lhongyi-ai/AI_Goggles/v2_chipdown/reports/changed_files.md

# Phase 1 Changed Files

Audit-generated files only. No KiCad schematic/footprint/PCB edits were made in Phase 1.

- `v2_chipdown/config/hardware_mechanical_database.yaml`
- `v2_chipdown/config/hardware_mechanical_database.csv`
- `v2_chipdown/reports/design_review.md`
- `v2_chipdown/reports/mechanical_open_items.md`
- `v2_chipdown/reports/mechanical_freeze_matrix.csv`
- `v2_chipdown/reports/mechanical_freeze_matrix.xlsx`
- `v2_chipdown/reports/footprint_audit.csv`
- `v2_chipdown/reports/symbol_to_footprint_mapping.csv`
- `v2_chipdown/reports/interconnect_matrix.csv`
- `v2_chipdown/reports/interconnect_matrix.md`
- `v2_chipdown/reports/phase_reports/phase_1_audit.md`
- `v2_chipdown/reports/phase_reports/phase_2_supplier_data_freeze.md`
- `v2_chipdown/reports/phase_reports/phase_3_database_pdf_report.md`
- `v2_chipdown/reports/phase_reports/phase_4_kicad_update_decision.md`
- `v2_chipdown/reports/phase_reports/phase_5_release_gate.md`
- `v2_chipdown/reports/drc_report.txt`
- `v2_chipdown/reports/schematic_diff.md`
- `v2_chipdown/reports/engineering_reviews/*.md`
- `v2_chipdown/reports/output/mechanical_freeze/*`
- `v2_chipdown/reports/AI_Glasses_Hardware_Dimensions_and_Performance_V2.3.md`
- `v2_chipdown/reports/output/AI_Glasses_Hardware_Dimensions_and_Performance_V2.3.pdf`
