lhongyi-ai/AI_Goggles/v2_chipdown/reports/drc_report.txt

DRC report generated by Phase 1 audit on 2026-07-01

NOT RUN: V2 chipdown project currently has no .kicad_pcb file.
This is intentional: formal PCB placement/routing is blocked by Gate 0 / G00F.
A real DRC can only be run after the no-route floorplan or formal PCB file exists.

Current available electrical evidence:
- v2_chipdown/reports/erc.report.txt: 0 errors / 0 warnings on 2026-07-01T01:26:33.
- kicad-cli was not available in this shell session, so ERC was not rerun in this phase.
