lhongyi-ai/AI_Goggles/v2_chipdown/reports/mechanical_open_items.md

# V2.3 Mechanical Open Items

Generated: 2026-07-01

所有条目遵守同一规则：没有 exact MPN、package drawing、pinout、land pattern 和最大高度时，不允许进入 release-ready footprint 或正式 layout。

| Item | Current value | Why it is not frozen | Missing document | Responsible party | Supplier question | Blocking effect | Closure condition | Deadline priority |
|---|---|---|---|---|---|---|---|---|
| RK806S-5 package / height | TBD | exact package/height missing | Rockchip/Radxa PMIC drawing | EE | 请提供 RK806S-5 封装图、推荐 land pattern、最大高度、热焊盘和参考电源时序。 | Blocks PMIC placement/height/rail layout | Official package drawing + land pattern + rail sequence reviewed | P0 |
| LPDDR4X exact MPN / size / ball map | TBD | memory MPN not selected | LPDDR vendor datasheet + ball map | EE/Sourcing | 请给出 Radxa/Rockchip 已验证 4GB LPDDR4X AVL 料号、封装和 ball map。 | Blocks DDR escape and board layer proof | MPN + package + ball map + DDR topology + length report | P0 |
| eMMC exact MPN / package | TBD | eMMC MPN not selected | eMMC datasheet/package drawing | EE/Sourcing | 请给出 32GB eMMC 5.1 AVL 料号、封装、VCC/VCCQ 和 boot validation。 | Blocks boot/storage layout | MPN + package + BSP boot validation | P0 |
| IMX415 lens / PCB / FPC / total Z | Current schematic custom module; V2.3 PDF proposes Radxa AS001 32.5 x 32.5 x 18.0 | architecture mismatch | final module drawing and pinout | EE/CAD/Supplier | 当前是否接受 32mm Radxa AS001 作为 EVT 机械基线，还是坚持 custom small FPC module？ | Blocks front frame CAD and J3 pinout | Approved module drawing + lens/FPC/mounting + schematic/BOM update if changed | P0 |
| Wi-Fi antenna | TBD | antenna SKU/keep-out not frozen | antenna vendor drawing + tune report | RF/CAD | 请提供天线尺寸、塑胶窗口、no-copper keep-out、同轴/FPC 出线和佩戴状态调谐要求。 | Blocks G14 and rear temple layout | Worn-state antenna tune + keep-out in CAD/PCB | P0 |
| BLE antenna | TBD | antenna SKU/keep-out not frozen | antenna vendor drawing + tune report | RF/CAD | 请提供 BLE 天线尺寸、净空和 nRF 匹配网络要求。 | Blocks left rear layout | Antenna SKU + keep-out + matching + tune report | P0 |
| main speaker | TBD | MPN/cavity/magnet unknown | speaker datasheet + acoustic cavity drawing | Acoustic/CAD | 请提供 8ohm 0.5-1W speaker 的长宽高、磁体、出音孔、声腔和防水网要求。 | Blocks right rear speaker/RF/battery layout | Speaker MPN + cavity + antenna magnet clearance passed | P0 |
| optional second speaker | DNP | not needed in EVT-A but may consume volume | speaker decision | PM/Acoustic | EVT-A 是否删除左侧第二 speaker 机械预留？ | May block left battery/BLE antenna if kept | DNP exclusion confirmed or cavity allocated | P1 |
| vibration motor | DNP | DNP, no MPN | motor datasheet | PM/ME | EVT-A 是否完全删除马达预留？ | Can disturb IMU/mic and consume rear volume | DNP exclusion confirmed or MPN/keep-out supplied | P1 |
| USB-C connector | EVT debug tail candidate | exact connector missing | USB-C connector drawing | EE/ME | 请冻结 EVT debug tail Type-C mid-mount MPN 或确认量产只用 pogo。 | Blocks debug tail mechanical opening | MPN + height + shell opening | P1 |
| magnetic pogo connector | target about 10 x 3 mm | target only | pogo supplier drawing | EE/ME | 请提供 4-6pin pogo 的针距、高度、电流、接触电阻、磁极、防汗腐蚀和寿命。 | Blocks charge/service rear layout and safety | MPN + pinout + current/fault/ESD validation | P0 |
| hinge FPC | 6-10 mm wide, 0.10-0.18 mm thick target | custom stack-up/pinout unknown | FPC vendor stack-up and impedance report | EE/ME/FPC | 请提供 fixed-temple EVT cable/FPC 方案，或 folding hinge FPC 的 pin count、铜厚、弯折半径和寿命。 | Blocks J4 current/signal integrity and hinge CAD | Pinout + current rating + impedance + bend test | P0 |
| Boost inductor | <=5 x 5 x 2 mm target | MPN/Isat/DCR/thermal unknown | inductor datasheet | EE | 请按 TPS61088、RK3576 boot/AI 峰值电流选择 L1，提供 Isat/DCR/温升。 | Blocks SOC_5V boost layout and thermal | Selected MPN passes peak/droop/thermal | P0 |
| FH26W exact pin count | 35 pin example only | final camera/audio/power split unknown | Hirose drawing + interconnect matrix | EE | 请根据 MIPI lane、PDM、I2C、GPIO、电源/GND 确认 pin count 和 contact side。 | Blocks J3 footprint and front FPC | Pin count/contact orientation + impedance checked | P0 |
| RF connector exact MPN | U.FL/I-PEX class | exact MPN/height/mating unknown | Hirose/I-PEX drawing | RF/EE | EVT 是否保留 RF debug connector？若保留，请冻结 MPN 和高度。 | Can collide with shell/antenna window | MPN + height + mating-life approved | P1 |
| system button | low-profile button/test pad | exact mechanical actuator missing | button datasheet / ID decision | EE/ME | Power/Recovery/MaskROM 是否做真实侧按键，还是全部隐藏为 pogo test pads？ | Blocks side wall openings and sealing | MPN/opening/debounce/service plan | P1 |
| battery pack drawing | 70 x 12.8 x 5.6 mm envelope | supplier max/tolerance/swell not official | cell/pack drawing + certs | Battery supplier | 请提供最大尺寸、公差、极耳/线材/PCM/NTC位置、膨胀、IR、倍率和认证。 | Blocks battery bay and 1S2P safety | Supplier drawing + dummy/real-cell fit test | P0 |
| battery tab and cable exit | TBD | tab/cable direction unknown | battery pack drawing | Battery supplier/CAD | 请明确极耳/出线方向和最小弯折/应力释放。 | Can collide with speaker/FPC/pogo | Pack drawing + strain-relief CAD | P0 |
| battery NTC | 10k NTC TBD curve | B-value/package/placement unknown | NTC datasheet + charger config | EE/Battery | 请确认 10k NTC B 值、封装/探头形式、贴附位置和 nPM1300 JEITA 配置。 | Blocks charge safety | Curve + nPM1300 config + per-cell placement | P0 |
| battery protection | pack PCM baseline or BQ2970 DNP fallback | single protection scheme not frozen | pack PCM spec or BQ2970 suffix/MOSFET | EE/Battery | 请确认用供应商 PCM 还是板上 BQ2970+MOSFET，不允许两套冲突。 | Blocks pack fault behavior and BOM | One protection scheme selected and tested | P0 |
| all connector mating heights | mixed TBD | J1/J3/J4/J5/USB heights incomplete | connector drawings | EE/ME | 请提供所有连接器 mating height、stiffener/FPC厚度和装配方向。 | Blocks Z-height and shell closure | All connector 3D envelopes in CAD | P0 |
