lhongyi-ai/AI_Goggles/v2_chipdown/mechanical_3d/reports/z_stack_report.md

# Z-stack report

| Section | Stack / max height | Status |
|---|---:|---|
| RK806S-5 | 0.90 mm body + solder + clearance | package candidate, sequence HOLD |
| eMMC KLMAG1JENB-B041 | 0.80 mm body + solder + clearance | candidate, BSP validation HOLD |
| FCU760K | 2.00 mm module + clearance | HOLD pending Quectel design package |
| Boost inductor XGL4020 | 2.00 mm + keep-out below | HOLD pending thermal/droop |
| Speaker CMS-15113 | 3.00 mm + foam/cavity | acoustic EVT HOLD |
| Battery envelope | 5.60 mm max + supplier swell/foam | HOLD supplier pack drawing |
| IMX415 camera | target <=9.5 mm total Z | TBD, not released for tooling |
| Hard components | >=0.3 mm worst-case clearance | rule carried into CAD checks |
