lhongyi-ai/AI_Goggles/v2_chipdown/reports/engineering_reviews/mass_and_balance.md

# Mass And Balance Review

Verdict: **HOLD**.

- Left temple mass: BT2 about 6 g estimated plus AON PCB; exact mass TBD.
- Right temple mass: BT1 about 6 g estimated plus RK3576 compute, Wi-Fi and speaker, likely heavier than left.
- Front frame mass: camera/lens choice dominates. Radxa AS001-style 32 mm board is much larger than a custom small FPC module.
- Center of gravity: right front compute pod may pull glasses forward/right unless left mass or frame geometry balances it.
- Left-right imbalance: target should be measured with dummy cells/PCBs/speaker/camera before ID tooling.
- Action: create mass spreadsheet once MPNs, PCBs and shell CAD have weights.
