lhongyi-ai/AI_Goggles/v2_chipdown/reports/phase_reports/phase_1_audit.md

# Phase 1 Audit Report

Generated: 2026-07-01

Scope: audit only. No KiCad schematic, symbol, footprint, PCB or 3D model files were modified by this phase.

## Evidence Reviewed

- Current schematic/BOM source: `v2_chipdown/scripts/chipdown_bom.py`.
- Current KiCad schematic: `v2_chipdown/hardware/ai_glasses_v2_chipdown.kicad_sch`.
- Existing ERC report: `v2_chipdown/reports/erc.report.txt` shows 0 errors / 0 warnings on 2026-07-01T01:26:33.
- Existing Phase 1.5 floorplan render/report.
- Symbol/footprint audit: `v2_chipdown/reports/symbol_to_footprint_mapping.csv`.
- Interconnect audit: `v2_chipdown/reports/interconnect_matrix.csv` and `.md`.
- Attached dimensions PDFs: `/Users/stanley/Downloads/AI_Glasses_Hardware_Dimensions_V2.2 (3).pdf` and `/Users/stanley/Downloads/AI_Glasses_Hardware_Dimensions_V2.3.pdf`.
- Local HOLD closure pack under `AI_Glasses_HOLD_Closure_Pack/`.

## Database Status Counts

| Status | Count |
|---|---|
| DNP | 19 |
| Fit | 39 |
| HOLD | 15 |
| PROVISIONAL | 16 |
| TBD | 9 |

## Phase 1 Verdict

- Schematic is useful for review and procurement, but PCB layout is **HOLD**.
- Major blockers: left side/sections missing, compute routability unproven, 1S2P/J4 safety not proven, RF/speaker/battery/camera mechanical data incomplete.
- The external V2.3 dimensions PDF camera baseline is not fully aligned with the current schematic because U14 is still a custom IMX415 FPC module in HOLD.

## Next Phase Gate

Do not enter Phase 2 freeze or Phase 4 KiCad modification until supplier documents are gathered for the P0 open items, especially RK806S, LPDDR4X, eMMC, battery pack, J3/J4, antennas, speaker and camera module.
