lhongyi-ai/AI_Goggles/v2_chipdown/reports/phase_reports/phase_3_database_pdf_report.md

# Phase 3 Database And PDF Report

Generated: 2026-07-01

Verdict: **PASS WITH CONDITIONS** for documentation generation, **HOLD** for mechanical freeze.

The single source used by reports is `v2_chipdown/config/hardware_mechanical_database.yaml`, generated from the current schematic/BOM plus conservative source overlays.

## Generated Database / Report Artifacts

| Artifact | Purpose |
|---|---|
| hardware_mechanical_database.yaml/csv | source-bound dimensions, power notes, statuses and next actions |
| AI_Glasses_Hardware_Dimensions_and_Performance_V2.3.md/pdf | human-readable hardware dimension/performance report with component cards |
| AI_Glasses_V2_3_Mechanical_Views.svg/png/pdf | 16 required schematic-aligned mechanical views |
| mechanical_freeze_matrix.xlsx/csv | P0/P1 open items and closure conditions |

Current status counts:

| Status | Count |
|---|---|
| DNP | 19 |
| Fit | 39 |
| HOLD | 15 |
| PROVISIONAL | 16 |
| TBD | 9 |
