lhongyi-ai/AI_Goggles/v2_chipdown/reports/phase_reports/phase_4_kicad_update_decision.md

# Phase 4 KiCad Update Decision

Generated: 2026-07-01

Verdict: **HOLD / NO KiCad EDITS IN THIS RUN**.

Reason: the prompt explicitly forbids release-ready footprint or schematic changes when exact MPN, package drawing, pinout, land pattern and max height are missing. The current project still has P0 blockers for RK806S, LPDDR4X, eMMC, camera module, antennas, speaker, pogo, J3/J4, boost inductor and battery pack drawing.

## KiCad Audit Evidence Generated

| Artifact | Result |
|---|---|
| symbol_to_footprint_mapping.csv | 96 schematic components mapped to current footprint fields and release-readiness status |
| footprint_audit.csv | NOT_FOR_FAB requirements flagged for VERIFY/HOLD/TBD/DNP items |
| interconnect_matrix.csv/md | 127 schematic nets with endpoints, domains, crossing status and layout rules |
| schematic_diff.md | confirms no KiCad schematic edits were made |

Allowed future KiCad action: create HOLD placeholders or a no-route mechanical floorplan only after the team approves that output as non-fabrication evidence. Do not replace current functional symbols with vendor pin-level symbols until ball maps/pinouts are official.
