lhongyi-ai/AI_Goggles/v2_chipdown/reports/phase_reports/phase_5_release_gate.md

# Phase 5 ERC / DRC / 3D / Release Gate

Generated: 2026-07-01

Overall verdict: **NOT READY FOR PCB LAYOUT**.

## Electrical / Layout Checks

| Check | Status | Evidence / blocker |
|---|---|---|
| ERC | PASS on existing report | `v2_chipdown/reports/erc.report.txt` shows 0 errors / 0 warnings on 2026-07-01T01:26:33; `kicad-cli` unavailable here, so not rerun |
| DRC | NOT RUN | V2 has no `.kicad_pcb`; DRC requires at least a no-route or formal PCB file |
| 3D collision | NOT RUN | No verified STEP/3D model set aligned to V2 KiCad footprints |
| Thermal | HOLD | RK3576/RK806/TPS61088 heat path and battery isolation require CAD/thermal review |
| RF | HOLD | Wi-Fi/BLE antenna SKU, keep-out and worn-state tune missing |
| Battery/J4 safety | HOLD | 1S2P branch protection/current capacity/fault behavior not frozen |

PCB layout may start only as a controlled floorplan study. Formal routing/fab release remains blocked until all P0 closure conditions in `mechanical_open_items.md` are closed.
