lhongyi-ai/AI_Goggles/docs/csi3_imx415_audit_2026-06-28.md

# CSI3 / IMX415 Audit

Date: 2026-06-28

Native sources used:

- `data/radxa_cm4_pinout_v1.20.xlsx`
- `CM4_IMX415_design_files/Radxa_Camera_4K_31pin_pinout.csv`
- `scripts/cm4_pinmap.py`
- `scripts/carrier_bom.py`
- `hardware/ai_glasses_carrier.kicad_sch` generated from `scripts/carrier_bom.py`

## Schematic Gate Summary

| Gate | Status | Evidence |
| --- | --- | --- |
| J2 Pin 1-31 pinout | PASS | Checked against Radxa Camera 4K 31-pin CSV and `scripts/carrier_bom.py`. |
| MIPI lane order | PASS | `MDP/MDN1..4` map to CSI3 D0..D3; `MCP/MCN` map to CSI3 clock. |
| P/N polarity | PASS | Every FPC `P` signal lands on `_P`, every `N` signal lands on `_N`. |
| I2C/MCLK/RESET | PASS | SCL/SDA/MCLK/RESET_N map to verified CM4 pins and functions below. |
| Voltage domains | PASS | Control IO is 1.8V; J2 supplies are +CAM_3V3 and +5V_SYS. |
| Power and NC pins | PASS | GND, VCC3.3V, VCC5V and NC pins are explicitly checked below. |
| ERC warnings | PASS | 0 ERC violation(s). There are no active ERC warnings to explain. |

## J2 Pin 1-31 Electrical Check

| Pin | FPC signal | Schematic label | Board net | Role | Voltage / domain | Result |
| ---: | --- | --- | --- | --- | --- | --- |
| 1 | `GND` | `GND` | `GND` | ground | GND | PASS. |
| 2 | `MDN4` | `MDN4` | `MIPI_CSI3_D3_N` | mipi_lane | CSI3 D-PHY | PASS. Lane 3 negative. |
| 3 | `MDP4` | `MDP4` | `MIPI_CSI3_D3_P` | mipi_lane | CSI3 D-PHY | PASS. Lane 3 positive. |
| 4 | `GND` | `GND` | `GND` | ground | GND | PASS. |
| 5 | `MDN3` | `MDN3` | `MIPI_CSI3_D2_N` | mipi_lane | CSI3 D-PHY | PASS. Lane 2 negative. |
| 6 | `MDP3` | `MDP3` | `MIPI_CSI3_D2_P` | mipi_lane | CSI3 D-PHY | PASS. Lane 2 positive. |
| 7 | `GND` | `GND` | `GND` | ground | GND | PASS. |
| 8 | `NC` | `NC` | `NC` | no_connect | unconnected | PASS. |
| 9 | `NC` | `NC` | `NC` | no_connect | unconnected | PASS. |
| 10 | `GND` | `GND` | `GND` | ground | GND | PASS. |
| 11 | `MDN2` | `MDN2` | `MIPI_CSI3_D1_N` | mipi_lane | CSI3 D-PHY | PASS. Lane 1 negative. |
| 12 | `MDP2` | `MDP2` | `MIPI_CSI3_D1_P` | mipi_lane | CSI3 D-PHY | PASS. Lane 1 positive. |
| 13 | `GND` | `GND` | `GND` | ground | GND | PASS. |
| 14 | `MDN1` | `MDN1` | `MIPI_CSI3_D0_N` | mipi_lane | CSI3 D-PHY | PASS. Lane 0 negative. |
| 15 | `MDP1` | `MDP1` | `MIPI_CSI3_D0_P` | mipi_lane | CSI3 D-PHY | PASS. Lane 0 positive. |
| 16 | `GND` | `GND` | `GND` | ground | GND | PASS. |
| 17 | `MCN` | `MCN` | `MIPI_CSI3_CLK_N` | mipi_clock | CSI3 D-PHY | PASS. Clock negative. |
| 18 | `MCP` | `MCP` | `MIPI_CSI3_CLK_P` | mipi_clock | CSI3 D-PHY | PASS. Clock positive. |
| 19 | `GND` | `GND` | `GND` | ground | GND | PASS. |
| 20 | `MCLK` | `MCLK` | `CAM_MCLK` | clock | 1.8V | PASS. CM4 CAM_CLK2_OUT_M0. |
| 21 | `GND` | `GND` | `GND` | ground | GND | PASS. |
| 22 | `NC` | `NC` | `NC` | no_connect | unconnected | PASS. |
| 23 | `NC` | `NC` | `NC` | no_connect | unconnected | PASS. |
| 24 | `SCL` | `SCL` | `CAM_I2C_SCL` | i2c | 1.8V | PASS. Pulled up to +1V8 on carrier. |
| 25 | `SDA` | `SDA` | `CAM_I2C_SDA` | i2c | 1.8V | PASS. Pulled up to +1V8 on carrier. |
| 26 | `NC` | `NC` | `NC` | no_connect | unconnected | PASS. |
| 27 | `RESET` | `RESET_N` | `CAM_RST_n` | reset | 1.8V | PASS. Active-low reset. |
| 28 | `VCC3.3V` | `VCC3.3V` | `+CAM_3V3` | power | 3.3V | PASS. Generated by camera low-noise LDO. |
| 29 | `VCC3.3V` | `VCC3.3V` | `+CAM_3V3` | power | 3.3V | PASS. Generated by camera low-noise LDO. |
| 30 | `VCC5V` | `VCC5V` | `+5V_SYS` | power | 5V | PASS. System 5V rail with local decoupling. |
| 31 | `VCC5V` | `VCC5V` | `+5V_SYS` | power | 5V | PASS. System 5V rail with local decoupling. |

## Lane Mapping

| Camera FPC | Board net | CM4 pin | CM4 XLSX primary net | Required RK3576 function | Result |
| --- | --- | ---: | --- | --- | --- |
| pin 18 `MCP` | `MIPI_CSI3_CLK_P` | 129 | `MIPI_DPHY_CSI3_RX_CLKP` | `MIPI_DPHY_CSI3_RX_CLKP` | PASS. |
| pin 17 `MCN` | `MIPI_CSI3_CLK_N` | 127 | `MIPI_DPHY_CSI3_RX_CLKN` | `MIPI_DPHY_CSI3_RX_CLKN` | PASS. |
| pin 15 `MDP1` | `MIPI_CSI3_D0_P` | 117 | `MIPI_DPHY_CSI3_RX_D0P` | `MIPI_DPHY_CSI3_RX_D0P` | PASS. |
| pin 14 `MDN1` | `MIPI_CSI3_D0_N` | 115 | `MIPI_DPHY_CSI3_RX_D0N` | `MIPI_DPHY_CSI3_RX_D0N` | PASS. |
| pin 12 `MDP2` | `MIPI_CSI3_D1_P` | 123 | `MIPI_DPHY_CSI3_RX_D1P` | `MIPI_DPHY_CSI3_RX_D1P` | PASS. |
| pin 11 `MDN2` | `MIPI_CSI3_D1_N` | 121 | `MIPI_DPHY_CSI3_RX_D1N` | `MIPI_DPHY_CSI3_RX_D1N` | PASS. |
| pin 6 `MDP3` | `MIPI_CSI3_D2_P` | 135 | `MIPI_DPHY_CSI4_RX_D0P` | `MIPI_DPHY_CSI3_RX_D2P` | PASS. CM4 pinout primary net is CSI4_D0P; function list also exposes CSI3_D2P. |
| pin 5 `MDN3` | `MIPI_CSI3_D2_N` | 133 | `MIPI_DPHY_CSI4_RX_D0N` | `MIPI_DPHY_CSI3_RX_D2N` | PASS. CM4 pinout primary net is CSI4_D0N; function list also exposes CSI3_D2N. |
| pin 3 `MDP4` | `MIPI_CSI3_D3_P` | 141 | `MIPI_DPHY_CSI4_RX_D1P` | `MIPI_DPHY_CSI3_RX_D3P` | PASS. CM4 pinout primary net is CSI4_D1P; function list also exposes CSI3_D3P. |
| pin 2 `MDN4` | `MIPI_CSI3_D3_N` | 139 | `MIPI_DPHY_CSI4_RX_D1N` | `MIPI_DPHY_CSI3_RX_D3N` | PASS. CM4 pinout primary net is CSI4_D1N; function list also exposes CSI3_D3N. |

## Control Voltage Audit

| Signal | CM4 pin | CM4 net | Function | Voltage conclusion | Result |
| --- | ---: | --- | --- | --- | --- |
| `I2C_CAM_SCL` | 80 | `I2C0_SCL_M1_TP` | `I2C0_SCL_M1` | 1.8V; board pulls control I/O to +1V8 where applicable | PASS |
| `I2C_CAM_SDA` | 82 | `I2C0_SDA_M1_TP` | `I2C0_SDA_M1` | 1.8V; board pulls control I/O to +1V8 where applicable | PASS |
| `CAM_MCLK` | 59 | `MIPI_CSI3_CAM_CLKOUT_1V8` | `CAM_CLK2_OUT_M0` | 1.8V; board pulls control I/O to +1V8 where applicable | PASS |
| `CAM_RST_n` | 143 | `MIPI_CAM3_PDN_1V8` | `GPIO3_C5` | 1.8V; board pulls control I/O to +1V8 where applicable | PASS |

## Conclusions

- The 4-lane camera connection is a CSI3 endpoint, but CM4 pins 133/135/139/141 are named as CSI4 primary nets in the pinout while also listing CSI3 D2/D3 functions. Treat this as a documented CSI3/CSI4 mux alias, and mirror the same lane order in Device Tree.
- Camera I2C, MCLK and RESET control are all carried as 1.8 V signals in the current source plan.
- `CAM_RST_n` is the project net name and is active-low. The Radxa Camera 4K FPC pin 27 label is `RESET`; the schematic symbol marks it as `RESET_N`.
- Radxa Camera 4K exposes RESET but no PWDN pin in the local 31-pin pinout CSV.
- J2 pins 28/29 are tied to `+CAM_3V3`; J2 pins 30/31 are tied to `+5V_SYS`. Both rails are present because the Radxa Camera 4K 31-pin pinout exposes both supplies.
- J2 pins 8/9/22/23/26 are intentional `NC` pins and the generated KiCad schematic emits no-connect markers for them.

## DEFERRED_TO_PRE_LAYOUT

These items are explicitly not closed by the schematic electrical gate:

| ID | Item | Status |
| --- | --- | --- |
| `AC006_PHYSICAL_VALIDATION` | AC006实物验证 | `DEFERRED_TO_PRE_LAYOUT` |
| `FPC_CONTACT_SIDE` | FPC接触面 | `DEFERRED_TO_PRE_LAYOUT` |
| `FPC_INSERTION_DIRECTION` | 插入方向 | `DEFERRED_TO_PRE_LAYOUT` |
| `J2_PIN1_PHYSICAL_CHECK` | Pin 1实体核对 | `DEFERRED_TO_PRE_LAYOUT` |
| `J2_1TO1_PRINT_CHECK` | 1:1打印 | `DEFERRED_TO_PRE_LAYOUT` |
| `J2_COUPON_TEST` | Coupon测试 | `DEFERRED_TO_PRE_LAYOUT` |
| `FPC_BEND_AND_ENCLOSURE_PATH` | FPC弯折和外壳路径 | `DEFERRED_TO_PRE_LAYOUT` |
