lhongyi-ai/AI_Goggles/AI_Glasses_HOLD_Closure_Pack/00_Index_and_Action/公开来源与需登录资料.md

# 公开来源与需登录资料

## NDP120

- Public product page: https://www.syntiant.com/products/chips-and-hardware/ndp120/
- Product Brief: included in this package.
- Avnet RASynBoard product/development platform: https://www.avnet.com/apac/products/rasynboard/
- RASynBoard GitHub hub: https://github.com/Avnet/RASynBoard-HUB
- Full datasheet/SDK/model tools: contact Syntiant or authorized distributor; access may require account/NDA.

## FCU760K

- Official product page: https://www.quectel.com/product/wi-fi-bluetooth-fcu760k/
- Official download zone: https://www.quectel.com/download-zone/
- Official hardware-design landing page: https://www.quectel.com/download/quectel_fcu760k_hardware_design_v1-2/
- Public FCC copy of FCU760K hardware design: https://fccid.io/m/e89f187a4d2a5470e689b20ec0c0dcbc1a5c297cd725fd0425162547aa3b618d.pdf
- Driver/firmware package: request from Quectel FAE/download account.

## LP451165

- Public product page: https://www.lipolbattery.com/Lithium-ion-Polymer-Battery-300mAh-for-Wearable-Camera.html
- The public page is not a full engineering datasheet and does not publish exact rate curves. Request a signed/revision-controlled PDF from the supplier.

## nPM1300 / Pack profiling

- Product page: https://www.nordicsemi.com/Products/nPM1300
- Current fuel-gauge application note: https://www.nordicsemi.com/-/media/Images/Products/PMICs/nPM1300/nan_045.pdf
- Use nPM1300 EK + nPM Fuel Gauge Board to profile the final 1S2P pack.

## IMX415

- Sony product flyer: https://www.sony-semicon.com/files/62/pdf/p-12_IMX415-AAQR_AAMR_Flyer.pdf
- Full IMX415-AAQR-C datasheet is included in this package.
- FRAMOS FSM-IMX415 module reference: https://framos.com/wp-content/uploads/2022/06/FSM-IMX415-Datasheet.pdf
