lhongyi-ai/AI_Goggles/AI_Glasses_HOLD_Closure_Pack/04_IMX415/IMX415_相机电源预算与模组索资.md

# IMX415 相机电源预算与定制模组索资

## Sony Sensor 本体数据

Sony IMX415-AAQR-C Datasheet 的 Current Consumption 表给出：

| 电源 | 典型电流 | 最大电流 |
|---|---:|---:|
| AVDD 2.9 V | 128 mA | 156 mA |
| IOVDD 1.8 V | 3 mA | 3 mA |
| DVDD 1.1 V | 187 mA | 250 mA |

测试模式为 MIPI CSI-2 4-lane、2079 Mbps、12-bit、60 fps、all-pixel。

### 功率计算

典型条件：

`2.9*0.128 + 1.8*0.003 + 1.1*0.187 = 0.5823 W`

最大电流、最大供电角：

`3.0*0.156 + 1.9*0.003 + 1.2*0.250 = 0.7737 W`

Standby 最大电流为 0.2 mA / 0.2 mA / 15.1 mA；按最大电压角约 19.1 mW。该值仍明显高于真正断电，因此休眠时应通过 Load Switch 切断相机轨。

## 重要限制

上述仅是 Sensor 芯片，不包括：

- 外部时钟/晶振。
- 模组 LDO/Buck 损耗。
- EEPROM、AF/IR-cut（若有）。
- FPC 压降和 ESD。
- 镜头相关执行器。
- 前框状态灯或其他器件。

因此定制相机模块不能用“IMX415约0.6 W”直接冻结整岛预算。

## 向相机模组供应商索取

1. 完整模组原理图或至少 Power Tree。
2. FPC pinout、连接器料号、机械图和最大高度。
3. 2-lane/4-lane支持模式和目标1080p30/60配置。
4. AVDD/IOVDD/DVDD 每轨典型、峰值和上电浪涌。
5. 时钟源、电压和电流。
6. RST/PWDN/供电时序。
7. Standby、streaming、模式切换功耗。
8. Lens FOV、畸变、M12/定焦结构、IR filter。
9. BSP sensor driver、register table、ISP tuning文件。
10. ESD/EMI和温度范围。

## EVT 测量

在每个相机轨串 Kelvin Shunt：CAM_1V1、CAM_1V8、CAM_2V9。记录：

- Power-on rush。
- Reset release。
- Idle/standby。
- 1080p30、1080p60。
- 4K30/60（仅作为边界）。
- 低照度/高增益。
- Stream off后的漏电。

## HOLD 关闭门槛

- 定制模组 MPN、机械图和 FPC pinout 冻结。
- 1080p目标模式在RK3576 BSP稳定运行。
- 三轨峰值和平均功耗实测完成。
- 断电后不存在 I2C/MIPI/GPIO 反灌。
- 前框温升和FPC压降通过。
