lhongyi-ai/AI_Goggles/v2_chipdown/docs/08_signal_dictionary.md

# 08 — Signal dictionary (generated)

> Generated 2026-07-01 from `scripts/chipdown_bom.py`. Do not hand-edit. Every row is a net-level `NET_META` record normalized by `net_meta()`.

**133 nets**. Signal attributes cover name, source, destination, direction, voltage domain, default state, pulls, powered-off behavior, debug series parts, ESD, differential pairing, pinmux, device-tree/driver owner, and isolation notes.

## Rules

- `_L` means active low. `EN` and `PGOOD` are active high.
- Any row with `Cross-domain = yes` must pass reverse-feed/off-leakage review before layout.
- Defaults marked `low (OFF)` are backed by physical pull-downs where listed in `11/12`.
- `TBD` attributes are allowed only while the owning gate remains open.

## Power nets (35)

| Net | Full name | From | To | Direction | Domain | Default | Pull | Off-high allowed | Series / ESD / Diff | Pinmux / DT / Driver | Notes |
|---|---|---|---|---|---|---|---|---|---|---|---|
| `GND` | GND | source | loads | source->loads | 0V | 0V | none / TBD | N/A | none / no / TBD / no | none / TBD / none / TBD / none / TBD | derived from endpoints; verify at the owning gate |
| `VDD_CPU` | VDD CPU | RK806S rail | loads | source->loads | RK806 rail (TBD) | off until owning regulator is enabled | none / TBD | N/A | none / no / TBD / no | none / TBD / none / TBD / none / TBD | derived from endpoints; verify at the owning gate |
| `VDD_GPU` | VDD GPU | RK806S rail | loads | source->loads | RK806 rail (TBD) | off until owning regulator is enabled | none / TBD | N/A | none / no / TBD / no | none / TBD / none / TBD / none / TBD | derived from endpoints; verify at the owning gate |
| `VDD_NPU` | VDD NPU | RK806S rail | loads | source->loads | RK806 rail (TBD) | off until owning regulator is enabled | none / TBD | N/A | none / no / TBD / no | none / TBD / none / TBD / none / TBD | derived from endpoints; verify at the owning gate |
| `VDD_LOGIC` | VDD LOGIC | RK806S rail | loads | source->loads | RK806 rail (TBD) | off until owning regulator is enabled | none / TBD | N/A | none / no / TBD / no | none / TBD / none / TBD / none / TBD | derived from endpoints; verify at the owning gate |
| `VDD_DDR` | VDD DDR | RK806S rail | loads | source->loads | RK806 rail (TBD) | off until owning regulator is enabled | none / TBD | N/A | none / no / TBD / no | none / TBD / none / TBD / none / TBD | derived from endpoints; verify at the owning gate |
| `VCC_DDRIO` | VCC DDRIO | RK806S rail | loads | source->loads | 1.8V | off until owning regulator is enabled | none / TBD | N/A | none / no / TBD / no | none / TBD / none / TBD / none / TBD | derived from endpoints; verify at the owning gate |
| `VCCIO_1V8` | VCCIO 1V8 | RK806S rail | loads | source->loads | 1.8V | off until owning regulator is enabled | none / TBD | N/A | none / no / TBD / no | none / TBD / none / TBD / none / TBD | derived from endpoints; verify at the owning gate |
| `VCC_3V3` | VCC 3V3 | RK806S rail | loads | source->loads | 3.3V | off until owning regulator is enabled | none / TBD | N/A | none / no / TBD / no | none / TBD / none / TBD / none / TBD | derived from endpoints; verify at the owning gate |
| `SOC_5V` | SOC 5V | TPS61088 boost output | loads | source->loads | 5V | off | none / TBD | N/A | none / no / TBD / no | nRF GPIO/UART + RK3576 GPIO/UART DT / power-state handshake + uart node / nRF app + Linux GPIO/UART | TPS61088 boost, gated |
| `SOC_IN` | SOC IN | RS4 from VSYS | loads | source->loads | Vbat | off until owning regulator is enabled | none / TBD | N/A | none / no / TBD / no | nRF GPIO/UART + RK3576 GPIO/UART DT / power-state handshake + uart node / nRF app + Linux GPIO/UART | derived from endpoints; verify at the owning gate |
| `WIFI_VBAT_3V3` | WIFI VBAT 3V3 | TPS22917 Wi-Fi load-switch output | loads | source->loads | 3.3V | off | none / TBD | N/A | none / no / TBD / no | none / TBD / none / TBD / none / TBD | FCU760K VBAT, load-switched |
| `WIFI_IN` | WIFI IN | RS5 from VSYS | loads | source->loads | Vbat | off until owning regulator is enabled | none / TBD | N/A | none / no / TBD / no | none / TBD / none / TBD / none / TBD | derived from endpoints; verify at the owning gate |
| `WIFI_3V3` | WIFI 3V3 | TPS62825 output | loads | source->loads | 3.3V | off | none / TBD | N/A | none / no / TBD / no | none / TBD / none / TBD / none / TBD | TPS62825 buck, gated |
| `USB_5V` | USB 5V | USB-C or magnetic pogo VBUS | loads | source->loads | 5V | ext | none / TBD | N/A | none / VBUS ESD/OV strategy required / no | none / TBD / none / TBD / none / TBD | protected VBUS into BQ25895/nPM1300 sense |
| `VSYS` | VSYS | nPM1300 power-path output | loads | source->loads | Vbat | live | none / TBD | N/A | none / no / TBD / no | none / TBD / none / TBD / none / TBD | nPM1300 power-path system node |
| `NPM_VBAT` | NPM VBAT | RS1 pack-total shunt | loads | source->loads | Vbat | live | none / TBD | N/A | none / no / TBD / no | none / TBD / none / TBD / none / TBD | nPM1300 VBAT (after RS1 total shunt) |
| `VBUS_RAW` | VBUS RAW | USB-C or magnetic pogo before input protection | loads | source->loads | 5V | ext | none / TBD | N/A | none / no / TBD / no | none / TBD / none / TBD / none / TBD | raw pogo/USB-C VBUS before eFuse/OVP |
| `AON_1V8` | AON 1V8 | nPM1300 BUCK1 | loads | source->loads | 1.8V | on | none / TBD | N/A | none / no / TBD / no | none / TBD / none / TBD / none / TBD | always-on nPM1300 BUCK1 |
| `AON_3V3` | AON 3V3 | nPM1300 BUCK2 | loads | source->loads | 3.3V | on | none / TBD | N/A | none / no / TBD / no | none / TBD / none / TBD / none / TBD | always-on nPM1300 BUCK2 |
| `AON_LSW2` | AON LSW2 | nPM1300 load switch 2 | loads | source->loads | TBD | on/live in AON mode | none / TBD | N/A | none / no / TBD / no | none / TBD / none / TBD / none / TBD | derived from endpoints; verify at the owning gate |
| `CAM_1V1_S` | CAM 1V1 S | RS7 Kelvin sense output to camera DVDD | loads | source->loads | 1.1V | off until owning regulator is enabled | none / TBD | N/A | none / no / TBD / no | none / TBD / none / TBD / none / TBD | derived from endpoints; verify at the owning gate |
| `CAM_1V8_S` | CAM 1V8 S | RS8 Kelvin sense output to camera IOVDD | loads | source->loads | 1.8V | off until owning regulator is enabled | none / TBD | N/A | none / no / TBD / no | none / TBD / none / TBD / none / TBD | derived from endpoints; verify at the owning gate |
| `CAM_2V9_S` | CAM 2V9 S | RS9 Kelvin sense output to camera AVDD | loads | source->loads | 2.9V | off until owning regulator is enabled | none / TBD | N/A | none / no / TBD / no | none / TBD / none / TBD / none / TBD | derived from endpoints; verify at the owning gate |
| `CAM_1V1` | CAM 1V1 | TPS62840 output | loads | source->loads | 1.1V | off | none / TBD | N/A | none / no / TBD / no | none / TBD / none / TBD / none / TBD | IMX415 DVDD |
| `CAM_2V9` | CAM 2V9 | TLV75529 output | loads | source->loads | 2.9V | off | none / TBD | N/A | none / no / TBD / no | none / TBD / none / TBD / none / TBD | IMX415 AVDD |
| `CAM_1V8_SW` | CAM 1V8 SW | TPS22917 camera I/O load-switch output | loads | source->loads | 1.8V | off | none / TBD | N/A | none / no / TBD / no | none / TBD / none / TBD / none / TBD | IMX415 IOVDD |
| `AUDIO_PWR` | AUDIO PWR | TPS22917 audio load-switch output | loads | source->loads | Vbat | off | none / TBD | N/A | none / no / TBD / no | none / TBD / none / TBD / none / TBD | Class-D amp, gated |
| `AUDIO_IN` | AUDIO IN | RS6 from VSYS | loads | source->loads | Vbat | off until owning regulator is enabled | none / TBD | N/A | none / no / TBD / no | none / TBD / none / TBD / none / TBD | derived from endpoints; verify at the owning gate |
| `BATR_P` | BATR P | right LP451165 cell | loads | source->loads | Vbat | on/live in AON mode | none / TBD | N/A | none / no / TBD / no | none / TBD / none / TBD / none / TBD | derived from endpoints; verify at the owning gate |
| `CELL_NEG` | CELL NEG | source | loads | source->loads | Vbat | live | none / TBD | N/A | none / no / TBD / no | none / TBD / none / TBD / none / TBD | internal cell negative into supplier pack PCM; no board BQ2970 |
| `BATL_P` | BATL P | left LP451165 cell | loads | source->loads | Vbat | on/live in AON mode | none / TBD | N/A | none / no / TBD / no | none / TBD / none / TBD / none / TBD | derived from endpoints; verify at the owning gate |
| `BATR_F` | BATR F | F1 branch fuse | loads | source->loads | Vbat | on/live in AON mode | none / TBD | N/A | none / no / TBD / no | none / TBD / none / TBD / none / TBD | derived from endpoints; verify at the owning gate |
| `BATL_F` | BATL F | F2 branch fuse | loads | source->loads | Vbat | on/live in AON mode | none / TBD | N/A | none / no / TBD / no | none / TBD / none / TBD / none / TBD | derived from endpoints; verify at the owning gate |
| `BAT_P` | BAT P | RS2/RS3 branch shunts from LP451165 1S2P pack | loads | source->loads | Vbat | live | none / TBD | N/A | none / no / TBD / no | none / TBD / none / TBD / none / TBD | protected 1S2P pack + |

## Control nets (32)

| Net | Full name | From | To | Direction | Domain | Default | Pull | Off-high allowed | Series / ESD / Diff | Pinmux / DT / Driver | Notes |
|---|---|---|---|---|---|---|---|---|---|---|---|
| `PMIC_SLEEP` | PMIC SLEEP | U1.PMIC_SLEEP (R-Temple Compute Board) | U2.SLEEP (R-Temple Compute Board) | see endpoints | 1.8V unless final pinmux says otherwise | TBD at pinmux freeze | none / TBD | same-domain only | optional 0R debug / no / TBD / no | none / TBD / none / TBD / none / TBD | derived from endpoints; verify at the owning gate |
| `SOC_SHUTDOWN_REQ` | Linux shutdown request handshake | nRF | RK3576 | nRF->RK3576 | 1.8V | low | none / TBD | No; prove no reverse-feed or add isolation | optional 0R debug / no / TBD / no | nRF GPIO/UART + RK3576 GPIO/UART DT / power-state handshake + uart node / nRF app + Linux GPIO/UART | request Linux shutdown |
| `SOC_SAFE_TO_OFF` | Linux safe-to-remove-power handshake | RK3576 | nRF | RK3576->nRF | 1.8V | low | none / TBD | No; prove no reverse-feed or add isolation | optional 0R debug / no / TBD / no | nRF GPIO/UART + RK3576 GPIO/UART DT / power-state handshake + uart node / nRF app + Linux GPIO/UART | synced, safe to cut SOC_5V |
| `SOC_ALIVE` | RK3576 liveness heartbeat | RK3576 | nRF | RK3576->nRF | 1.8V | low | none / TBD | No; prove no reverse-feed or add isolation | optional 0R debug / no / TBD / no | nRF GPIO/UART + RK3576 GPIO/UART DT / power-state handshake + uart node / nRF app + Linux GPIO/UART | liveness |
| `SOC_FAULT` | RK3576 fault indication | RK3576 | nRF | RK3576->nRF | 1.8V | low | none / TBD | No; prove no reverse-feed or add isolation | optional 0R debug / no / TBD / no | nRF GPIO/UART + RK3576 GPIO/UART DT / power-state handshake + uart node / nRF app + Linux GPIO/UART | fault |
| `CAM_RST_L` | CAM RST L | RK3576 | cam | RK3576->cam | 1.8V | low (XCLR held) | none / TBD | No; prove no reverse-feed or add isolation | optional 0R debug / no / TBD / no | RK3576 camera pinmux; G10 module pinout / camera node + CSI/ISP graph / imx415 + rkisp | active low; hold low until rails+clock up (§24) |
| `CAM_PWDN_L` | CAM PWDN L | RK3576 | cam | RK3576->cam | 1.8V | low | none / TBD | No; prove no reverse-feed or add isolation | optional 0R debug / no / TBD / no | RK3576 camera pinmux; G10 module pinout / camera node + CSI/ISP graph / imx415 + rkisp | derived from endpoints; verify at the owning gate |
| `CAM_MCLK` | CAM MCLK | RK3576 | cam | RK3576->cam | 1.8V | off | none / TBD | No; prove no reverse-feed or add isolation | optional 0R debug / no / TBD / no | RK3576 camera pinmux; G10 module pinout / camera node + CSI/ISP graph / imx415 + rkisp | INCK; enable only after rails stable (§24) |
| `WIFI_WAKE_L` | WIFI WAKE L | U1.WIFI_WAKE_L (R-Temple Compute Board) | U11.WAKE (R-Temple Compute Board) | see endpoints | 1.8V unless final pinmux says otherwise | TBD at pinmux freeze | none / TBD | same-domain only | optional 0R debug / no / TBD / no | RK3576 USB2/PCM + nRF GPIO for CHIP_EN / usb host + optional bt-audio PCM / usbcore + Quectel firmware | derived from endpoints; verify at the owning gate |
| `SOC_MASKROM_L` | SOC MASKROM L | U1.MASKROM_n (R-Temple Compute Board) | SW3.A (EVT Debug Tail) | see endpoints | 1.8V unless final pinmux says otherwise | low or pulled to safe state until firmware owns it | none / TBD | No; prove no reverse-feed or add isolation | optional 0R debug / no / TBD / no | nRF GPIO/UART + RK3576 GPIO/UART DT / power-state handshake + uart node / nRF app + Linux GPIO/UART | derived from endpoints; verify at the owning gate |
| `SOC_RESET_L` | RK3576 reset, active low | nRF/btn | RK3576 | nRF/btn->RK3576 | 1.8V | low (reset) | none / TBD | No; prove no reverse-feed or add isolation | optional 0R debug / no / TBD / no | nRF GPIO/UART + RK3576 GPIO/UART DT / power-state handshake + uart node / nRF app + Linux GPIO/UART | active low |
| `SOC_PWRKEY` | SOC PWRKEY | U1.PWRKEY (R-Temple Compute Board) | SW1.A (EVT Debug Tail) | see endpoints | 1.8V unless final pinmux says otherwise | TBD at pinmux freeze | none / TBD | No; prove no reverse-feed or add isolation | optional 0R debug / no / TBD / no | nRF GPIO/UART + RK3576 GPIO/UART DT / power-state handshake + uart node / nRF app + Linux GPIO/UART | derived from endpoints; verify at the owning gate |
| `PMIC_PWRON` | RK806 PMIC power-on request | nRF | RK806 | nRF->RK806 | 1.8V | low (OFF) | 100k pulldown (R11-R20) | No; prove no reverse-feed or add isolation | optional 0R debug / no / TBD / no | nRF GPIO/UART + RK3576 GPIO/UART DT / power-state handshake + uart node / nRF app + Linux GPIO/UART | 100k pulldown; into SoC domain |
| `SOC_PWR_EN` | SoC 5V boost enable, active high | nRF | boost | nRF->boost | 1.8V | low (OFF) | 100k pulldown (R11-R20) | No; prove no reverse-feed or add isolation | optional 0R debug / no / TBD / no | nRF GPIO/UART + RK3576 GPIO/UART DT / power-state handshake + uart node / nRF app + Linux GPIO/UART | 100k pulldown |
| `SOC_5V_PGOOD` | SoC 5V boost power-good, active high | boost | nRF | boost->nRF | 1.8V | low | none / TBD | No; prove no reverse-feed or add isolation | optional 0R debug / no / TBD / no | nRF GPIO/UART + RK3576 GPIO/UART DT / power-state handshake + uart node / nRF app + Linux GPIO/UART | power-good in |
| `WIFI_CHIP_EN` | FCU760K chip enable, active high | nRF | FCU760K | nRF->FCU760K | 3.3V | low (OFF) | 100k pulldown (R11-R20) | No; prove no reverse-feed or add isolation | optional 0R debug / no / TBD / no | RK3576 USB2/PCM + nRF GPIO for CHIP_EN / usb host + optional bt-audio PCM / usbcore + Quectel firmware | 100k pulldown; module off default (pack §9) |
| `WIFI_BUCK_EN` | WIFI BUCK EN | nRF | buck | nRF->buck | 1.8V | low (OFF) | 100k pulldown (R11-R20) | No; prove no reverse-feed or add isolation | optional 0R debug / no / TBD / no | none / TBD / none / TBD / none / TBD | 100k pulldown |
| `WIFI_LS_EN` | WIFI LS EN | nRF | LSW | nRF->LSW | 1.8V | low (OFF) | 100k pulldown (R11-R20) | No; prove no reverse-feed or add isolation | optional 0R debug / no / TBD / no | none / TBD / none / TBD / none / TBD | 100k pulldown |
| `CHG_INT_L` | CHG INT L | U35.INT_L (R-Temple Compute Board) | U7.CHG_INT_L (L-Temple AON/Power Board) | see endpoints | 1.8V unless final pinmux says otherwise | TBD at pinmux freeze | none / TBD | No; prove no reverse-feed or add isolation | optional 0R debug / no / TBD / no | none / TBD / none / TBD / none / TBD | derived from endpoints; verify at the owning gate |
| `VBUS_FAULT_L` | VBUS FAULT L | U36.FLT_L (R-Temple Compute Board) | U7.VBUS_FAULT_L (L-Temple AON/Power Board) | see endpoints | 1.8V unless final pinmux says otherwise | TBD at pinmux freeze | none / TBD | No; prove no reverse-feed or add isolation | optional 0R debug / no / TBD / no | none / TBD / none / TBD / none / TBD | derived from endpoints; verify at the owning gate |
| `CAM_1V1_EN` | CAM 1V1 EN | nRF | buck | nRF->buck | 1.8V | low (OFF) | 100k pulldown (R11-R20) | No; prove no reverse-feed or add isolation | optional 0R debug / no / TBD / no | none / TBD / none / TBD / none / TBD | 100k pulldown |
| `CAM_1V8_EN` | CAM 1V8 EN | nRF | LSW | nRF->LSW | 1.8V | low (OFF) | 100k pulldown (R11-R20) | No; prove no reverse-feed or add isolation | optional 0R debug / no / TBD / no | none / TBD / none / TBD / none / TBD | 100k pulldown |
| `CAM_2V9_EN` | CAM 2V9 EN | nRF | LDO | nRF->LDO | 1.8V | low (OFF) | 100k pulldown (R11-R20) | No; prove no reverse-feed or add isolation | optional 0R debug / no / TBD / no | none / TBD / none / TBD / none / TBD | 100k pulldown |
| `AUDIO_LS_EN` | AUDIO LS EN | nRF | LSW | nRF->LSW | 1.8V | low (OFF) | 100k pulldown (R11-R20) | No; prove no reverse-feed or add isolation | optional 0R debug / no / TBD / no | none / TBD / none / TBD / none / TBD | 100k pulldown |
| `AUDIO_AMP_SD` | AUDIO AMP SD | nRF | amp | nRF->amp | Vbat | low (muted) | 100k pulldown (R11-R20) | No; prove no reverse-feed or add isolation | optional 0R debug / no / TBD / no | none / TBD / none / TBD / none / TBD | 100k pulldown |
| `PMIC_INT_L` | PMIC INT L | U7.PMIC_INT_L (L-Temple AON/Power Board) | U8.INT (L-Temple AON/Power Board) | see endpoints | 1.8V unless final pinmux says otherwise | TBD at pinmux freeze | none / TBD | same-domain only | optional 0R debug / no / TBD / no | nRF AON I2C/GPIO / nRF firmware config / nPM1300/BMI270/INA238/DRV2605L app drivers | derived from endpoints; verify at the owning gate |
| `PMIC_SHPHLD` | PMIC SHPHLD | U7.PMIC_SHPHLD (L-Temple AON/Power Board) | U8.SHPHLD (L-Temple AON/Power Board) | see endpoints | 1.8V unless final pinmux says otherwise | TBD at pinmux freeze | none / TBD | same-domain only | optional 0R debug / no / TBD / no | nRF AON I2C/GPIO / nRF firmware config / nPM1300/BMI270/INA238/DRV2605L app drivers | derived from endpoints; verify at the owning gate |
| `DSP_WAKE` | NDP120 wake interrupt to nRF | NDP120 | nRF | NDP120->nRF | 1.8V | low | none / TBD | same-domain only | optional 0R debug / no / TBD / no | nRF SPI/GPIO + NDP120 host interface / nRF firmware config / Syntiant SDK / nRF app | wake IRQ |
| `DSP_READY` | NDP120 ready indication | NDP120 | nRF | NDP120->nRF | 1.8V | low | none / TBD | same-domain only | optional 0R debug / no / TBD / no | nRF SPI/GPIO + NDP120 host interface / nRF firmware config / Syntiant SDK / nRF app | derived from endpoints; verify at the owning gate |
| `DSP_FAULT` | NDP120 fault indication | NDP120 | nRF | NDP120->nRF | 1.8V | low | none / TBD | same-domain only | optional 0R debug / no / TBD / no | nRF SPI/GPIO + NDP120 host interface / nRF firmware config / Syntiant SDK / nRF app | derived from endpoints; verify at the owning gate |
| `DSP_RESET_L` | NDP120 reset, active low | nRF | NDP120 | nRF->NDP120 | 1.8V | low (reset) | none / TBD | same-domain only | optional 0R debug / no / TBD / no | nRF SPI/GPIO + NDP120 host interface / nRF firmware config / Syntiant SDK / nRF app | active low |
| `HAPTIC_EN` | HAPTIC EN | U7.HAPTIC_EN (L-Temple AON/Power Board) | U22.EN (L-Temple AON/Power Board) | see endpoints | 1.8V unless final pinmux says otherwise | low (OFF) | none / TBD | same-domain only | optional 0R debug / no / TBD / no | nRF AON I2C/GPIO / nRF firmware config / nPM1300/BMI270/INA238/DRV2605L app drivers | derived from endpoints; verify at the owning gate |

## Bus nets (29)

| Net | Full name | From | To | Direction | Domain | Default | Pull | Off-high allowed | Series / ESD / Diff | Pinmux / DT / Driver | Notes |
|---|---|---|---|---|---|---|---|---|---|---|---|
| `AON_UART_TX` | AON UART TX | nRF | RK3576 | nRF->RK3576 | 1.8V | idle high | none / TBD | No; prove no reverse-feed or add isolation | 0R/22-33R recommended / no / TBD / no | nRF GPIO/UART + RK3576 GPIO/UART DT / power-state handshake + uart node / nRF app + Linux GPIO/UART | series 0R/33R + reverse-feed check when SoC off |
| `AON_UART_RX` | AON UART RX | RK3576 | nRF | RK3576->nRF | 1.8V | idle high | none / TBD | No; prove no reverse-feed or add isolation | 0R/22-33R recommended / no / TBD / no | nRF GPIO/UART + RK3576 GPIO/UART DT / power-state handshake + uart node / nRF app + Linux GPIO/UART | derived from endpoints; verify at the owning gate |
| `DDR_BUS` | DDR BUS | U1.DDR_BUS (R-Temple Compute Board) | U3.DDR_BUS (R-Temple Compute Board) | see endpoints | 1.8V unless final pinmux says otherwise | TBD at pinmux freeze | none / TBD | same-domain only | optional 0R debug / no / TBD / no | RK3576 fixed-function bus / bootloader + storage nodes / Rockchip BSP | derived from endpoints; verify at the owning gate |
| `EMMC_BUS` | EMMC BUS | U1.EMMC_BUS (R-Temple Compute Board) | U4.EMMC_BUS (R-Temple Compute Board) | see endpoints | 1.8V unless final pinmux says otherwise | TBD at pinmux freeze | none / TBD | same-domain only | optional 0R debug / no / TBD / no | RK3576 fixed-function bus / bootloader + storage nodes / Rockchip BSP | derived from endpoints; verify at the owning gate |
| `FSPI_BUS` | FSPI BUS | U1.FSPI_BUS (R-Temple Compute Board) | U5.FSPI_BUS (R-Temple Compute Board) | see endpoints | 1.8V unless final pinmux says otherwise | TBD at pinmux freeze | none / TBD | same-domain only | optional 0R debug / no / TBD / no | RK3576 fixed-function bus / bootloader + storage nodes / Rockchip BSP | derived from endpoints; verify at the owning gate |
| `CAM_I2C_SCL` | CAM I2C SCL | controller | targets | controller->targets | 1.8V unless final pinmux says otherwise | pulled high | 2.2k to CAM_1V8_SW (R5/R6) | No; prove no reverse-feed or add isolation | optional 0R debug / no / TBD / no | RK3576 camera pinmux; G10 module pinout / camera node + CSI/ISP graph / imx415 + rkisp | derived from endpoints; verify at the owning gate |
| `CAM_I2C_SDA` | CAM I2C SDA | U1.CAM_I2C_SDA (R-Temple Compute Board) | U14.SDA (Front Sensor Board); J3.11_I2C_SDA (Front Sensor Board); R6.B (Front Sensor Board) | bidirectional open-drain | 1.8V unless final pinmux says otherwise | pulled high | 2.2k to CAM_1V8_SW (R5/R6) | No; prove no reverse-feed or add isolation | optional 0R debug / no / TBD / no | RK3576 camera pinmux; G10 module pinout / camera node + CSI/ISP graph / imx415 + rkisp | derived from endpoints; verify at the owning gate |
| `PDM_ARRAY_CLK` | Array-mic PDM clock | RK3576 | mic | RK3576->mic | AON | off | none / TBD | No; prove no reverse-feed or add isolation | 0R/22-33R recommended / no / TBD / no | RK3576 audio pinmux / sound card / PDM / I2S nodes / ALSA SoC audio | array PDM; 0R to select NDP120/RK3576 path |
| `PDM_ARRAY_D0` | Array-mic PDM data 0 | array mics | RK3576 | array mics->RK3576 | 1.8V unless final pinmux says otherwise | TBD at pinmux freeze | none / TBD | No; prove no reverse-feed or add isolation | 0R/22-33R recommended / no / TBD / no | RK3576 audio pinmux / sound card / PDM / I2S nodes / ALSA SoC audio | derived from endpoints; verify at the owning gate |
| `PDM_ARRAY_D1` | Array-mic PDM data 1 | array mics | RK3576 | array mics->RK3576 | 1.8V unless final pinmux says otherwise | TBD at pinmux freeze | none / TBD | No; prove no reverse-feed or add isolation | 0R/22-33R recommended / no / TBD / no | RK3576 audio pinmux / sound card / PDM / I2S nodes / ALSA SoC audio | derived from endpoints; verify at the owning gate |
| `I2S_BCLK` | I2S BCLK | RK3576 | amp | RK3576->amp | 1.8V unless final pinmux says otherwise | TBD at pinmux freeze | none / TBD | same-domain only | optional 0R debug / no / TBD / no | RK3576 audio pinmux / sound card / PDM / I2S nodes / ALSA SoC audio | derived from endpoints; verify at the owning gate |
| `I2S_LRCLK` | I2S LRCLK | RK3576 | amp | RK3576->amp | 1.8V unless final pinmux says otherwise | TBD at pinmux freeze | none / TBD | same-domain only | optional 0R debug / no / TBD / no | RK3576 audio pinmux / sound card / PDM / I2S nodes / ALSA SoC audio | derived from endpoints; verify at the owning gate |
| `I2S_DIN` | I2S DIN | RK3576 | amp | RK3576->amp | 1.8V unless final pinmux says otherwise | TBD at pinmux freeze | none / TBD | same-domain only | optional 0R debug / no / TBD / no | RK3576 audio pinmux / sound card / PDM / I2S nodes / ALSA SoC audio | derived from endpoints; verify at the owning gate |
| `WIFI_PCM_CLK` | WIFI PCM CLK | U1.PCM_CLK (R-Temple Compute Board) | U11.PCM_CLK (R-Temple Compute Board) | see endpoints | 1.8V unless final pinmux says otherwise | TBD at pinmux freeze | none / TBD | same-domain only | optional 0R debug / no / TBD / no | RK3576 USB2/PCM + nRF GPIO for CHIP_EN / usb host + optional bt-audio PCM / usbcore + Quectel firmware | derived from endpoints; verify at the owning gate |
| `WIFI_PCM_SYNC` | WIFI PCM SYNC | U1.PCM_SYNC (R-Temple Compute Board) | U11.PCM_SYNC (R-Temple Compute Board) | see endpoints | 1.8V unless final pinmux says otherwise | TBD at pinmux freeze | none / TBD | same-domain only | optional 0R debug / no / TBD / no | RK3576 USB2/PCM + nRF GPIO for CHIP_EN / usb host + optional bt-audio PCM / usbcore + Quectel firmware | derived from endpoints; verify at the owning gate |
| `WIFI_PCM_DIN` | WIFI PCM DIN | U1.PCM_DIN (R-Temple Compute Board) | U11.PCM_OUT (R-Temple Compute Board) | see endpoints | 1.8V unless final pinmux says otherwise | TBD at pinmux freeze | none / TBD | same-domain only | optional 0R debug / no / TBD / no | RK3576 USB2/PCM + nRF GPIO for CHIP_EN / usb host + optional bt-audio PCM / usbcore + Quectel firmware | derived from endpoints; verify at the owning gate |
| `WIFI_PCM_DOUT` | WIFI PCM DOUT | U1.PCM_DOUT (R-Temple Compute Board) | U11.PCM_IN (R-Temple Compute Board) | see endpoints | 1.8V unless final pinmux says otherwise | TBD at pinmux freeze | none / TBD | same-domain only | optional 0R debug / no / TBD / no | RK3576 USB2/PCM + nRF GPIO for CHIP_EN / usb host + optional bt-audio PCM / usbcore + Quectel firmware | derived from endpoints; verify at the owning gate |
| `I2C_AON_SCL` | I2C AON SCL | controller | targets | controller->targets | 1.8V | pull-up 2.2k | 2.2k to AON_1V8 (R3/R4) | No; prove no reverse-feed or add isolation | optional 0R debug / no / TBD / no | nRF AON I2C/GPIO / nRF firmware config / nPM1300/BMI270/INA238/DRV2605L app drivers | nPM1300/BMI270/INA238 |
| `I2C_AON_SDA` | I2C AON SDA | U35.SDA (R-Temple Compute Board) | U7.I2C_SDA (L-Temple AON/Power Board); U8.I2C_SDA (L-Temple AON/Power Board); U10.SDA (L-Temple AON/Power Board); U22.SDA (L-Temple AON/Power Board); U25.SDA (L-Temple AON/Power Board); U26.SDA (Temple Rears (batt/spkr/ant)); U27.SDA (Temple Rears (batt/spkr/ant)); U28.SDA (R-Temple Compute Board); U29.SDA (R-Temple Compute Board); U30.SDA (R-Temple Compute Board); U31.SDA (Front Sensor Board); U32.SDA (Front Sensor Board); U33.SDA (Front Sensor Board); R4.B (L-Temple AON/Power Board) | bidirectional open-drain | 1.8V | pull-up 2.2k | 2.2k to AON_1V8 (R3/R4) | No; prove no reverse-feed or add isolation | optional 0R debug / no / TBD / no | nRF AON I2C/GPIO / nRF firmware config / nPM1300/BMI270/INA238/DRV2605L app drivers | derived from endpoints; verify at the owning gate |
| `DSP_SPI_SCK` | DSP SPI SCK | owner | peer | owner->peer | 1.8V unless final pinmux says otherwise | TBD at pinmux freeze | none / TBD | same-domain only | optional 0R debug / no / TBD / no | nRF SPI/GPIO + NDP120 host interface / nRF firmware config / Syntiant SDK / nRF app | derived from endpoints; verify at the owning gate |
| `DSP_SPI_MOSI` | DSP SPI MOSI | owner | peer | owner->peer | 1.8V unless final pinmux says otherwise | TBD at pinmux freeze | none / TBD | same-domain only | optional 0R debug / no / TBD / no | nRF SPI/GPIO + NDP120 host interface / nRF firmware config / Syntiant SDK / nRF app | derived from endpoints; verify at the owning gate |
| `DSP_SPI_MISO` | DSP SPI MISO | peer | owner | peer->owner | 1.8V unless final pinmux says otherwise | TBD at pinmux freeze | none / TBD | same-domain only | optional 0R debug / no / TBD / no | nRF SPI/GPIO + NDP120 host interface / nRF firmware config / Syntiant SDK / nRF app | derived from endpoints; verify at the owning gate |
| `DSP_SPI_CS_n` | DSP SPI CS n | owner | peer | owner->peer | 1.8V unless final pinmux says otherwise | TBD at pinmux freeze | none / TBD | same-domain only | optional 0R debug / no / TBD / no | nRF SPI/GPIO + NDP120 host interface / nRF firmware config / Syntiant SDK / nRF app | derived from endpoints; verify at the owning gate |
| `NRF_SWDIO` | NRF SWDIO | U7.SWDIO (L-Temple AON/Power Board) | TP1.SWDIO (EVT Debug Tail) | see endpoints | 1.8V unless final pinmux says otherwise | TBD at pinmux freeze | none / TBD | No; prove no reverse-feed or add isolation | optional 0R debug / no / TBD / no | debug only / none / SWD probe | derived from endpoints; verify at the owning gate |
| `NRF_SWDCLK` | NRF SWDCLK | U7.SWDCLK (L-Temple AON/Power Board) | TP1.SWDCLK (EVT Debug Tail) | see endpoints | 1.8V unless final pinmux says otherwise | TBD at pinmux freeze | none / TBD | No; prove no reverse-feed or add isolation | optional 0R debug / no / TBD / no | debug only / none / SWD probe | derived from endpoints; verify at the owning gate |
| `PDM_WAKE_CLK` | Dedicated wake-mic PDM clock | NDP120 | mic | NDP120->mic | AON | off | none / TBD | No; prove no reverse-feed or add isolation | 0R/22-33R recommended / no / TBD / no | nRF SPI/GPIO + NDP120 host interface / nRF firmware config / Syntiant SDK / nRF app | wake mic PDM; 0R/22R debug pos; single master |
| `PDM_WAKE_DATA` | Dedicated wake-mic PDM data | wake mic | NDP120 | wake mic->NDP120 | 1.8V unless final pinmux says otherwise | TBD at pinmux freeze | none / TBD | No; prove no reverse-feed or add isolation | 0R/22-33R recommended / no / TBD / no | nRF SPI/GPIO + NDP120 host interface / nRF firmware config / Syntiant SDK / nRF app | derived from endpoints; verify at the owning gate |
| `USB_CC1` | USB CC1 | J2.CC1 (EVT Debug Tail) | R1.A (EVT Debug Tail) | bidirectional | 1.8V unless final pinmux says otherwise | TBD at pinmux freeze | 5.1k Rd to GND | same-domain only | optional 0R debug / no / TBD / no | RK3576 USB2 OTG/host / usb2 port / connector / dwc2/xhci + Type-C sink policy | derived from endpoints; verify at the owning gate |
| `USB_CC2` | USB CC2 | J2.CC2 (EVT Debug Tail) | R2.A (EVT Debug Tail) | bidirectional | 1.8V unless final pinmux says otherwise | TBD at pinmux freeze | 5.1k Rd to GND | same-domain only | optional 0R debug / no / TBD / no | RK3576 USB2 OTG/host / usb2 port / connector / dwc2/xhci + Type-C sink policy | derived from endpoints; verify at the owning gate |

## Diff nets (18)

| Net | Full name | From | To | Direction | Domain | Default | Pull | Off-high allowed | Series / ESD / Diff | Pinmux / DT / Driver | Notes |
|---|---|---|---|---|---|---|---|---|---|---|---|
| `CSI_CLK_P` | CSI CLK P | camera | RK3576 | camera->RK3576 | 1.2V | hi-Z | none / TBD | No; prove no reverse-feed or add isolation | none / yes, low-cap at FPC entry (U18/U19) / CSI_CLK_N | RK3576 camera pinmux; G10 module pinout / camera node + CSI/ISP graph / imx415 + rkisp | MIPI 100R diff, ultra-low-cap ESD, no stub |
| `CSI_CLK_N` | CSI CLK N | camera | RK3576 | camera->RK3576 | 1.2V | hi-Z | none / TBD | No; prove no reverse-feed or add isolation | none / yes, low-cap at FPC entry (U18/U19) / CSI_CLK_P | RK3576 camera pinmux; G10 module pinout / camera node + CSI/ISP graph / imx415 + rkisp | MIPI 100R diff |
| `CSI_D0_P` | CSI D0 P | camera | RK3576 | camera->RK3576 | 1.2V | hi-Z | none / TBD | No; prove no reverse-feed or add isolation | none / yes, low-cap at FPC entry (U18/U19) / CSI_D0_N | RK3576 camera pinmux; G10 module pinout / camera node + CSI/ISP graph / imx415 + rkisp | MIPI 100R diff |
| `CSI_D0_N` | CSI D0 N | camera | RK3576 | camera->RK3576 | MIPI D-PHY | hi-Z when source domain is off | none / TBD | No; prove no reverse-feed or add isolation | none / yes, low-cap at FPC entry (U18/U19) / CSI_D0_P | RK3576 camera pinmux; G10 module pinout / camera node + CSI/ISP graph / imx415 + rkisp | derived from endpoints; verify at the owning gate |
| `CSI_D1_P` | CSI D1 P | camera | RK3576 | camera->RK3576 | 1.2V | hi-Z | none / TBD | No; prove no reverse-feed or add isolation | none / yes, low-cap at FPC entry (U18/U19) / CSI_D1_N | RK3576 camera pinmux; G10 module pinout / camera node + CSI/ISP graph / imx415 + rkisp | MIPI 100R diff |
| `CSI_D1_N` | CSI D1 N | camera | RK3576 | camera->RK3576 | MIPI D-PHY | hi-Z when source domain is off | none / TBD | No; prove no reverse-feed or add isolation | none / yes, low-cap at FPC entry (U18/U19) / CSI_D1_P | RK3576 camera pinmux; G10 module pinout / camera node + CSI/ISP graph / imx415 + rkisp | derived from endpoints; verify at the owning gate |
| `CSI_D2_P` | CSI D2 P | camera | RK3576 | camera->RK3576 | MIPI D-PHY | hi-Z when source domain is off | none / TBD | No; prove no reverse-feed or add isolation | none / yes, low-cap at FPC entry (U18/U19) / CSI_D2_N | RK3576 camera pinmux; G10 module pinout / camera node + CSI/ISP graph / imx415 + rkisp | derived from endpoints; verify at the owning gate |
| `CSI_D2_N` | CSI D2 N | camera | RK3576 | camera->RK3576 | MIPI D-PHY | hi-Z when source domain is off | none / TBD | No; prove no reverse-feed or add isolation | none / yes, low-cap at FPC entry (U18/U19) / CSI_D2_P | RK3576 camera pinmux; G10 module pinout / camera node + CSI/ISP graph / imx415 + rkisp | derived from endpoints; verify at the owning gate |
| `CSI_D3_P` | CSI D3 P | camera | RK3576 | camera->RK3576 | MIPI D-PHY | hi-Z when source domain is off | none / TBD | No; prove no reverse-feed or add isolation | none / yes, low-cap at FPC entry (U18/U19) / CSI_D3_N | RK3576 camera pinmux; G10 module pinout / camera node + CSI/ISP graph / imx415 + rkisp | derived from endpoints; verify at the owning gate |
| `CSI_D3_N` | CSI D3 N | camera | RK3576 | camera->RK3576 | MIPI D-PHY | hi-Z when source domain is off | none / TBD | No; prove no reverse-feed or add isolation | none / yes, low-cap at FPC entry (U18/U19) / CSI_D3_P | RK3576 camera pinmux; G10 module pinout / camera node + CSI/ISP graph / imx415 + rkisp | derived from endpoints; verify at the owning gate |
| `WIFI_USB_DP` | WIFI USB DP | U1.USB2_WIFI_DP (R-Temple Compute Board) | U11.USB_DP (R-Temple Compute Board) | bidirectional | 3.3V | hi-Z | none / TBD | same-domain only | none / module-internal side; add only if HW Design requires / WIFI_USB_DM | RK3576 USB2/PCM + nRF GPIO for CHIP_EN / usb host + optional bt-audio PCM / usbcore + Quectel firmware | FCU760K USB2 90R diff (internal) |
| `WIFI_USB_DM` | WIFI USB DM | U1.USB2_WIFI_DM (R-Temple Compute Board) | U11.USB_DM (R-Temple Compute Board) | bidirectional | 3.3V | hi-Z | none / TBD | same-domain only | none / module-internal side; add only if HW Design requires / WIFI_USB_DP | RK3576 USB2/PCM + nRF GPIO for CHIP_EN / usb host + optional bt-audio PCM / usbcore + Quectel firmware | FCU760K USB2 90R diff (internal) |
| `USB2_DP` | USB2 DP | U1.USB2_DP (R-Temple Compute Board) | J1.USB_DP (Temple Rears (batt/spkr/ant)); J2.DP (EVT Debug Tail); U24.DP (EVT Debug Tail) | bidirectional | 3.3V | hi-Z | none / TBD | No; prove no reverse-feed or add isolation | none / yes, low-cap at connector (U24) / USB2_DM | RK3576 USB2 OTG/host / usb2 port / connector / dwc2/xhci + Type-C sink policy | USB2 90R diff, ESD at connector |
| `USB2_DM` | USB2 DM | U1.USB2_DM (R-Temple Compute Board) | J1.USB_DN (Temple Rears (batt/spkr/ant)); J2.DM (EVT Debug Tail); U24.DM (EVT Debug Tail) | bidirectional | 3.3V | hi-Z | none / TBD | No; prove no reverse-feed or add isolation | none / yes, low-cap at connector (U24) / USB2_DP | RK3576 USB2 OTG/host / usb2 port / connector / dwc2/xhci + Type-C sink policy | USB2 90R diff |
| `SPK_P` | SPK P | U20.OUT_P (R-Temple Compute Board) | LS1.P (Temple Rears (batt/spkr/ant)) | see endpoints | TBD | hi-Z when source domain is off | none / TBD | No; prove no reverse-feed or add isolation | none / no / TBD / SPK_N | none / TBD / none / TBD / none / TBD | derived from endpoints; verify at the owning gate |
| `SPK_N` | SPK N | U20.OUT_N (R-Temple Compute Board) | LS1.N (Temple Rears (batt/spkr/ant)) | see endpoints | TBD | hi-Z when source domain is off | none / TBD | No; prove no reverse-feed or add isolation | none / no / TBD / SPK_P | none / TBD / none / TBD / none / TBD | derived from endpoints; verify at the owning gate |
| `HAPTIC_P` | HAPTIC P | U22.OUT_P (L-Temple AON/Power Board) | M1.P (Temple Rears (batt/spkr/ant)) | see endpoints | TBD | hi-Z when source domain is off | none / TBD | No; prove no reverse-feed or add isolation | none / no / TBD / HAPTIC_N | nRF AON I2C/GPIO / nRF firmware config / nPM1300/BMI270/INA238/DRV2605L app drivers | derived from endpoints; verify at the owning gate |
| `HAPTIC_N` | HAPTIC N | U22.OUT_N (L-Temple AON/Power Board) | M1.N (Temple Rears (batt/spkr/ant)) | see endpoints | TBD | hi-Z when source domain is off | none / TBD | No; prove no reverse-feed or add isolation | none / no / TBD / HAPTIC_P | nRF AON I2C/GPIO / nRF firmware config / nPM1300/BMI270/INA238/DRV2605L app drivers | derived from endpoints; verify at the owning gate |

## Analog nets (5)

| Net | Full name | From | To | Direction | Domain | Default | Pull | Off-high allowed | Series / ESD / Diff | Pinmux / DT / Driver | Notes |
|---|---|---|---|---|---|---|---|---|---|---|---|
| `SOC_NTC` | SOC NTC | U1.SARADC_NTC (R-Temple Compute Board) | RT3.A (R-Temple Compute Board) | see endpoints | TBD | passive / sensed | none / TBD | same-domain only | none / no / TBD / no | nRF GPIO/UART + RK3576 GPIO/UART DT / power-state handshake + uart node / nRF app + Linux GPIO/UART | derived from endpoints; verify at the owning gate |
| `WIFI_ANT` | Wi-Fi/BT shared RF antenna feed | U11.ANT_WIFI_BT (R-Temple Compute Board) | J7.ANT (Temple Rears (batt/spkr/ant)); J5.SIG (Temple Rears (batt/spkr/ant)) | see endpoints | RF | - | none / TBD | No; prove no reverse-feed or add isolation | none / RF-approved only if required / no | none / TBD / none / TBD / none / TBD | 50R; pi-match; shared Wi-Fi/BLE FPC antenna; keep out from battery/magnet/shield/copper |
| `BLE_ANT` | Optional FCU760K ANT_BT DNP RF test feed | U11.ANT_BT_DNP (R-Temple Compute Board) | J6.ANT (Temple Rears (batt/spkr/ant)) | see endpoints | RF | - | none / TBD | No; prove no reverse-feed or add isolation | none / RF-approved only if required / no | none / TBD / none / TBD / none / TBD | DNP optional FCU760K ANT_BT test/matching node; no separate BLE antenna fitted in EVT V2.0 |
| `NTC_R` | NTC R | U35.TS (R-Temple Compute Board) | U8.NTC_R (L-Temple AON/Power Board); PCM1.NTC1 (Temple Rears (batt/spkr/ant)); RT1.A (Temple Rears (batt/spkr/ant)); TP2.NTC_R (Temple Rears (batt/spkr/ant)) | see endpoints | analog | - | none / TBD | No; prove no reverse-feed or add isolation | none / no / TBD / no | none / TBD / none / TBD / none / TBD | per-cell NTC (§15) |
| `NTC_L` | NTC L | U8.NTC_L (L-Temple AON/Power Board) | PCM1.NTC2_OR_ID (Temple Rears (batt/spkr/ant)); RT2.A (Temple Rears (batt/spkr/ant)); TP2.NTC_L (Temple Rears (batt/spkr/ant)) | see endpoints | analog | - | none / TBD | No; prove no reverse-feed or add isolation | none / no / TBD / no | none / TBD / none / TBD / none / TBD | per-cell NTC (§15) |

## Signal nets (14)

| Net | Full name | From | To | Direction | Domain | Default | Pull | Off-high allowed | Series / ESD / Diff | Pinmux / DT / Driver | Notes |
|---|---|---|---|---|---|---|---|---|---|---|---|
| `SOC_XIN` | SOC XIN | U1.XIN (R-Temple Compute Board) | Y1.XIN (R-Temple Compute Board) | see endpoints | TBD | TBD at pinmux freeze | none / TBD | same-domain only | none / no / TBD / no | nRF GPIO/UART + RK3576 GPIO/UART DT / power-state handshake + uart node / nRF app + Linux GPIO/UART | derived from endpoints; verify at the owning gate |
| `SOC_XOUT` | SOC XOUT | U1.XOUT (R-Temple Compute Board) | Y1.XOUT (R-Temple Compute Board) | see endpoints | TBD | TBD at pinmux freeze | none / TBD | same-domain only | none / no / TBD / no | nRF GPIO/UART + RK3576 GPIO/UART DT / power-state handshake + uart node / nRF app + Linux GPIO/UART | derived from endpoints; verify at the owning gate |
| `SOC_DBG_TX` | SOC DBG TX | U1.DBG_UART_TX (R-Temple Compute Board) | TP1.SOC_TX (EVT Debug Tail) | see endpoints | TBD | TBD at pinmux freeze | none / TBD | same-domain only | none / no / TBD / no | nRF GPIO/UART + RK3576 GPIO/UART DT / power-state handshake + uart node / nRF app + Linux GPIO/UART | derived from endpoints; verify at the owning gate |
| `SOC_DBG_RX` | SOC DBG RX | U1.DBG_UART_RX (R-Temple Compute Board) | TP1.SOC_RX (EVT Debug Tail) | see endpoints | TBD | TBD at pinmux freeze | none / TBD | same-domain only | none / no / TBD / no | nRF GPIO/UART + RK3576 GPIO/UART DT / power-state handshake + uart node / nRF app + Linux GPIO/UART | derived from endpoints; verify at the owning gate |
| `SOC_PMIC_SCL` | SOC PMIC SCL | controller | targets | controller->targets | TBD | TBD at pinmux freeze | 2.2k to VCCIO_1V8 (R9/R10) | same-domain only | none / no / TBD / no | nRF GPIO/UART + RK3576 GPIO/UART DT / power-state handshake + uart node / nRF app + Linux GPIO/UART | derived from endpoints; verify at the owning gate |
| `SOC_PMIC_SDA` | SOC PMIC SDA | U2.I2C_SDA (R-Temple Compute Board) | R10.B (R-Temple Compute Board) | bidirectional open-drain | TBD | TBD at pinmux freeze | 2.2k to VCCIO_1V8 (R9/R10) | same-domain only | none / no / TBD / no | nRF GPIO/UART + RK3576 GPIO/UART DT / power-state handshake + uart node / nRF app + Linux GPIO/UART | derived from endpoints; verify at the owning gate |
| `SOC_BOOST_SW` | SOC BOOST SW | U6.SW (R-Temple Compute Board) | L1.B (R-Temple Compute Board) | see endpoints | TBD | TBD at pinmux freeze | none / TBD | same-domain only | none / no / TBD / no | nRF GPIO/UART + RK3576 GPIO/UART DT / power-state handshake + uart node / nRF app + Linux GPIO/UART | derived from endpoints; verify at the owning gate |
| `WIFI_BUCK_SW` | WIFI BUCK SW | U12.SW (R-Temple Compute Board) | L2.A (R-Temple Compute Board) | see endpoints | TBD | TBD at pinmux freeze | none / TBD | same-domain only | none / no / TBD / no | none / TBD / none / TBD / none / TBD | derived from endpoints; verify at the owning gate |
| `CHG_CE_L` | CHG CE L | U35.CE_L (R-Temple Compute Board) | U7.CHG_CE_L (L-Temple AON/Power Board) | see endpoints | TBD | TBD at pinmux freeze | none / TBD | same-domain only | none / no / TBD / no | none / TBD / none / TBD / none / TBD | derived from endpoints; verify at the owning gate |
| `CHG_PG_L` | CHG PG L | U35.PG_L (R-Temple Compute Board) | U7.CHG_PG_L (L-Temple AON/Power Board) | see endpoints | TBD | TBD at pinmux freeze | none / TBD | same-domain only | none / no / TBD / no | none / TBD / none / TBD / none / TBD | derived from endpoints; verify at the owning gate |
| `IMU_INT1` | IMU INT1 | U7.IMU_INT1 (L-Temple AON/Power Board) | U10.INT1 (L-Temple AON/Power Board) | see endpoints | TBD | TBD at pinmux freeze | none / TBD | same-domain only | none / no / TBD / no | nRF AON I2C/GPIO / nRF firmware config / nPM1300/BMI270/INA238/DRV2605L app drivers | derived from endpoints; verify at the owning gate |
| `IMU_INT2` | IMU INT2 | U7.IMU_INT2 (L-Temple AON/Power Board) | U10.INT2 (L-Temple AON/Power Board) | see endpoints | TBD | TBD at pinmux freeze | none / TBD | same-domain only | none / no / TBD / no | nRF AON I2C/GPIO / nRF firmware config / nPM1300/BMI270/INA238/DRV2605L app drivers | derived from endpoints; verify at the owning gate |
| `CAM_MODULE_ID` | CAM MODULE ID | U14.MODULE_ID (Front Sensor Board) | J3.31_MODULE_ID (Front Sensor Board) | see endpoints | TBD | TBD at pinmux freeze | none / TBD | same-domain only | none / no / TBD / no | none / TBD / none / TBD / none / TBD | derived from endpoints; verify at the owning gate |
| `CAM_1V1_SW` | CAM 1V1 SW | U15.SW (Front Sensor Board) | L3.A (Front Sensor Board) | see endpoints | 1.1V | TBD at pinmux freeze | none / TBD | same-domain only | none / no / TBD / no | none / TBD / none / TBD / none / TBD | derived from endpoints; verify at the owning gate |
