lhongyi-ai/AI_Goggles/reports/output/Design Review.pdf

AI Glasses Carrier V1 - PCB Design Review

2026-06-30

# AI Glasses Carrier V1 - PCB Design Review

# AI Glasses Carrier V1 - PCB Design Review

Date | 2026-06-30

2026-06-30

# Table of Contents

### 1. Project status 2. Schematic status (ERC) 3. PCB status (DRC) 4. Footprint status

4.1 The 1 remaining placeholders - proposed real footprints

### 5. Component list (by function)

CM4 Module / B2B Connectors (3)
Camera (P0) (11)
Audio (P0) (9)
USB-C (P0) (8)
Power (P0) (10)
Battery (P1) (14)
IMU / Haptic (P1) (7)
GNSS / Positioning (P0) (11) Indicators / Debug (5)
Test Points (16)
Buttons (8)

### 6. CM4 pin assignment (verified vs official pinout) 7. Passive component spec audit

7.1 Resistors - value, tolerance, package, tempco, power 7.2 Capacitors - value, voltage, dielectric, package, temp 7.3 Magnetics, protection, indicators

### 8. What's missing - open TBDs (freeze gate, §8.3) 9. Key recommendations Appendix A - full pin -> net connections

2026-06-30 | Page 3
- Board: ai_glasses_carrier_v1 | CM4 SKU: RM126-D4E32J0R35W28 (RK3576, 4GB LPDDR4X, 32GB
eMMC, Wi-Fi6+BT5.x)
- Pin-assignment status: REVIEW (verified vs official pinout; not yet FROZEN)
- Generated: 2026-06-30 (from working sources; see footer)
- Components: 102 (81 P0) | Passive families: 22 (LOCKED 11 / VERIFY 6 / TUNE 5)
- ERC: 0 | DRC: 0 violations | Footprints: 101/102 real (1 VERIFY), 0 placed | MPN set: 27/102

[!] Stage: schematic / pin-freeze. The PCB is intentionally an empty skeleton (outline + 6-layer stack + mounting holes + nets, no footprints placed). Per repo rule 7 this report makes no claim about layout/copper/clearance correctness - that is confirmed only in KiCad/3D after placement. Part values & specs are EVT candidates pending human review.

# 1. Project status

Item | State
Pin assignment | [OK] 56 rows, all verified vs `radxa_cm4_pinout_v1.20.xlsx`
Freeze gate | [BLOCKED] `REVIEW` - blocked by 3 procurement/mechanical TBDs (not pins)
Schematic | [OK] element-level draft, net-connectivity verified
PCB layout | [ ] not started (skeleton only)
ERC / DRC | 0 / 0 violations (see §2/§3)

# 2. Schematic status (ERC)

Schematic is generated from the BOM master (scripts/carrier_bom.py) as box symbols with global net labels; every net was checked with kicad-cli sch export netlist. The CM4 module is drawn as its three B2B connectors (J31=J3A, J32=J3B, J1) carrying the real CM4 pins.

ERC: 0 errors, 0 warnings - clean (ai_context/erc.report.txt: "ERC messages: 0 Errors 0 Warnings 0"). Confirms 102 symbols + 321 net labels with no unconnected-critical-pin, duplicate-net, or power-driver violations.

# 3. PCB status (DRC)

PCB = pre-layout skeleton: 70×55 mm outline (placeholder - carrier outline still a TBD), 6-layer stack (F.Cu / In1.GND / In2.PWR / In3.sig / In4.GND / B.Cu), 4× M2 mounting holes, declared nets, no component footprints. Update PCB from Schematic will populate it once footprints are assigned and the gate is FROZEN.

DRC: 0 errors, 0 warnings on the skeleton (ai_context/drc.report.txt). Meaningful DRC (clearances, diff-pair, copper) only applies after footprints are placed.

# 4. Footprint status

"Footprint" means three different things at three stages - they are NOT the same, and conflating them is what makes the status look contradictory:

Layer | Meaning | Status
(1) Footprint field (pointer) | Each symbol names *which* footprint to
use

**102/102** assigned

(2) Real footprint exists/usable | That name maps to a real KiCad library
footprint

**101/102** real, **1** still `VERIFY` placeholder

(3) Placed on the PCB | Physical footprint dropped into
`.kicad_pcb`

**0** (pre-layout skeleton)

So: every symbol has a footprint pointer (needed for Update PCB from Schematic), 101 of those now point at real, datasheet-checked footprints from the installed KiCad 10 libraries (all passives + most connectors/ICs/test points), 1 are still placeholders, and nothing is placed on the board yet.

## 4.1 The 1 remaining placeholders - proposed real footprints

Each was researched against the installed KiCad libraries / the part datasheet. custom = must be drawn in AI_Glasses.pretty (no stock footprint); confirm = std-lib family identified, verify exact pads/EP vs the ordered part.

Ref | Part / package | Proposed footprint | Action
L1 | Boost inductor 4.7uH, >=10A sat | `Inductor_SMD: 4x4mm class per chosen part` | confirm

All parts now use authoritative KiCad-library footprints, including the TI-official land patterns for the
small packages: B2B = Connector_Hirose_DF40:Hirose_DF40C-100DS-0.4V_2x50_P0.4mm, GNSS = RF_GPS:ublox_MAX, IMU = Package_LGA:LGA-14_3x2.5mm, TPD4E05U06 = Package_SON:USON-10_2.5x1.0mm_P0.5mm, TPS61022 = Package_DFN_QFN:Texas_RWU0007A_VQFN-7_2x2mm. A 1:1
print-and-verify fixture for the two small packages is in hardware/confirm_fp_1to1_check.kicad_pcb (PDF: reports/output/Confirm_FP_1to1_Check.pdf). The only remaining placeholder is L1 (boost inductor) - its footprint is selected once the boost peak current sets the inductor part. The B2B footprint geometry is authoritative, but the locked 3-connector PLACEMENT still needs the mechanical fit-check (official CM4 STEP + 2-layer coupon, see §8).

# 5. Component list (by function)

## CM4 Module / B2B Connectors (3)

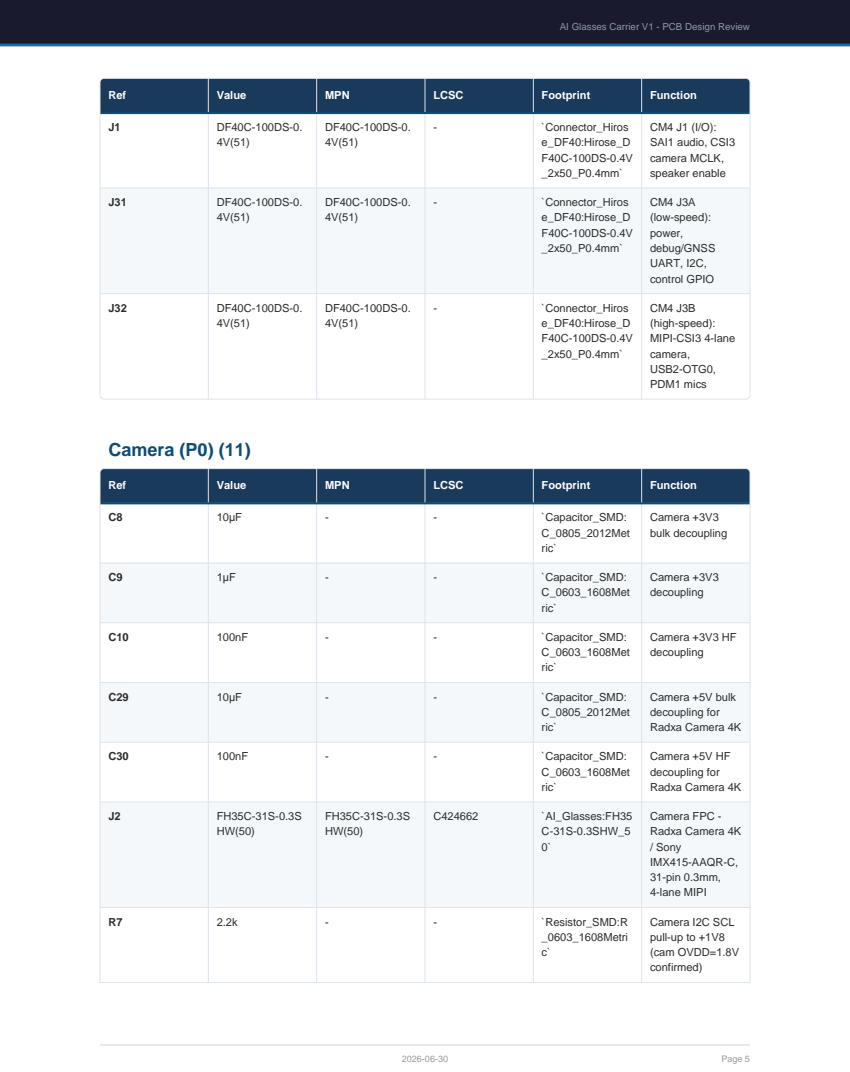
[picture p14: page 5]

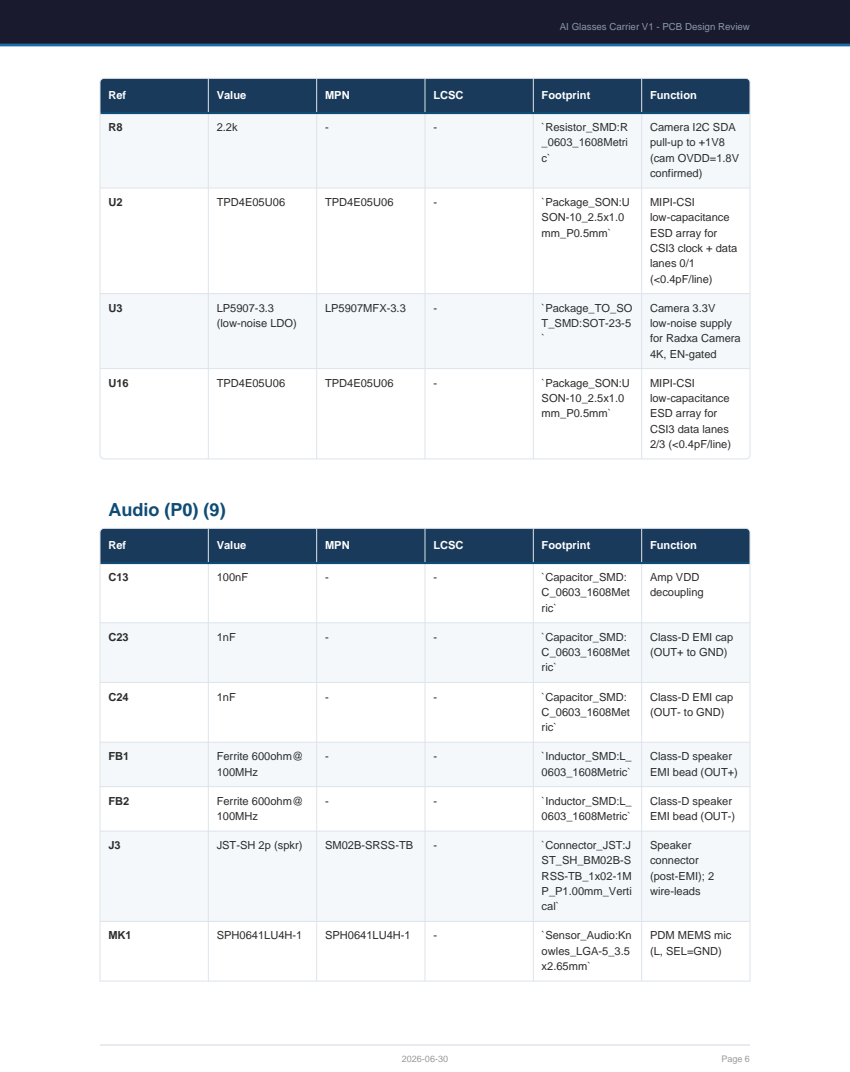
[picture p15: page 6]

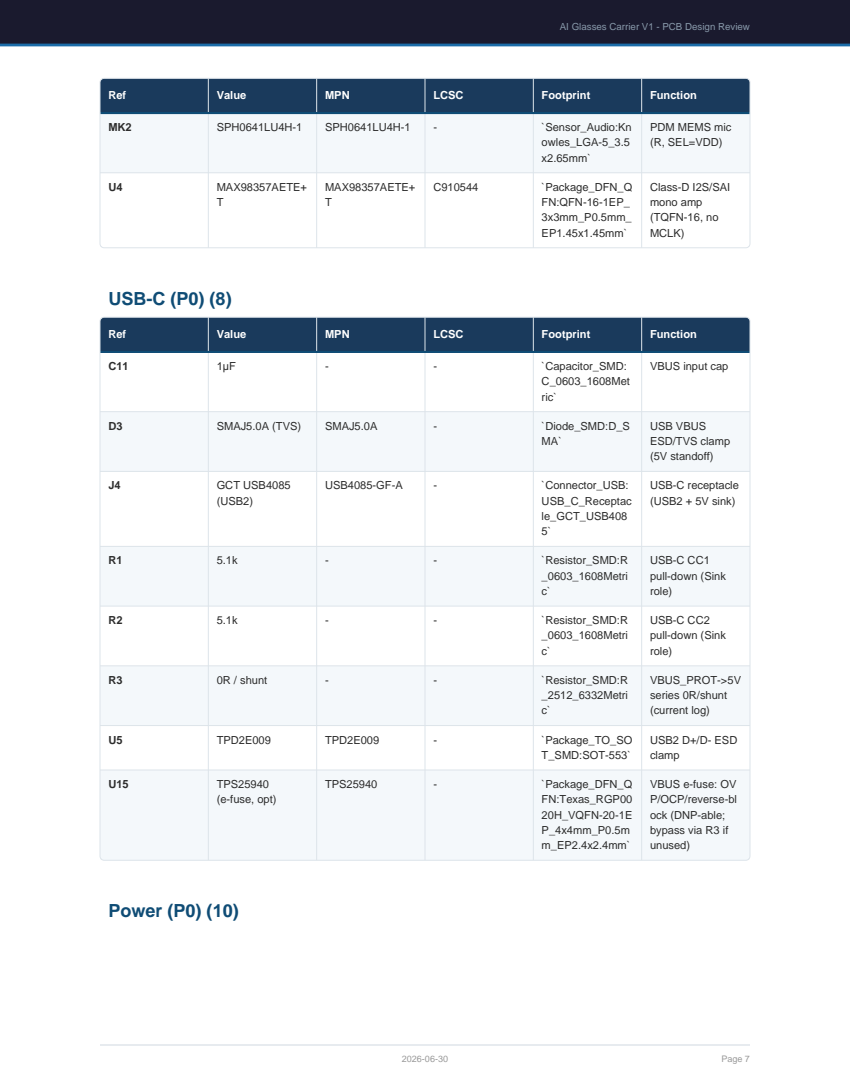
[picture p16: page 7]

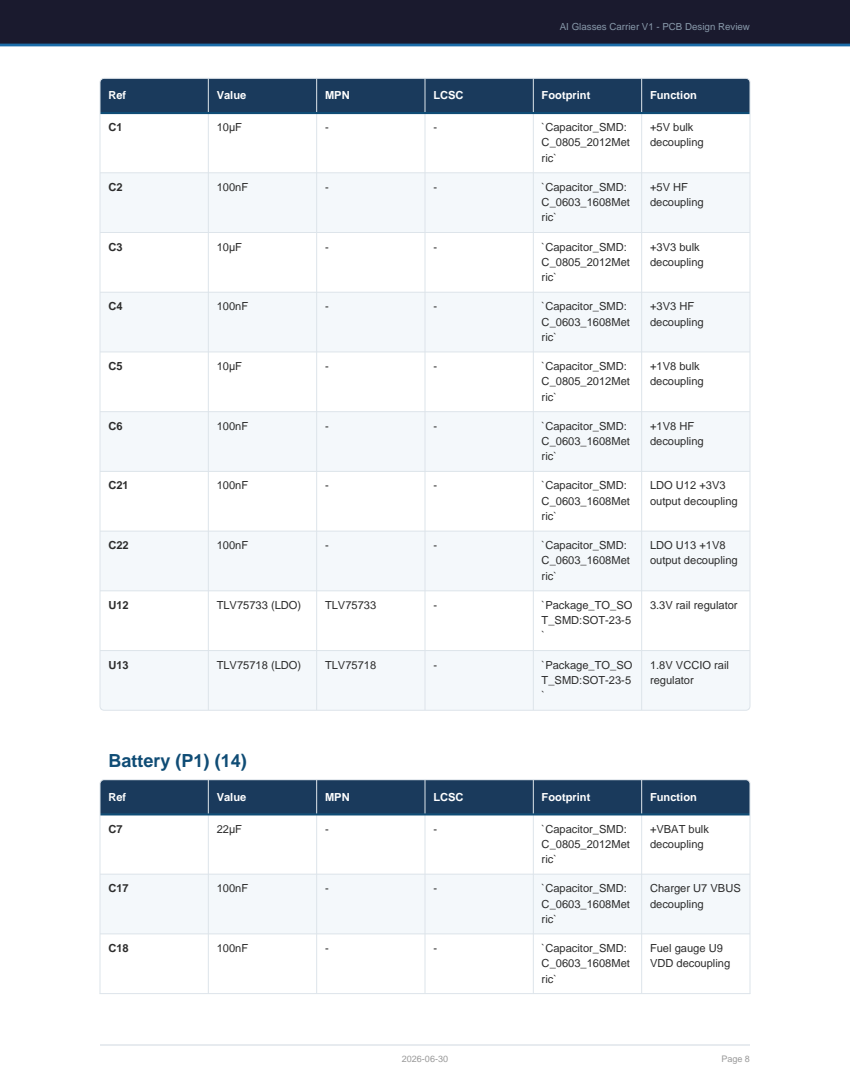
[picture p17: page 8]

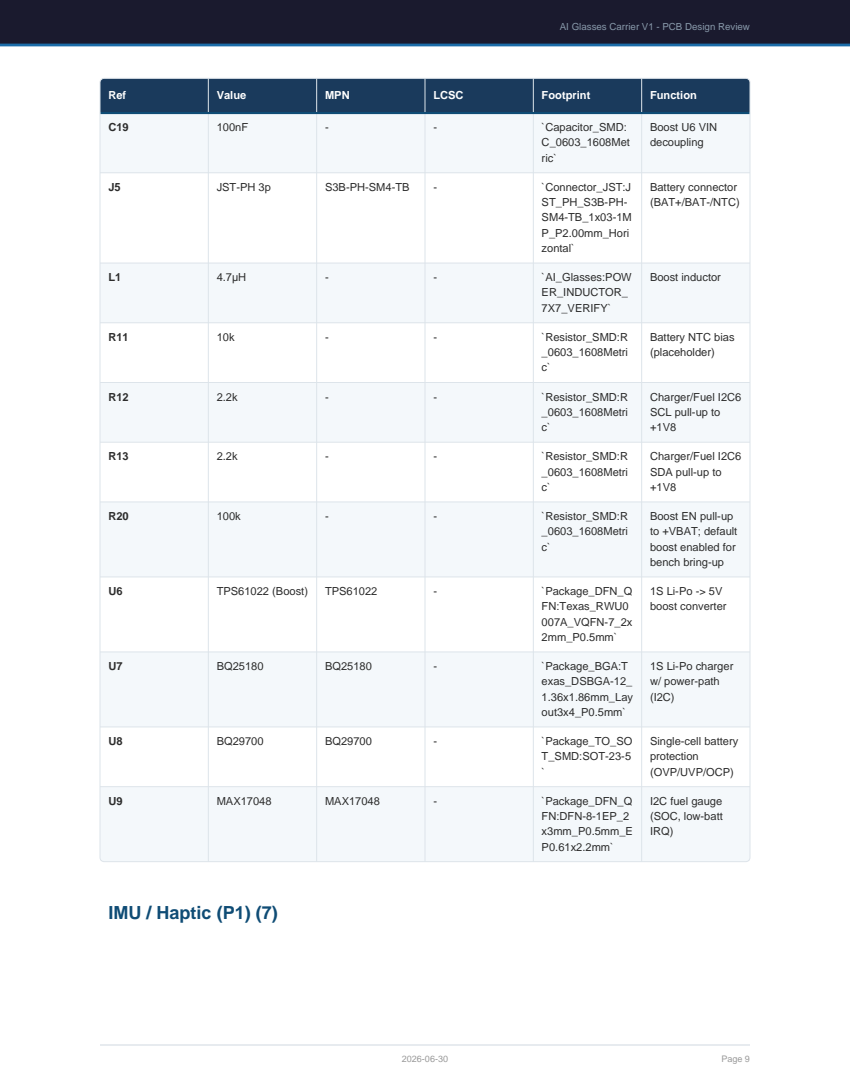
[picture p18: page 9]

Charger/Fuel I2C6
SCL pull-up to

SDA pull-up to

Boost EN pull-up
to +VBAT; default
boost enabled for
bench bring-up

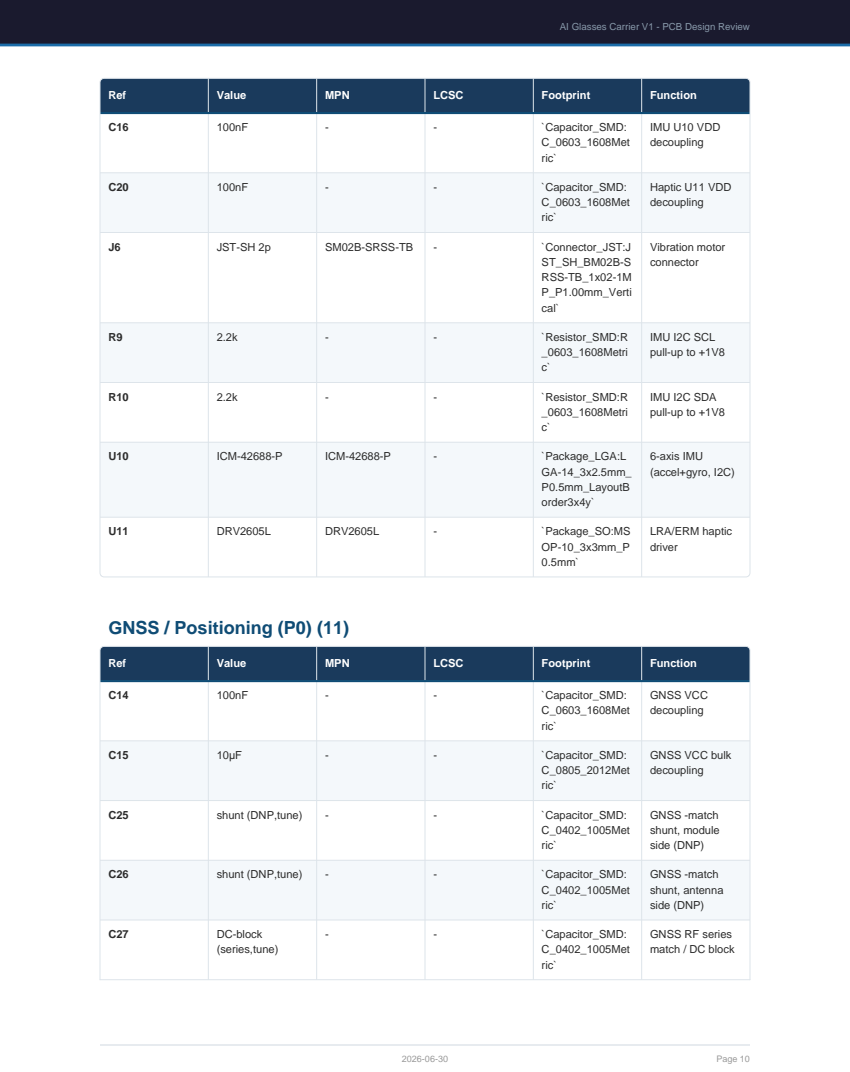
[picture p19: page 10]

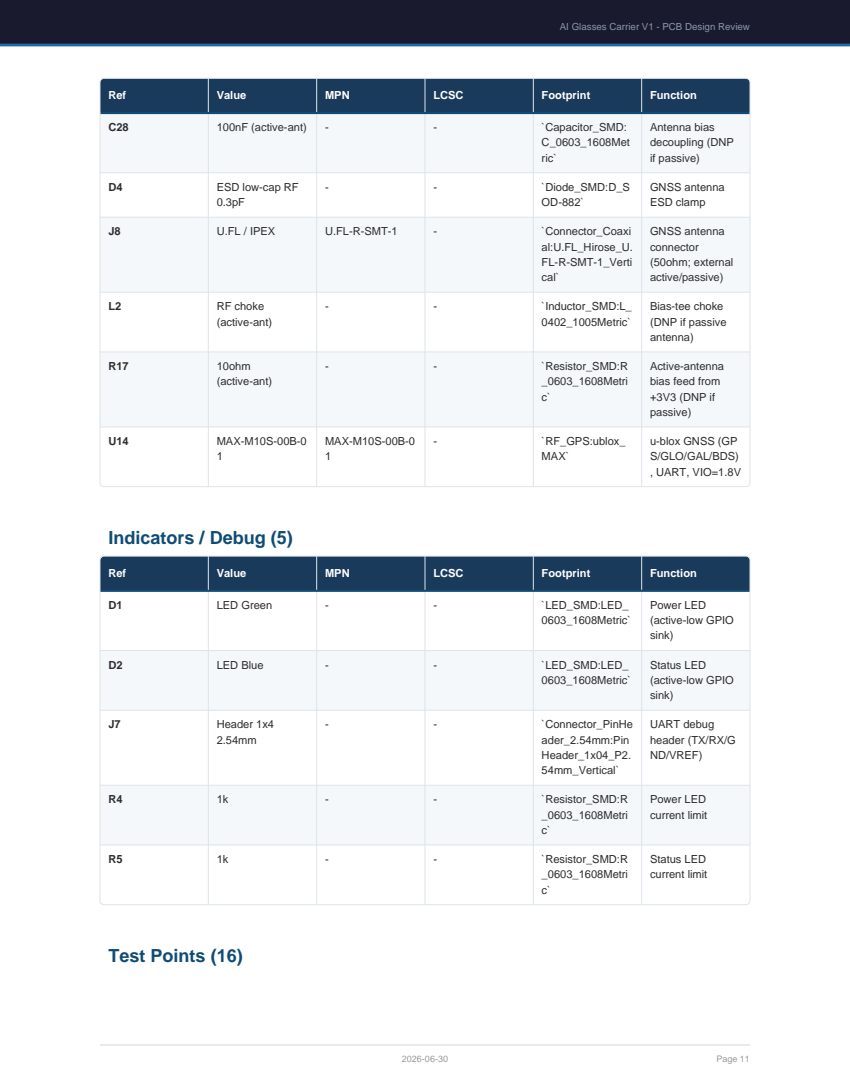
[picture p20: page 11]

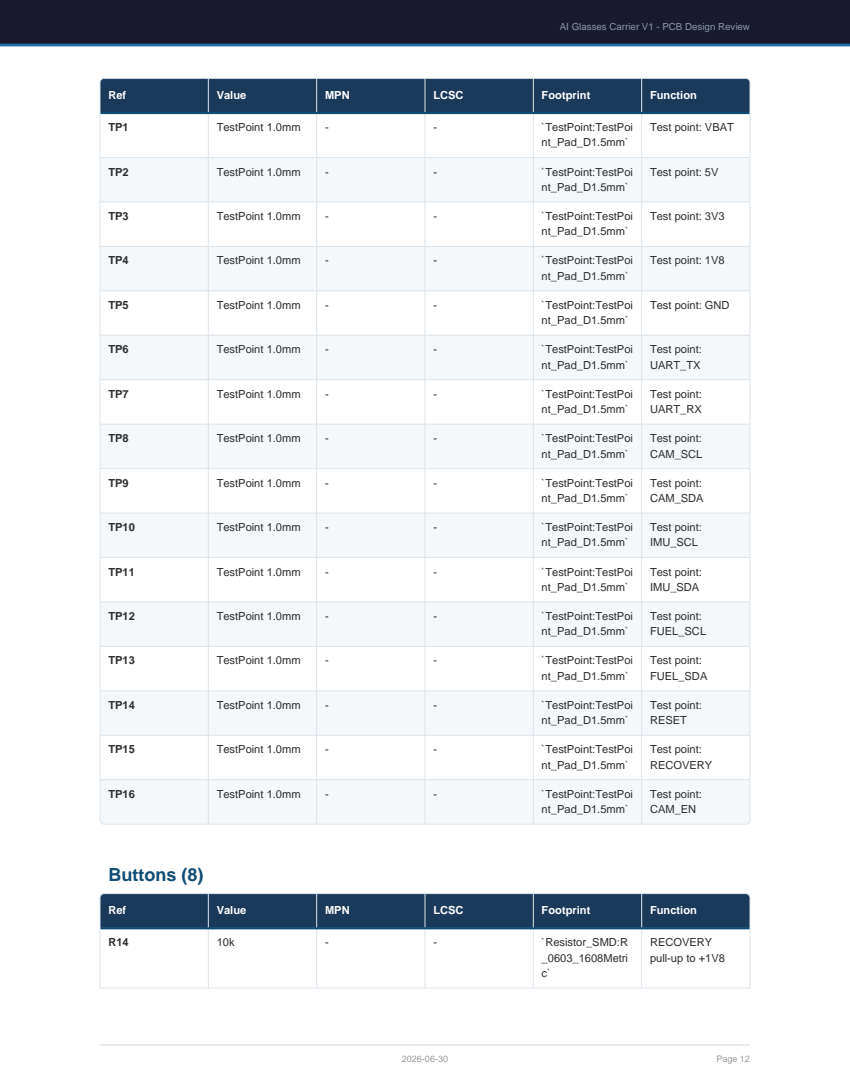
[picture p21: page 12]

Ref | Value | MPN | LCSC | Footprint | Function
R15 | 10k | - | - | `Resistor_SMD:R _0603_1608Metri c` | RESET pull-up to +1V8
R16 | 10k | - | - | `Resistor_SMD:R _0603_1608Metri c` | POWER_KEY pull-up to +1V8
R18 | 100k | - | - | `Resistor_SMD:R _0603_1608Metri c` | WL_nDIS pull-up to +1V8; default Wi-Fi enabled
R19 | 100k | - | - | `Resistor_SMD:R _0603_1608Metri c` | BT_nDIS pull-up to +1V8; default Bluetooth enabled
SW1 | Tact SW SMD | - | - | `Button_Switch_S MD:SW_Push_1P 1T_NO_CK_KMR 2` | RECOVERY / maskrom button (to GND)
SW2 | Tact SW SMD | - | - | `Button_Switch_S MD:SW_Push_1P 1T_NO_CK_KMR 2` | RESET button (to GND)
SW3 | Tact SW SMD | - | - | `Button_Switch_S MD:SW_Push_1P 1T_NO_CK_KMR 2`
POWER button
(to GND)

# 6. CM4 pin assignment (verified vs official pinout)

Function | Signal | Conn | Pin | CM4 net | Voltage
Power | +5V_IN | J3A | 77 | 5V_DCIN | 5V
Power | +5V_IN | J3A | 79 | 5V_DCIN | 5V
Power | +5V_IN | J3A | 81 | 5V_DCIN | 5V
Power | +5V_IN | J3A | 83 | 5V_DCIN | 5V
Power | +5V_IN | J3A | 85 | 5V_DCIN | 5V
Power | +5V_IN | J3A | 87 | 5V_DCIN | 5V
Power | GND | J3A/J3B/J1 | ALL_GND | GND | GND
Power | +3V3_OUT(CM4) | J3A | 84,86 | VCCIO6 | 3.3V
Power | +1V8_OUT(CM4) | J3A | 88,90 | VCC_1V8_S0 | 1.8V
Power | GPIO_VREF | J3A | 78 | GPIO_VREF | set=1.8V

Function | Signal | Conn | Pin | CM4 net | Voltage
Camera | MIPI_DPHY_CSI3 _RX_CLKP | J3B | 129 | MIPI_DPHY_CSI3 _RX_CLKP | diff_1V8 (100ohm)
Camera | MIPI_DPHY_CSI3 _RX_CLKN | J3B | 127 | MIPI_DPHY_CSI3 _RX_CLKN | diff_1V8 (100ohm)
Camera | MIPI_DPHY_CSI3 _RX_D0P | J3B | 117 | MIPI_DPHY_CSI3 _RX_D0P | diff_1V8 (100ohm)
Camera | MIPI_DPHY_CSI3 _RX_D0N | J3B | 115 | MIPI_DPHY_CSI3 _RX_D0N | diff_1V8 (100ohm)
Camera | MIPI_DPHY_CSI3 _RX_D1P | J3B | 123 | MIPI_DPHY_CSI3 _RX_D1P | diff_1V8 (100ohm)
Camera | MIPI_DPHY_CSI3 _RX_D1N | J3B | 121 | MIPI_DPHY_CSI3 _RX_D1N | diff_1V8 (100ohm)
Camera | MIPI_DPHY_CSI3 _RX_D2P | J3B | 135 | MIPI_DPHY_CSI3 _RX_D2P | diff_1V8 (100ohm)
Camera | MIPI_DPHY_CSI3 _RX_D2N | J3B | 133 | MIPI_DPHY_CSI3 _RX_D2N | diff_1V8 (100ohm)
Camera | MIPI_DPHY_CSI3 _RX_D3P | J3B | 141 | MIPI_DPHY_CSI3 _RX_D3P | diff_1V8 (100ohm)
Camera | MIPI_DPHY_CSI3 _RX_D3N | J3B | 139 | MIPI_DPHY_CSI3 _RX_D3N | diff_1V8 (100ohm)
Camera | I2C_CAM_SCL | J3A | 80 | I2C0_SCL_M1_T P | 1.8V (PMUIO1)
Camera | I2C_CAM_SDA | J3A | 82 | I2C0_SDA_M1_T P | 1.8V (PMUIO1)
Camera | CAM_RST_n | J3B | 143 | MIPI_CAM3_PDN _1V8 | 1.8V
Camera | CAM_MCLK | J1 | 59 | MIPI_CSI3_CAM_ CLKOUT_1V8 | 1.8V
PDM | PDM1_CLK1_M1 | J3B | 96 | PDM1_CLK1_M1 | 1.8V (VCCIO_AUDIO)
PDM | PDM1_SDI1_M1 | J3B | 94 | PDM1_SDI1_M1 | 1.8V (VCCIO_AUDIO)
PDM | PDM1_SDI2_M1 | J3B | 111 | PDM1_SDI2_M1 | 1.8V (VCCIO_AUDIO)
SAI | SAI1_SCLK | J1 | 25 | SAI1_SCLK_M0 | 1.8V (VCCIO_AUDIO)
SAI | SAI1_LRCK | J1 | 19 | SAI1_LRCK_M0 | 1.8V (VCCIO_AUDIO)
SAI | SAI1_SDO0 | J1 | 29 | SAI1_SDO0_M0 | 1.8V (VCCIO_AUDIO)

Function | Signal | Conn | Pin | CM4 net | Voltage
SAI | SAI1_MCLK | J1 | 23 | SAI1_MCLK_M0 | 1.8V (VCCIO_AUDIO)
Control | GPIO_SPKR_EN | J1 | 96 | SPK_CTL_H | 1.8V (VCCIO6)
USB | USB2_OTG0_DP | J3B | 105 | USB2_OTG0_DP | USB 3.3V analog (90ohm)
USB | USB2_OTG0_DM | J3B | 103 | USB2_OTG0_DM | USB 3.3V analog (90ohm)
UART | UART0_TX_M0_ DEBUG | J3A | 55 | UART0_TX_M0_ DEBUG | 1.8V (VCCIO6)
UART | UART0_RX_M0_ DEBUG | J3A | 51 | UART0_RX_M0_ DEBUG | 1.8V (VCCIO6)
GNSS | GNSS_UART_TX | J3A | 47 | UART7_TX_M0 | 1.8V (VCCIO6)
GNSS | GNSS_UART_RX | J3A | 45 | UART7_RX_M0 | 1.8V (VCCIO6)
GNSS | GNSS_PPS | J3A | 40 | SPI1_MISO_M0 | 1.8V (VCCIO6)
GNSS | GNSS_RST_n | J3A | 44 | SPI1_MOSI_M0 | 1.8V (VCCIO6)
Control | RECOVERY_n | J3A | 93 | MASKROM | 1.8V
Control | RESET_n | J3A | 92 | RESET_L | 1.8V
Control | POWER_KEY | J3A | 99 | PWRON_L | 1.8V
Control | WL_nDIS | J3A | 89 | WL_NDIS | 1.8V
Control | BT_nDIS | J3A | 91 | BT_NDIS | 1.8V
Control | LED_PWR_n | J3A | 95 | NPWR_LED | 1.8V (VCCIO6)
Control | LED_STATUS_n | J3A | 21 | PI_NLED_ACTIVI TY | 1.8V (VCCIO6)
I2C | I2C_IMU_SCL | J3A | 56 | I2C8_SCL_M1 | 1.8V (VCCIO6)
I2C | I2C_IMU_SDA | J3A | 58 | I2C8_SDA_M1 | 1.8V (VCCIO6)
Control | IMU_INT1 | J3A | 30 | GPIO1_C1 | 1.8V (VCCIO6)
Control | VIB_PWM | J3A | 48 | PWM1_CH0_M2 | 1.8V (VCCIO6)
Control | VIB_EN | J3A | 34 | CAN1_TX_M3 | 1.8V (VCCIO6)
I2C | FUEL_I2C_SCL | J3A | 35 | I2C6_SCL_M3 | 1.8V (VCCIO6)
I2C | FUEL_I2C_SDA | J3A | 36 | I2C6_SDA_M3 | 1.8V (VCCIO6)
Control | CHG_INT_n | J3A | 37 | SPI1_CSN1_M0 | 1.8V (VCCIO6)
Control | LOW_BAT_INT_n | J3A | 39 | SPI1_CSN0_M0 | 1.8V (VCCIO6)

# 7. Passive component spec audit

## 7.1 Resistors - value, tolerance, package, tempco, power

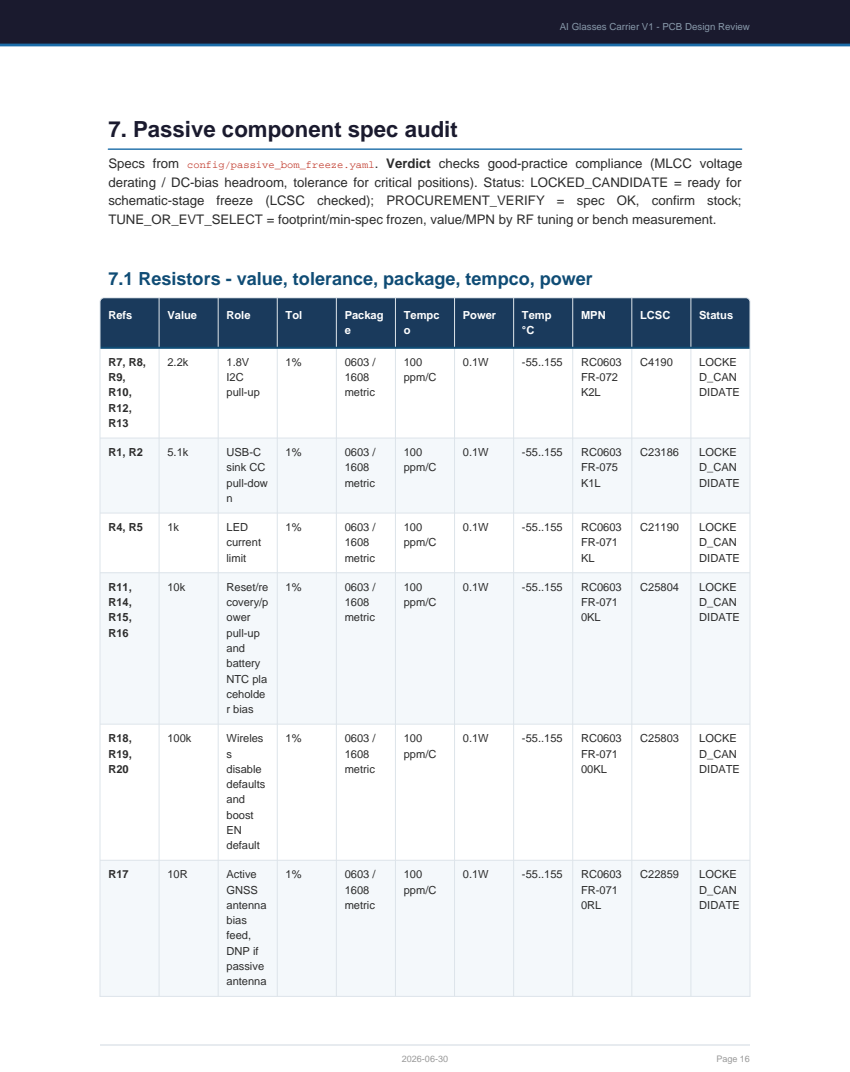
[picture p22: page 16]
Refs; Value; Role; Tol; Packag; Tempc o; Power; Temp; MPN; LCSC; Status; I2C pull-up; 1608 metric; 100 ppm/C; LOCKE; D_CAN DIDATE; USB-C; sink CC pull-dow n; LED; current limit; Reset/re; covery/p ower pull-up and battery NTC pla ceholde r bias; Wireles; s disable defaults and boost EN default; Active; GNSS antenna bias feed, DNP if passive antenna

Specs from config/passive_bom_freeze.yaml. Verdict checks good-practice compliance (MLCC voltage
derating / DC-bias headroom, tolerance for critical positions). Status: LOCKED_CANDIDATE = ready for
schematic-stage freeze (LCSC checked); PROCUREMENT_VERIFY = spec OK, confirm stock;
TUNE_OR_EVT_SELECT = footprint/min-spec frozen, value/MPN by RF tuning or bench measurement.

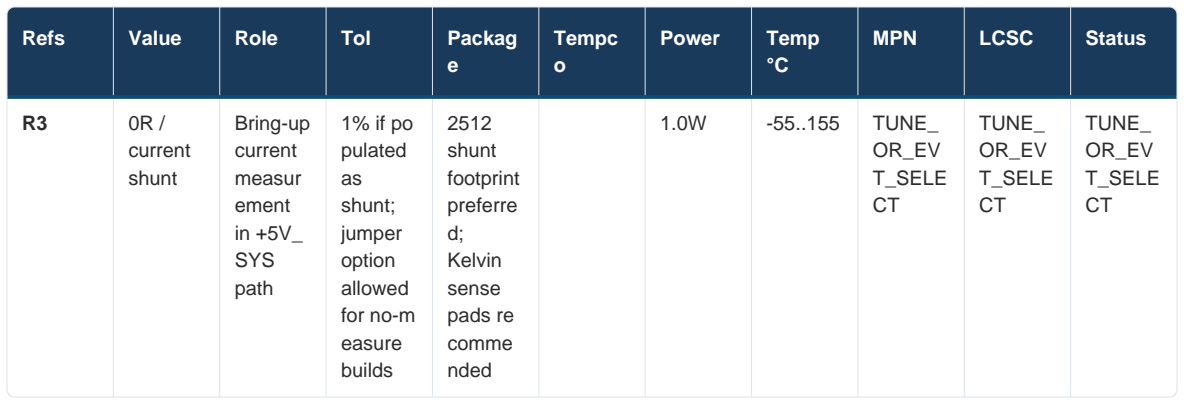
[picture p23: figure]
Refs; Value; Role; Tol; Packag; Tempc o; Power; Temp; MPN; LCSC; Status; current shunt; Bring-up current measur ement in +5V_ SYS path; 1% if po pulated as shunt; jumper option allowed for no-m easure builds; 2512 shunt footprint preferre d; Kelvin sense pads re comme nded; TUNE_; OR_EV T_SELE CT; TUNE_ OR_EV T_SELE CT

### Resistor verdicts:

- [OK] R7, R8, R9, R10, R12, R13 (2.2k): I2C pull-up; 2.2k valid for ~100-400 pF bus at <=400 kHz -confirm vs actual bus capacitance after layout.
- [OK] R1, R2 (5.1k): USB-C CC sink pull-down - 1% locked (correct per spec).
- [OK] R4, R5 (1k): LED current-limit - 1% fine (5% also OK).
- [OK] R11, R14, R15, R16 (10k): Reset/recovery/power pull-up and battery NTC placeholder bias -tolerance 1%.
- [OK] R18, R19, R20 (100k): Wireless disable defaults and boost EN default - tolerance 1%.
- [OK] R17 (10R): Active GNSS antenna bias feed, DNP if passive antenna - tolerance 1%.
- [!] R3 (0R / current shunt): 0ohm/shunt in the 5V high-current path - do NOT use a tiny 0603; select a real mohm shunt (0.005-0.02ohm, 2512, Kelvin) or a 1% jumper.

## 7.2 Capacitors - value, voltage, dielectric, package, temp

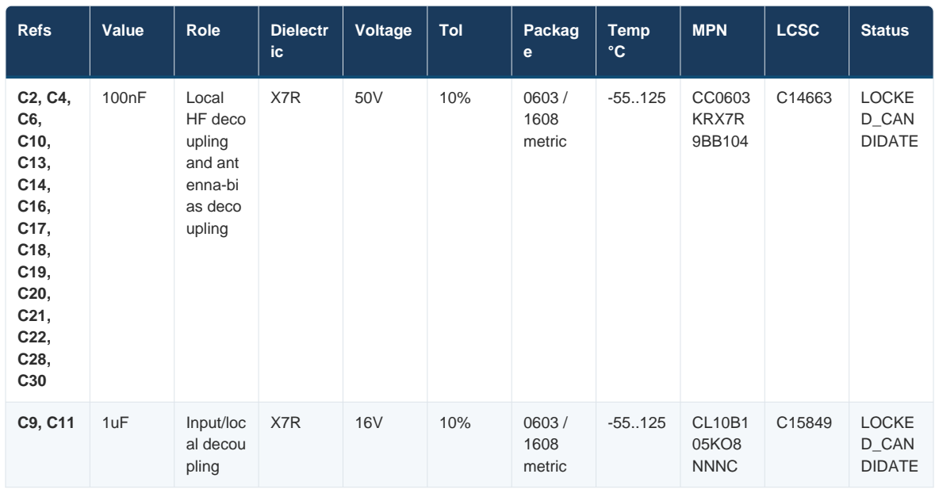
[picture p24: figure]
Refs; Value; Role; Dielectr; Voltage; Tol; Packag; Temp °C; MPN; LCSC; Status; Local; HF deco upling and ant enna-bi as deco upling; 1608 metric; KRX7R 9BB104; LOCKE; D_CAN DIDATE; Input/loc; al decou pling; 05KO8 NNNC
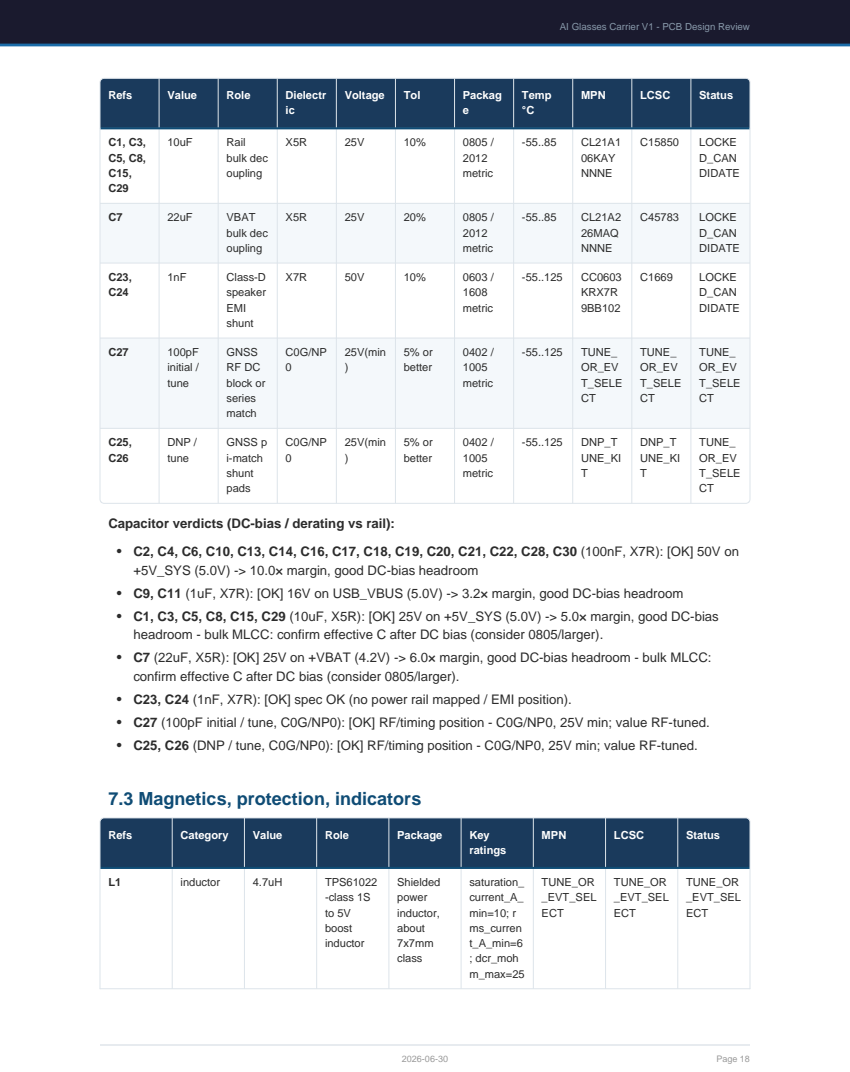
[picture p25: page 18]

Capacitor verdicts (DC-bias / derating vs rail):
+5V_SYS (5.0V) -> 10.0× margin, good DC-bias headroom
• C9, C11 (1uF, X7R): [OK] 16V on USB_VBUS (5.0V) -> 3.2× margin, good DC-bias headroom
• C1, C3, C5, C8, C15, C29 (10uF, X5R): [OK] 25V on +5V_SYS (5.0V) -> 5.0× margin, good DC-bias
headroom - bulk MLCC: confirm effective C after DC bias (consider 0805/larger).
• C7 (22uF, X5R): [OK] 25V on +VBAT (4.2V) -> 6.0× margin, good DC-bias headroom - bulk MLCC:
confirm effective C after DC bias (consider 0805/larger).
• C23, C24 (1nF, X7R): [OK] spec OK (no power rail mapped / EMI position).
• C27 (100pF initial / tune, C0G/NP0): [OK] RF/timing position - C0G/NP0, 25V min; value RF-tuned.
• C25, C26 (DNP / tune, C0G/NP0): [OK] RF/timing position - C0G/NP0, 25V min; value RF-tuned.

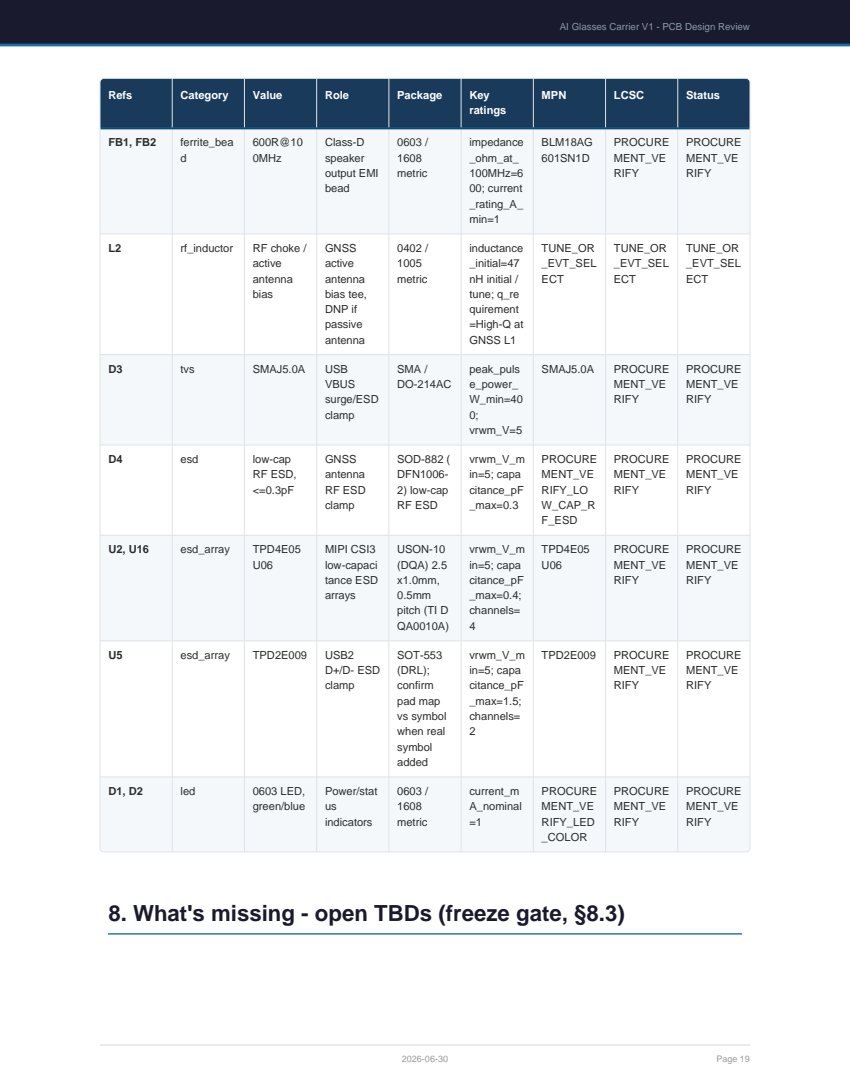
[picture p26: page 19]

8. What's missing - open TBDs (freeze gate, §8.3)

ID | Resolved | Must confirm
`CM4_SKU` | [OK] | CONFIRMED RM126-D4E32J0R35W28: RK3576 / 4GB LPDDR4X / 32GB eMMC / Wi-Fi6+BT5.x. Antenna form tracked under ANTENNA.
`CAMERA_ELECTRICAL_PINOUT` | [OK] | RESOLVED: camera module is Radxa Camera 4K / Sony IMX415-AAQR-C; 31-pin FPC pinout captured in CM4_IM X415_design_files/Radxa_Camera_4K_ 31pin_pinout.csv and cross-referenced in docs/p0_p1_decisions_2026-06-28.md.
`CAMERA_CONNECTOR_MPN` | [OK] | RESOLVED: carrier J2 connector is Hirose FH35C-31S-0.3SHW(50), LCSC C424662. Footprint has been generated from the Hirose 2D drawing.
`CAMERA_CABLE` | [OK] | RESOLVED: use Radxa AC006, 31P 0.3mm to 31P 0.3mm, opposite-side FPC. Do not use AC008; AC008 is 31P to 15P.
`CAMERA_SCHEMATIC_GATE` | [OK] | RESOLVED for schematic stage: J2 pins 1-31, CSI3 4-lane mapping, P/N polarity, I2C/MCLK/RESET, voltage domains, power pins and NC pins are checked by scripts/audit_csi3_camera.py. RESET is active-low on project net CAM_RST_n; no PWDN pin is present in the Radxa Camera 4K 31-pin pinout.
`CAMERA_KICAD_IMPLEMENTATION ` | [X] | PARTIAL: schematic source now uses 31-pin FH35C/Radxa Cam4K pinout on CM4 CSI3 4-lane, and the FH35C footprint has been regenerated from the Hirose 2D drawing. DEFERRED_TO_PRE_LAYOUT: AC006 physical validation, FPC contact side, FPC insertion direction, J2 Pin 1 physical check, 1:1 print, coupon test, and FPC bend/enclosure path. Official CM4 IO overlay radxa-cm4-io-radxa-camera-4k.dtbo is confirmed. Bring-up logs (dmesg/media/v4l2) remain open for EVT.
`AUDIO_PARTS` | [OK] | CONFIRMED: 2×SPH0641LU4H-1 mic, MAX98357AETE+T (C910544) amp, Ole Wolff OWS-091630W50A-8 8ohm/1W (C5840086) speaker

ID | Resolved | Must confirm
`GNSS_MODULE` | [OK] | CONFIRMED u-blox MAX-M10S-00B-01: UART, VCC=3.3V/VIO=1.8V, 50ohm U.FL, external active antenna (-match + bias-tee, DNP for passive)
`BATTERY` | [OK] | Reverse-calc: 1S 2-3×(35×18×4mm ~250mAh)=500-750mAh/1.85-2.8Wh. V1 bench use ~1.5-2Ah. >3-4h target needs AI duty-cycling (system-power issue, see report)
`POWER_5V` | [OK] | CONSERVATIVE FREEZE: keep TPS61022-class 1S->5V boost and design +5V_SYS for >=4A bench/boost margin. R3 remains the bring-up shunt/0R measurement point; final peak/thermal validation is deferred to bench testing.
`ANTENNA` | [OK] | CONSERVATIVE FREEZE: Wi-Fi/BT stays on the CM4 module/U.FL path; carrier does not add 2.4/5GHz RF routing. Layout must reserve the CM4 antenna keep-out and keep battery, metal hinge/screws, speaker magnet, and copper away from the antenna zone.
`BOARD_OUTLINE` | [X] | SOURCE GEOMETRY RESOLVED: CM4 module outline = 40.02x54.98mm from official DXF; CM4/IO Board DXF, STEP, placement map and dimensions drawing are the mechanical inputs. OPEN: project must freeze board length/width/radius, USB-C/camera/battery/debug exit direction, mounting holes, and battery-vs-CM4 position.
`B2B_CONNECTOR` | [X] | SOURCE FILES RESOLVED: carrier receptacle DF40C-100DS-0.4V(51), module plug DF40C-100DP-0.4V(51), 1.5mm mated height. OPEN: build 2-layer connector-only fit-check board and verify all three connectors press in together with no module lift/skew.
`PINMUX` | [OK] | PDM/SAI/I2C/UART/GPIO conflict map + Device Tree

Plus schematic-stage structural gaps: no footprints placed on PCB (skeleton), VERIFY placeholder footprints (§4), and the carrier board outline + B2B connector XY (needs official CM4 DXF/STEP aligned in KiCad).

# 9. Key recommendations

1. USB-C CC (R1/R2, 5.1k): locked at 1% [OK] - keep. Sink-role pull-downs to GND.
2. I2C pull-ups (2.2k, R7-R13): validate against measured bus capacitance after layout; 2.2k suits <=400 kHz / <=~400 pF. Camera I2C0, IMU I2C8, charger/fuel I2C6 are separate buses.
3. 5V-rail MLCC: 10µF is 25V X5R / 1µF is 16V / 100nF is 50V -> all >=2× the 5V rail, good DC-bias margin. Still confirm effective capacitance of 10µF/0805 after DC bias on +5V_SYS.
4. VBAT bulk (C7, 22µF/25V): fine for 4.2V; high glasses-cell C-rate means keep/expand bulk near the boost input.
5. R3 current shunt: replace the 0ohm placeholder with a defined mohm shunt (2512, Kelvin) before measuring 5V power, or populate a 1% jumper for no-measure builds.
6. GNSS RF (C25/C26/C27, L2): C0G/NP0, values RF-tuned with the chosen antenna; C25/C26 stay DNP unless tuning needs shunt C; bias-tee (L2/R17/C28) DNP for a passive antenna.
7. Boost inductor (L1): select a >=10A-saturation shielded part sized to the measured 5V peak; footprint is a VERIFY placeholder.
8. Replace all `VERIFY` footprints (B2B, ESD arrays, RF ESD, inductor) with purchasable, library-verified footprints before layout.

# Appendix A - full pin -> net connections

Ref | Pin | Net
J31 | P77-87 +5V | +5V_SYS
J31 | P78 VREF->1V8 | +1V8
J31 | GND | GND
J31 | P55 DBG_TX | UART_DBG_TX
J31 | P51 DBG_RX | UART_DBG_RX
J31 | P47 GNSS_TX | GNSS_UART_TX
J31 | P45 GNSS_RX | GNSS_UART_RX
J31 | P40 GNSS_PPS | GNSS_PPS
J31 | P44 GNSS_RST | GNSS_RST_n
J31 | P80 CAM_SCL | CAM_I2C_SCL
J31 | P82 CAM_SDA | CAM_I2C_SDA
J31 | P56 IMU_SCL | IMU_I2C_SCL
J31 | P58 IMU_SDA | IMU_I2C_SDA
J31 | P35 FUEL_SCL | FUEL_I2C_SCL

Ref | Pin | Net
J31 | P36 FUEL_SDA | FUEL_I2C_SDA
J31 | P30 IMU_INT | IMU_INT1
J31 | P48 VIB_PWM | VIB_PWM
J31 | P34 VIB_EN | VIB_EN
J31 | P37 CHG_INT | CHG_INT_n
J31 | P39 LBAT_INT | LOW_BAT_INT_n
J31 | P95 LED_PWR | LED_PWR_n
J31 | P21 LED_STAT | LED_STATUS_n
J31 | P93 RECOVERY | RECOVERY_n
J31 | P92 RESET | RESET_n
J31 | P99 PWR_KEY | POWER_KEY
J31 | P89 WL_DIS | WL_nDIS
J31 | P91 BT_DIS | BT_nDIS
J32 | P129 CSI3_CLKP | MIPI_CSI3_CLK_P
J32 | P127 CSI3_CLKN | MIPI_CSI3_CLK_N
J32 | P117 CSI3_D0P | MIPI_CSI3_D0_P
J32 | P115 CSI3_D0N | MIPI_CSI3_D0_N
J32 | P123 CSI3_D1P | MIPI_CSI3_D1_P
J32 | P121 CSI3_D1N | MIPI_CSI3_D1_N
J32 | P135 CSI3_D2P | MIPI_CSI3_D2_P
J32 | P133 CSI3_D2N | MIPI_CSI3_D2_N
J32 | P141 CSI3_D3P | MIPI_CSI3_D3_P
J32 | P139 CSI3_D3N | MIPI_CSI3_D3_N
J32 | P143 CAM3_GPIO | CAM_RST_n
J32 | P105 USB_DP | USB_DP
J32 | P103 USB_DM | USB_DM
J32 | P96 PDM_CLK | PDM1_CLK
J32 | P94 PDM_D0 | PDM1_DATA0
J32 | P111 PDM_D1 | PDM1_DATA1
J32 | GND | GND
J1 | P25 SAI_BCLK | SAI1_BCLK

Ref | Pin | Net
J1 | P19 SAI_LRCK | SAI1_LRCK
J1 | P29 SAI_SDO | SAI1_SDO
J1 | P23 SAI_MCLK_UNUSED | NC
J1 | P59 CAM3_MCLK | CAM_MCLK
J1 | P96 SPK_EN | SPKR_EN_n
J1 | +1V8 (P88/90) | +1V8
J1 | GND | GND
J2 | 1 GND | GND
J2 | 2 MDN4 | MIPI_CSI3_D3_N
J2 | 3 MDP4 | MIPI_CSI3_D3_P
J2 | 4 GND | GND
J2 | 5 MDN3 | MIPI_CSI3_D2_N
J2 | 6 MDP3 | MIPI_CSI3_D2_P
J2 | 7 GND | GND
J2 | 8 NC | NC
J2 | 9 NC | NC
J2 | 10 GND | GND
J2 | 11 MDN2 | MIPI_CSI3_D1_N
J2 | 12 MDP2 | MIPI_CSI3_D1_P
J2 | 13 GND | GND
J2 | 14 MDN1 | MIPI_CSI3_D0_N
J2 | 15 MDP1 | MIPI_CSI3_D0_P
J2 | 16 GND | GND
J2 | 17 MCN | MIPI_CSI3_CLK_N
J2 | 18 MCP | MIPI_CSI3_CLK_P
J2 | 19 GND | GND
J2 | 20 MCLK | CAM_MCLK
J2 | 21 GND | GND
J2 | 22 NC | NC
J2 | 23 NC | NC
J2 | 24 SCL | CAM_I2C_SCL

Ref | Pin | Net
J2 | 25 SDA | CAM_I2C_SDA
J2 | 26 NC | NC
J2 | 27 RESET_N | CAM_RST_n
J2 | 28 VCC3.3V | +CAM_3V3
J2 | 29 VCC3.3V | +CAM_3V3
J2 | 30 VCC5V | +5V_SYS
J2 | 31 VCC5V | +5V_SYS
U2 | CLK_P | MIPI_CSI3_CLK_P
U2 | CLK_N | MIPI_CSI3_CLK_N
U2 | D0_P | MIPI_CSI3_D0_P
U2 | D0_N | MIPI_CSI3_D0_N
U2 | D1_P | MIPI_CSI3_D1_P
U2 | D1_N | MIPI_CSI3_D1_N
U2 | GND | GND
U16 | D2_P | MIPI_CSI3_D2_P
U16 | D2_N | MIPI_CSI3_D2_N
U16 | D3_P | MIPI_CSI3_D3_P
U16 | D3_N | MIPI_CSI3_D3_N
U16 | GND | GND
U3 | VIN | +5V_SYS
U3 | EN | CAM_PWR_EN
U3 | GND | GND
U3 | VOUT | +CAM_3V3
R7 | 1 | +1V8
R7 | 2 | CAM_I2C_SCL
R8 | 1 | +1V8
R8 | 2 | CAM_I2C_SDA
C8 | 1 | +CAM_3V3
C8 | 2 | GND
C9 | 1 | +CAM_3V3
C9 | 2 | GND

Ref | Pin | Net
C10 | 1 | +CAM_3V3
C10 | 2 | GND
C29 | 1 | +5V_SYS
C29 | 2 | GND
C30 | 1 | +5V_SYS
C30 | 2 | GND
MK1 | VDD | +1V8
MK1 | CLK | PDM1_CLK
MK1 | DATA | PDM1_DATA0
MK1 | SEL | GND
MK1 | GND | GND
MK2 | VDD | +1V8
MK2 | CLK | PDM1_CLK
MK2 | DATA | PDM1_DATA1
MK2 | SEL | +1V8
MK2 | GND | GND
U4 | VDD | +5V_SYS
U4 | GND | GND
U4 | BCLK | SAI1_BCLK
U4 | LRC | SAI1_LRCK
U4 | DIN | SAI1_SDO
U4 | SD | SPKR_EN_n
U4 | GAIN | GND
U4 | OUT+ | SPK_OUT_P
U4 | OUT- | SPK_OUT_N
FB1 | 1 | SPK_OUT_P
FB1 | 2 | SPK_P_F
FB2 | 1 | SPK_OUT_N
FB2 | 2 | SPK_N_F
C23 | 1 | SPK_P_F
C23 | 2 | GND

Ref | Pin | Net
C24 | 1 | SPK_N_F
C24 | 2 | GND
J3 | SPK+ | SPK_P_F
J3 | SPK- | SPK_N_F
C13 | 1 | +5V_SYS
C13 | 2 | GND
J4 | VBUS | USB_VBUS
J4 | GND | GND
J4 | DP | USB_DP
J4 | DM | USB_DM
J4 | CC1 | USB_CC1
J4 | CC2 | USB_CC2
J4 | SHLD | GND
U5 | DP | USB_DP
U5 | DM | USB_DM
U5 | GND | GND
R1 | 1 | USB_CC1
R1 | 2 | GND
R2 | 1 | USB_CC2
R2 | 2 | GND
D3 | 1 | USB_VBUS
D3 | 2 | GND
U15 | IN | USB_VBUS
U15 | EN | USB_VBUS
U15 | GND | GND
U15 | OUT | VBUS_PROT
R3 | 1 | VBUS_PROT
R3 | 2 | +5V_SYS
C11 | 1 | USB_VBUS
C11 | 2 | GND
U12 | VIN | +5V_SYS

Ref | Pin | Net
U12 | GND | GND
U12 | VOUT | +3V3
U13 | VIN | +3V3
U13 | GND | GND
U13 | VOUT | +1V8
C1 | 1 | +5V_SYS
C1 | 2 | GND
C2 | 1 | +5V_SYS
C2 | 2 | GND
C3 | 1 | +3V3
C3 | 2 | GND
C4 | 1 | +3V3
C4 | 2 | GND
C5 | 1 | +1V8
C5 | 2 | GND
C6 | 1 | +1V8
C6 | 2 | GND
U6 | VIN | +VBAT
U6 | SW | BOOST_SW
U6 | EN | BOOST_EN
U6 | FB | +5V_SYS
U6 | GND | GND
R20 | 1 | +VBAT
R20 | 2 | BOOST_EN
L1 | 1 | +VBAT
L1 | 2 | BOOST_SW
U7 | IN | USB_VBUS
U7 | SYS | +VBAT
U7 | BAT | VBAT_P
U7 | TS | BAT_NTC
U7 | SCL | FUEL_I2C_SCL

Ref | Pin | Net
U7 | SDA | FUEL_I2C_SDA
U7 | INT | CHG_INT_n
U7 | GND | GND
U8 | VDD | VBAT_P
U8 | VM | VBAT_N
U8 | OUT | +VBAT
U9 | VDD | +VBAT
U9 | CELL | +VBAT
U9 | SCL | FUEL_I2C_SCL
U9 | SDA | FUEL_I2C_SDA
U9 | ALRT | LOW_BAT_INT_n
U9 | GND | GND
J5 | BAT+ | VBAT_P
J5 | BAT- | VBAT_N
J5 | NTC | BAT_NTC
C7 | 1 | +VBAT
C7 | 2 | GND
R11 | 1 | BAT_NTC
R11 | 2 | GND
U10 | VDD | +1V8
U10 | GND | GND
U10 | SCL | IMU_I2C_SCL
U10 | SDA | IMU_I2C_SDA
U10 | INT1 | IMU_INT1
R9 | 1 | +1V8
R9 | 2 | IMU_I2C_SCL
R10 | 1 | +1V8
R10 | 2 | IMU_I2C_SDA
U11 | VDD | +5V_SYS
U11 | GND | GND
U11 | IN | VIB_PWM

Ref | Pin | Net
U11 | EN | VIB_EN
U11 | OUT+ | VIB_OUT_P
U11 | OUT- | VIB_OUT_N
J6 | M+ | VIB_OUT_P
J6 | M- | VIB_OUT_N
U14 | VCC | +3V3
U14 | V_IO | +1V8
U14 | V_BCKP | +3V3
U14 | GND | GND
U14 | TXD | GNSS_UART_RX
U14 | RXD | GNSS_UART_TX
U14 | TIMEPULSE | GNSS_PPS
U14 | RESET_N | GNSS_RST_n
U14 | RF_IN | GNSS_RFIN
C27 | 1 | GNSS_RFIN
C27 | 2 | GNSS_ANT
C25 | 1 | GNSS_RFIN
C25 | 2 | GND
C26 | 1 | GNSS_ANT
C26 | 2 | GND
L2 | 1 | GNSS_ANT
L2 | 2 | V_ANT_BIAS
R17 | 1 | +3V3
R17 | 2 | V_ANT_BIAS
C28 | 1 | V_ANT_BIAS
C28 | 2 | GND
J8 | ANT | GNSS_ANT
J8 | GND | GND
C14 | 1 | +3V3
C14 | 2 | GND
C15 | 1 | +3V3

Ref | Pin | Net
C15 | 2 | GND
D1 | A | LED_PWR_A
D1 | K | LED_PWR_n
R4 | 1 | +3V3
R4 | 2 | LED_PWR_A
D2 | A | LED_STAT_A
D2 | K | LED_STATUS_n
R5 | 1 | +3V3
R5 | 2 | LED_STAT_A
J7 | TX | UART_DBG_TX
J7 | RX | UART_DBG_RX
J7 | GND | GND
J7 | VREF | +3V3
TP1 | 1 | +VBAT
TP2 | 1 | +5V_SYS
TP3 | 1 | +3V3
TP4 | 1 | +1V8
TP5 | 1 | GND
TP6 | 1 | UART_DBG_TX
TP7 | 1 | UART_DBG_RX
TP8 | 1 | CAM_I2C_SCL
TP9 | 1 | CAM_I2C_SDA
TP10 | 1 | IMU_I2C_SCL
TP11 | 1 | IMU_I2C_SDA
TP12 | 1 | FUEL_I2C_SCL
TP13 | 1 | FUEL_I2C_SDA
TP14 | 1 | RESET_n
TP15 | 1 | RECOVERY_n
TP16 | 1 | CAM_PWR_EN
SW1 | 1 | RECOVERY_n
SW1 | 2 | GND

Ref | Pin | Net
SW2 | 1 | RESET_n
SW2 | 2 | GND
SW3 | 1 | POWER_KEY
SW3 | 2 | GND
R14 | 1 | +1V8
R14 | 2 | RECOVERY_n
R15 | 1 | +1V8
R15 | 2 | RESET_n
R16 | 1 | +1V8
R16 | 2 | POWER_KEY
R18 | 1 | +1V8
R18 | 2 | WL_nDIS
R19 | 1 | +1V8
R19 | 2 | BT_nDIS
R12 | 1 | +1V8
R12 | 2 | FUEL_I2C_SCL
R13 | 1 | +1V8
R13 | 2 | FUEL_I2C_SDA
C16 | 1 | +1V8
C16 | 2 | GND
C17 | 1 | USB_VBUS
C17 | 2 | GND
C18 | 1 | +VBAT
C18 | 2 | GND
C19 | 1 | +VBAT
C19 | 2 | GND
C20 | 1 | +5V_SYS
C20 | 2 | GND
C21 | 1 | +3V3
C21 | 2 | GND
C22 | 1 | +1V8

Ref | Pin | Net
C22 | 2 | GND
D4 | 1 | GNSS_ANT
D4 | 2 | GND

_Generated by scripts/generate_design_review.py from working sources (carrier_bom.py, cm4_pinmap.py, config/passive_bom_freeze.yaml, ai_context/*.json). Native KiCad/XLSX remain the source of truth (repo
CLAUDE.md)._
