lhongyi-ai/AI_Goggles/v2_chipdown/reports/output/AI_Glasses_V2_Phase1_5_Floorplan.pdf

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

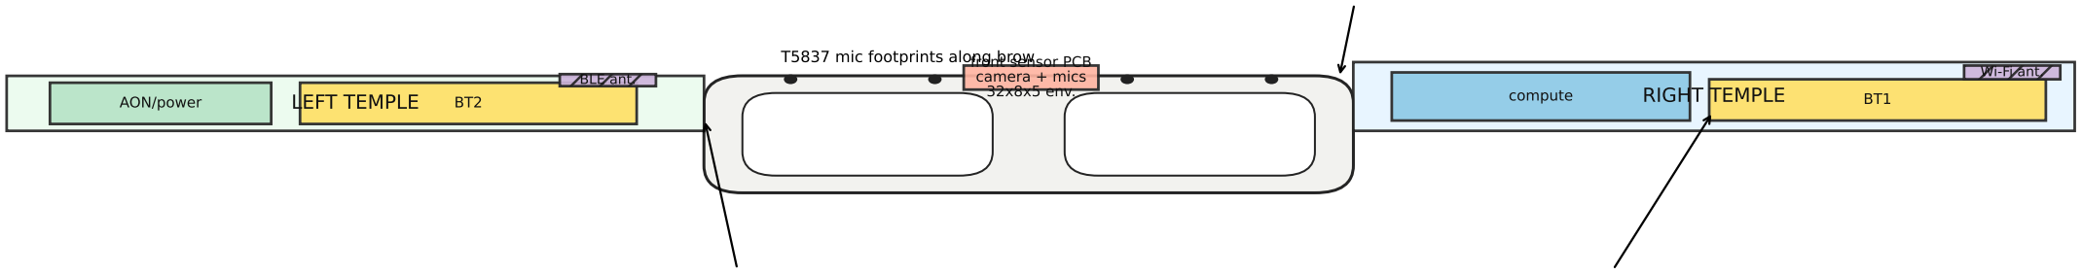
[picture p27: figure]
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
