lhongyi-ai/AI_Goggles/v2_chipdown/reports/output/mechanical_options/AI_Glasses_V2_Narrow_Temple_Option1.pdf

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

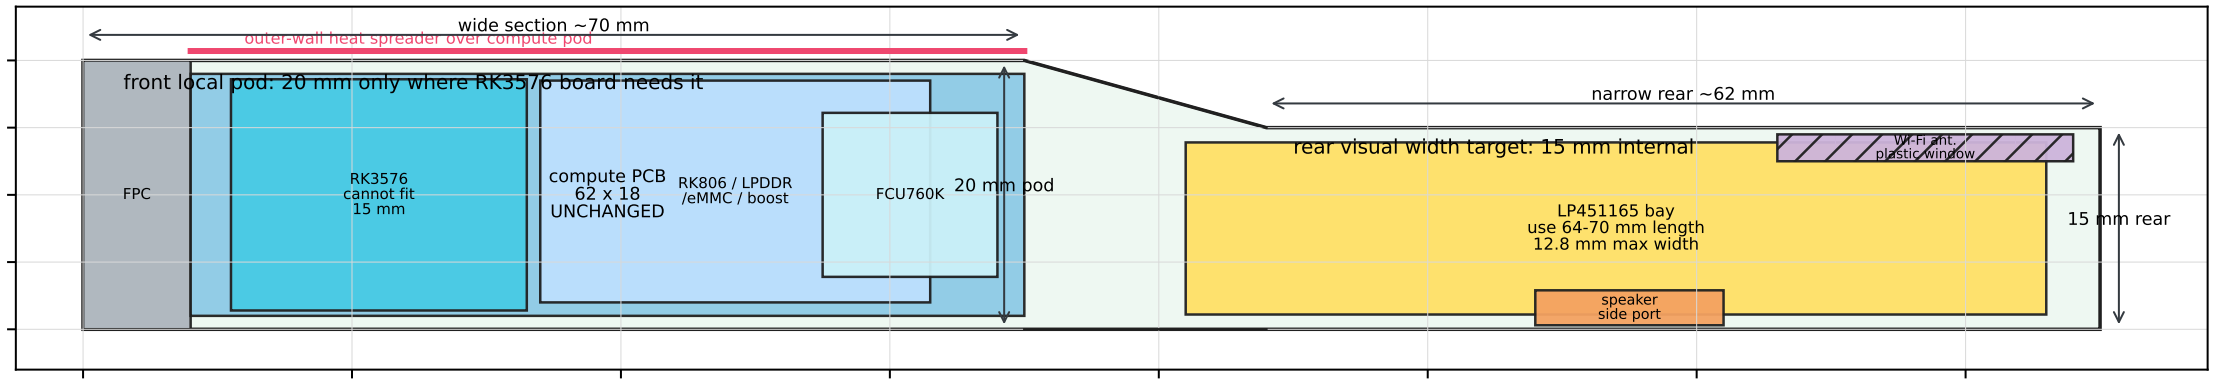
[picture p28: figure]
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
