lhongyi-ai/AI_Goggles/v2_chipdown/mechanical_3d/renders/01_transparent_overview.png

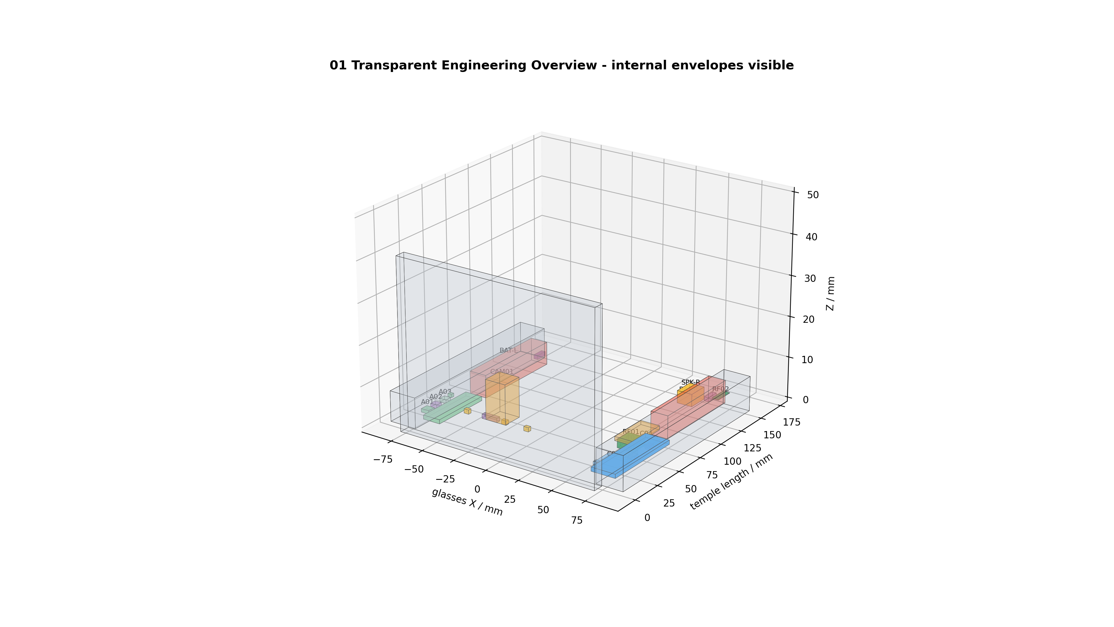
v2_chipdown/mechanical_3d/renders/01_transparent_overview.png
