lhongyi-ai/AI_Goggles/v2_chipdown/mechanical_3d/renders/02_external_view.png

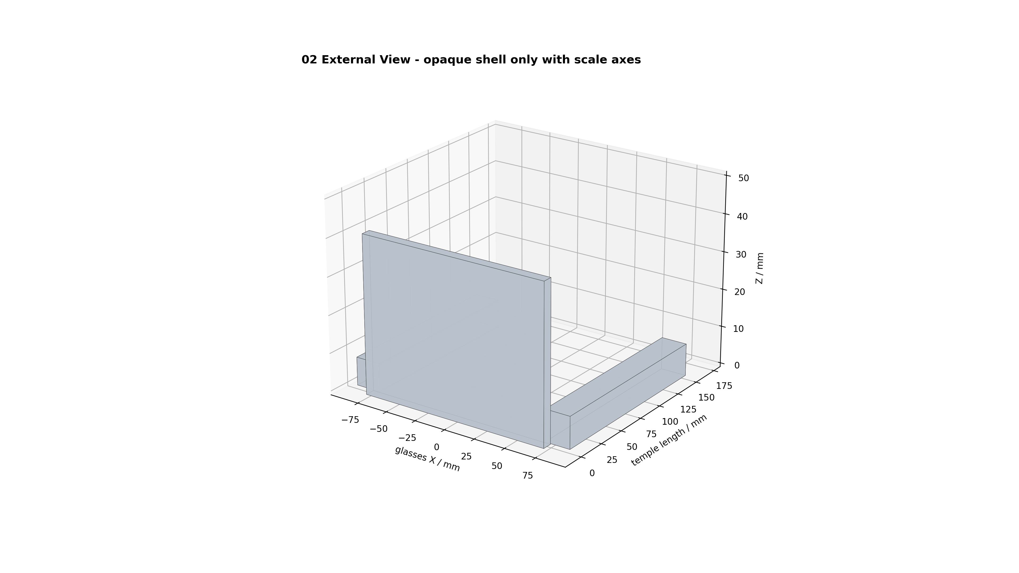
v2_chipdown/mechanical_3d/renders/02_external_view.png
