lhongyi-ai/AI_Goggles/v2_chipdown/mechanical_3d/renders/04_right_side.png

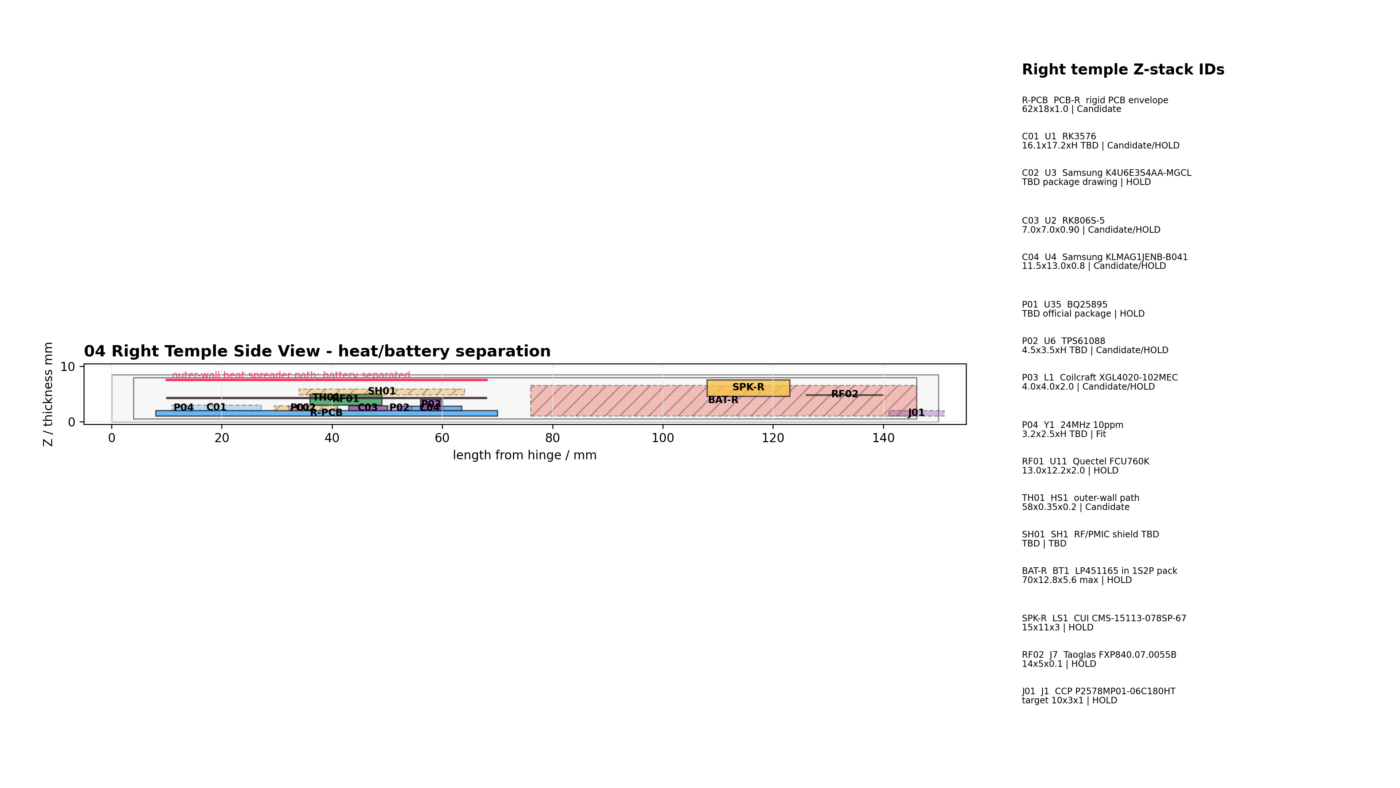
v2_chipdown/mechanical_3d/renders/04_right_side.png
