lhongyi-ai/AI_Goggles/v2_chipdown/mechanical_3d/renders/05_left_top.png

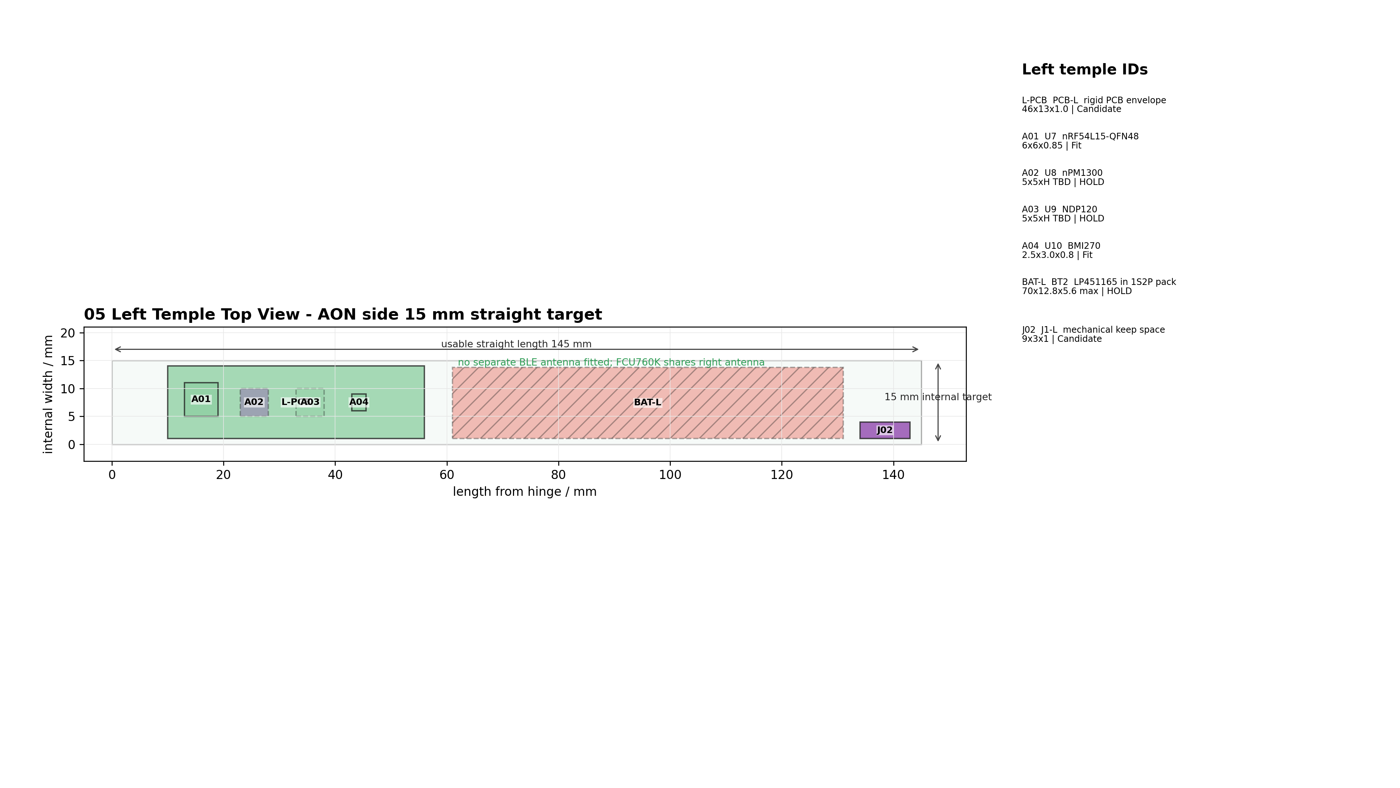
v2_chipdown/mechanical_3d/renders/05_left_top.png
