lhongyi-ai/AI_Goggles/v2_chipdown/mechanical_3d/renders/08_soc_thermal_section.png

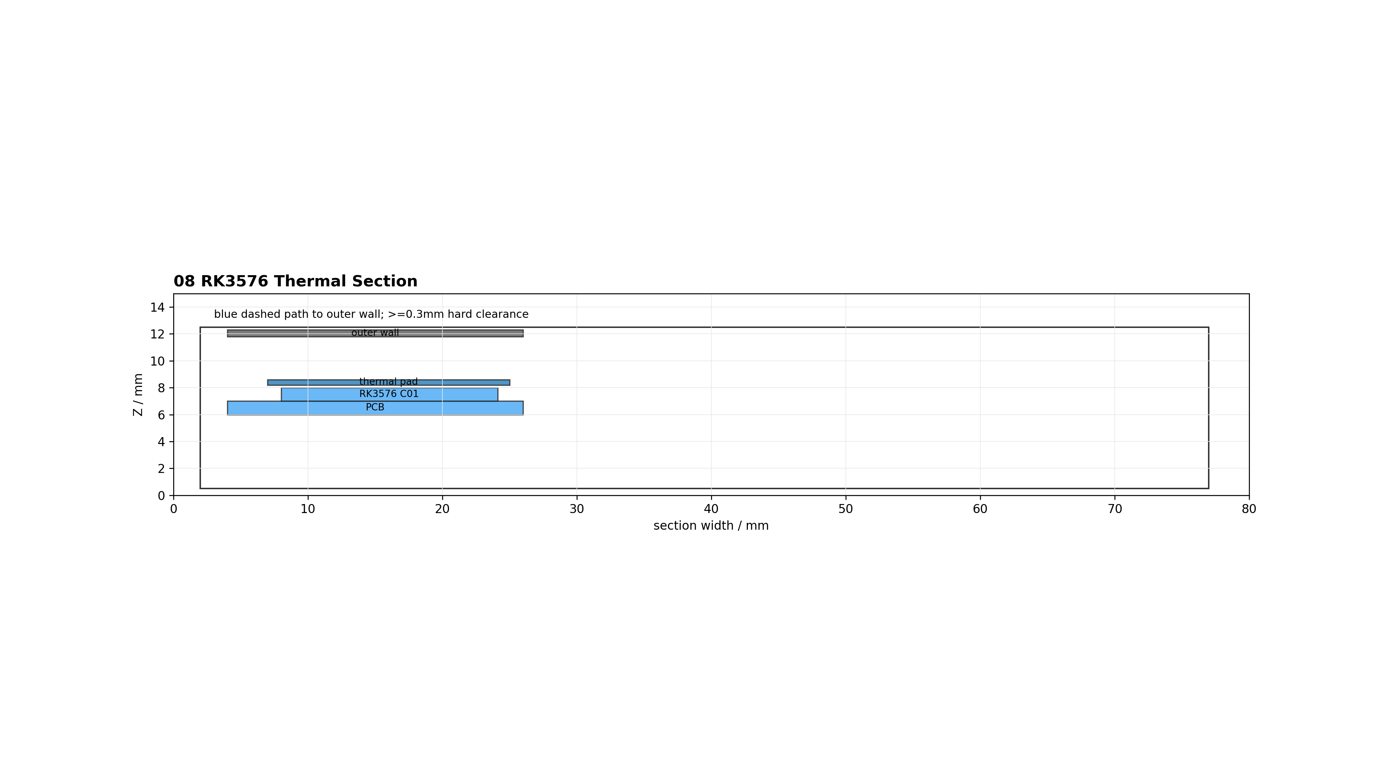
v2_chipdown/mechanical_3d/renders/08_soc_thermal_section.png
