lhongyi-ai/AI_Goggles/v2_chipdown/reports/output/AI_Glasses_V2_Phase1_5_Floorplan.png

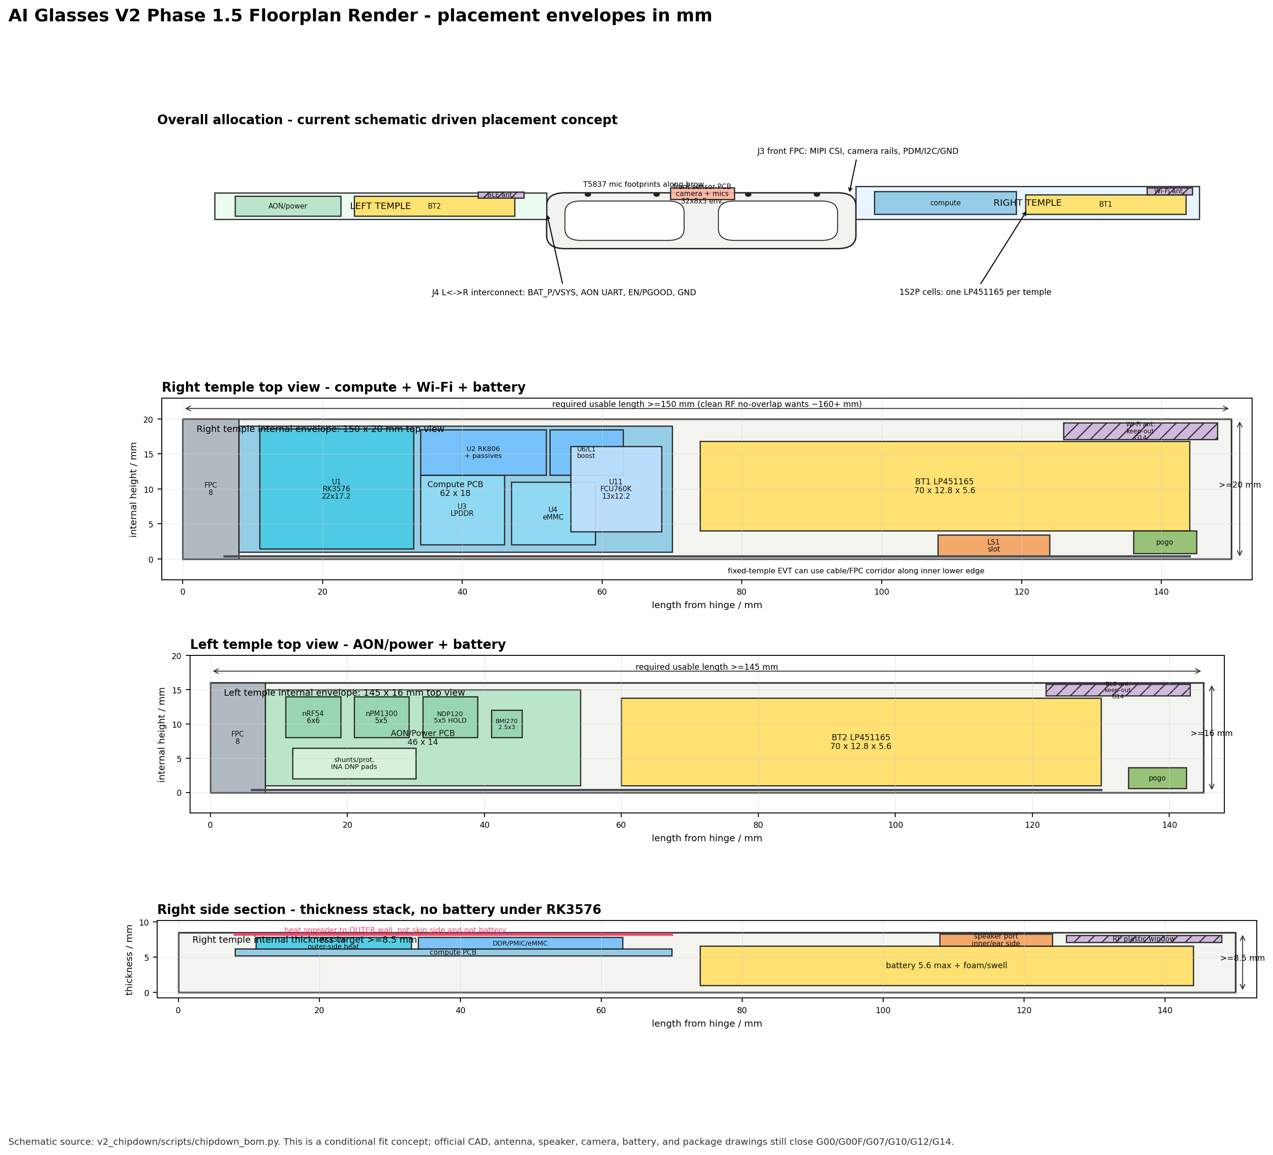
v2_chipdown/reports/output/AI_Glasses_V2_Phase1_5_Floorplan.png
