lhongyi-ai/AI_Goggles/v2_chipdown/reports/output/mechanical_freeze/AI_Glasses_V2_3_Mechanical_Views.png

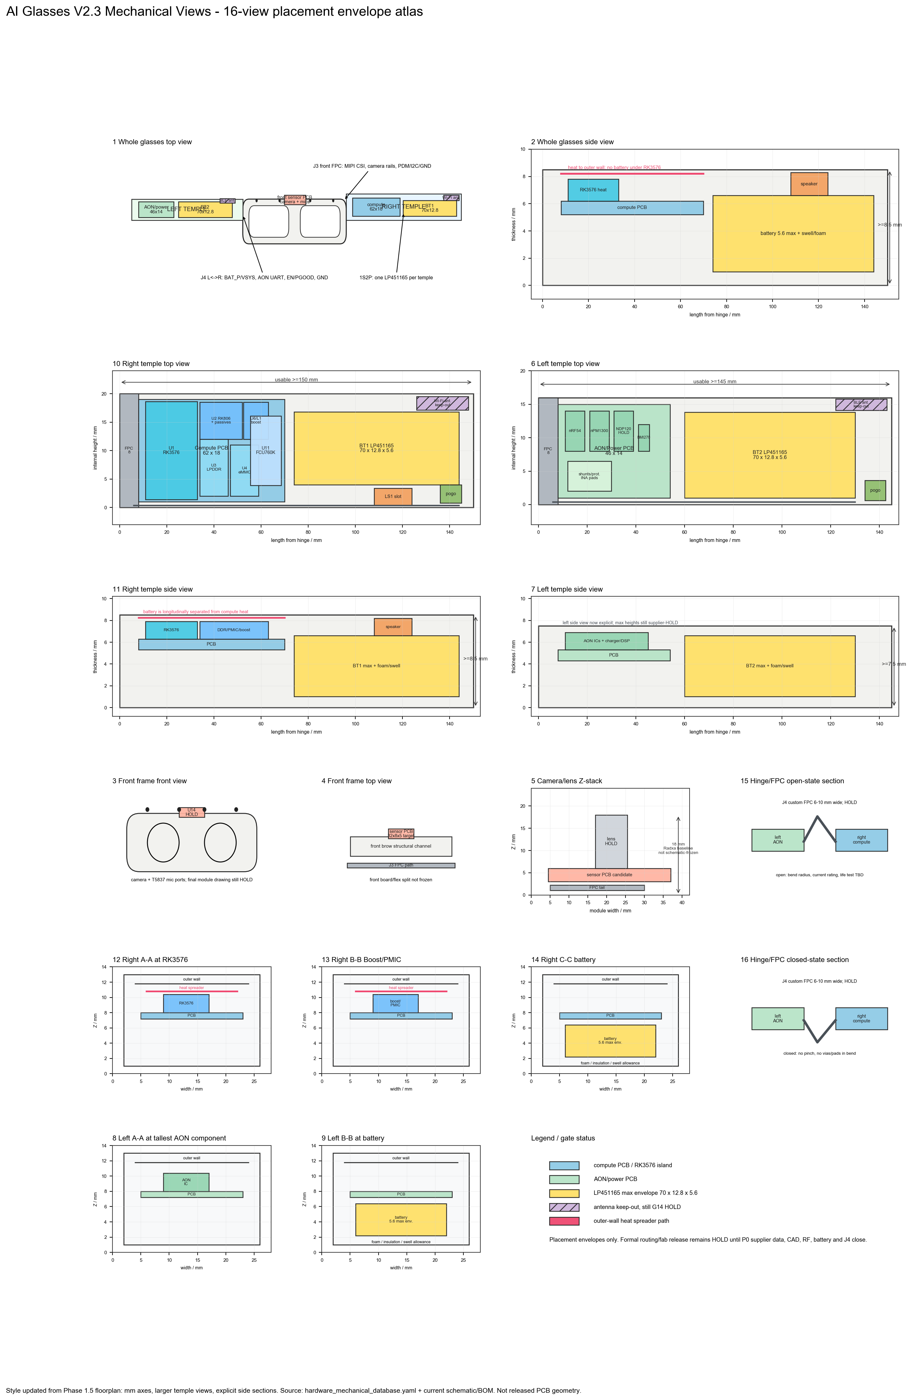
v2_chipdown/reports/output/mechanical_freeze/AI_Glasses_V2_3_Mechanical_Views.png
