lhongyi-ai/AI_Goggles/v2_chipdown/reports/output/mechanical_options/AI_Glasses_V2_Narrow_Temple_Option1_Complete.png

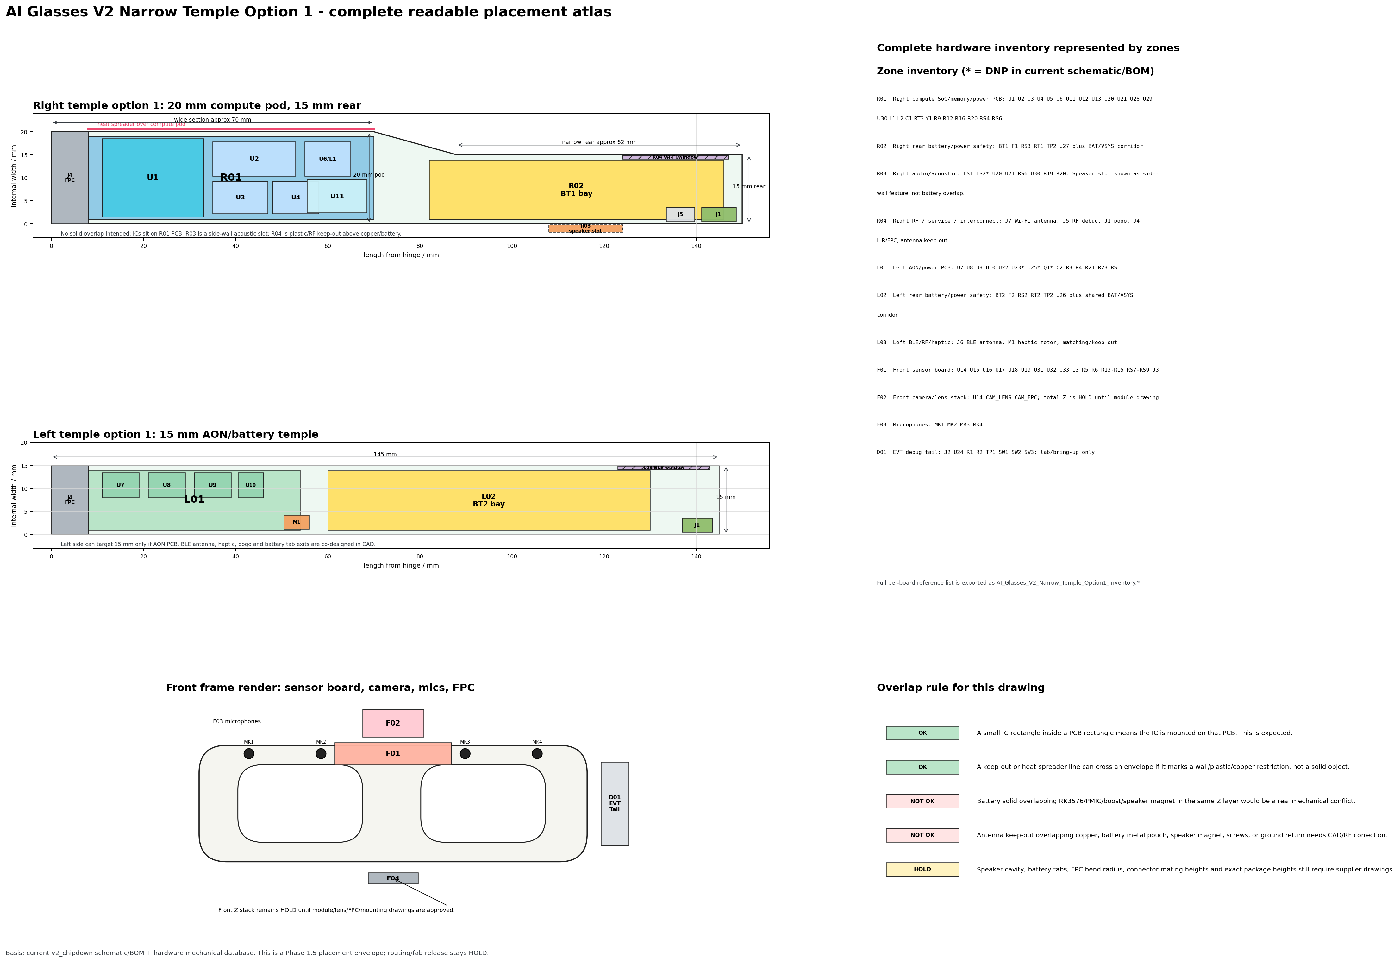
v2_chipdown/reports/output/mechanical_options/AI_Glasses_V2_Narrow_Temple_Option1_Complete.png
