lhongyi-ai/AI_Goggles/docs/passive_bom_freeze_2026-06-28.md

# Passive BOM Freeze

Date: 2026-06-28

Status: `PRE_LAYOUT_PASSIVE_BOM_REVIEW`

Scope: all schematic R/C/L/FB/D passives plus MIPI/USB protection arrays `U2`, `U16`, `U5`.

## Summary

- Covered refs: 59
- LOCKED_CANDIDATE: 44
- PROCUREMENT_VERIFY: 9
- TUNE_OR_EVT_SELECT: 6

## Records

| Ref | Family | Value | Package | MPN | LCSC | Status |
| --- | --- | --- | --- | --- | --- | --- |
| `C1` | `C_10UF_BULK` | 10uF | 0805 / 2012 metric | `CL21A106KAYNNNE` | `C15850` | `LOCKED_CANDIDATE` |
| `C10` | `C_100NF_DECOUPLING` | 100nF | 0603 / 1608 metric | `CC0603KRX7R9BB104` | `C14663` | `LOCKED_CANDIDATE` |
| `C11` | `C_1UF_DECOUPLING` | 1uF | 0603 / 1608 metric | `CL10B105KO8NNNC` | `C15849` | `LOCKED_CANDIDATE` |
| `C13` | `C_100NF_DECOUPLING` | 100nF | 0603 / 1608 metric | `CC0603KRX7R9BB104` | `C14663` | `LOCKED_CANDIDATE` |
| `C14` | `C_100NF_DECOUPLING` | 100nF | 0603 / 1608 metric | `CC0603KRX7R9BB104` | `C14663` | `LOCKED_CANDIDATE` |
| `C15` | `C_10UF_BULK` | 10uF | 0805 / 2012 metric | `CL21A106KAYNNNE` | `C15850` | `LOCKED_CANDIDATE` |
| `C16` | `C_100NF_DECOUPLING` | 100nF | 0603 / 1608 metric | `CC0603KRX7R9BB104` | `C14663` | `LOCKED_CANDIDATE` |
| `C17` | `C_100NF_DECOUPLING` | 100nF | 0603 / 1608 metric | `CC0603KRX7R9BB104` | `C14663` | `LOCKED_CANDIDATE` |
| `C18` | `C_100NF_DECOUPLING` | 100nF | 0603 / 1608 metric | `CC0603KRX7R9BB104` | `C14663` | `LOCKED_CANDIDATE` |
| `C19` | `C_100NF_DECOUPLING` | 100nF | 0603 / 1608 metric | `CC0603KRX7R9BB104` | `C14663` | `LOCKED_CANDIDATE` |
| `C2` | `C_100NF_DECOUPLING` | 100nF | 0603 / 1608 metric | `CC0603KRX7R9BB104` | `C14663` | `LOCKED_CANDIDATE` |
| `C20` | `C_100NF_DECOUPLING` | 100nF | 0603 / 1608 metric | `CC0603KRX7R9BB104` | `C14663` | `LOCKED_CANDIDATE` |
| `C21` | `C_100NF_DECOUPLING` | 100nF | 0603 / 1608 metric | `CC0603KRX7R9BB104` | `C14663` | `LOCKED_CANDIDATE` |
| `C22` | `C_100NF_DECOUPLING` | 100nF | 0603 / 1608 metric | `CC0603KRX7R9BB104` | `C14663` | `LOCKED_CANDIDATE` |
| `C23` | `C_1NF_SPEAKER_EMI` | 1nF | 0603 / 1608 metric | `CC0603KRX7R9BB102` | `C1669` | `LOCKED_CANDIDATE` |
| `C24` | `C_1NF_SPEAKER_EMI` | 1nF | 0603 / 1608 metric | `CC0603KRX7R9BB102` | `C1669` | `LOCKED_CANDIDATE` |
| `C25` | `C25_C26_GNSS_PI_SHUNT_DNP` | DNP / tune | 0402 / 1005 metric | `DNP_TUNE_KIT` | `DNP_TUNE_KIT` | `TUNE_OR_EVT_SELECT` |
| `C26` | `C25_C26_GNSS_PI_SHUNT_DNP` | DNP / tune | 0402 / 1005 metric | `DNP_TUNE_KIT` | `DNP_TUNE_KIT` | `TUNE_OR_EVT_SELECT` |
| `C27` | `C27_GNSS_RF_DC_BLOCK` | 100pF initial / tune | 0402 / 1005 metric | `TUNE_OR_EVT_SELECT` | `TUNE_OR_EVT_SELECT` | `TUNE_OR_EVT_SELECT` |
| `C28` | `C_100NF_DECOUPLING` | 100nF | 0603 / 1608 metric | `CC0603KRX7R9BB104` | `C14663` | `LOCKED_CANDIDATE` |
| `C29` | `C_10UF_BULK` | 10uF | 0805 / 2012 metric | `CL21A106KAYNNNE` | `C15850` | `LOCKED_CANDIDATE` |
| `C3` | `C_10UF_BULK` | 10uF | 0805 / 2012 metric | `CL21A106KAYNNNE` | `C15850` | `LOCKED_CANDIDATE` |
| `C30` | `C_100NF_DECOUPLING` | 100nF | 0603 / 1608 metric | `CC0603KRX7R9BB104` | `C14663` | `LOCKED_CANDIDATE` |
| `C4` | `C_100NF_DECOUPLING` | 100nF | 0603 / 1608 metric | `CC0603KRX7R9BB104` | `C14663` | `LOCKED_CANDIDATE` |
| `C5` | `C_10UF_BULK` | 10uF | 0805 / 2012 metric | `CL21A106KAYNNNE` | `C15850` | `LOCKED_CANDIDATE` |
| `C6` | `C_100NF_DECOUPLING` | 100nF | 0603 / 1608 metric | `CC0603KRX7R9BB104` | `C14663` | `LOCKED_CANDIDATE` |
| `C7` | `C_22UF_VBAT_BULK` | 22uF | 0805 / 2012 metric | `CL21A226MAQNNNE` | `C45783` | `LOCKED_CANDIDATE` |
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
