lhongyi-ai/AI_Goggles/v2_chipdown/reports/engineering_reviews/assembly_tolerance_stack.md

# Assembly Tolerance Stack Review

Verdict: **HOLD**.

- Shell: wall thickness, draft, bosses, snap features and screw locations are not frozen.
- PCB: board thickness, copper stack, component-side allocation and solder height need CAD import.
- Battery: use 70 x 12.8 x 5.6 mm clearance envelope until supplier max/swell data arrives.
- Adhesive/foam: reserve compression range and avoid point loads on pouch cells.
- FPC: bend radius, stiffener, soldered areas and no-via dynamic zone must be defined.
- Connector: mating heights and contact side for J3/J4/J1/J5 must be included.
- Component height: no official package drawing means no Z-height freeze.
- Manufacturing tolerance: final fit must include worst-case shell + PCB + component + battery + adhesive stack.
