lhongyi-ai/AI_Goggles/v2_chipdown/reports/output/ai_glasses_v2_chipdown_schematic.pdf

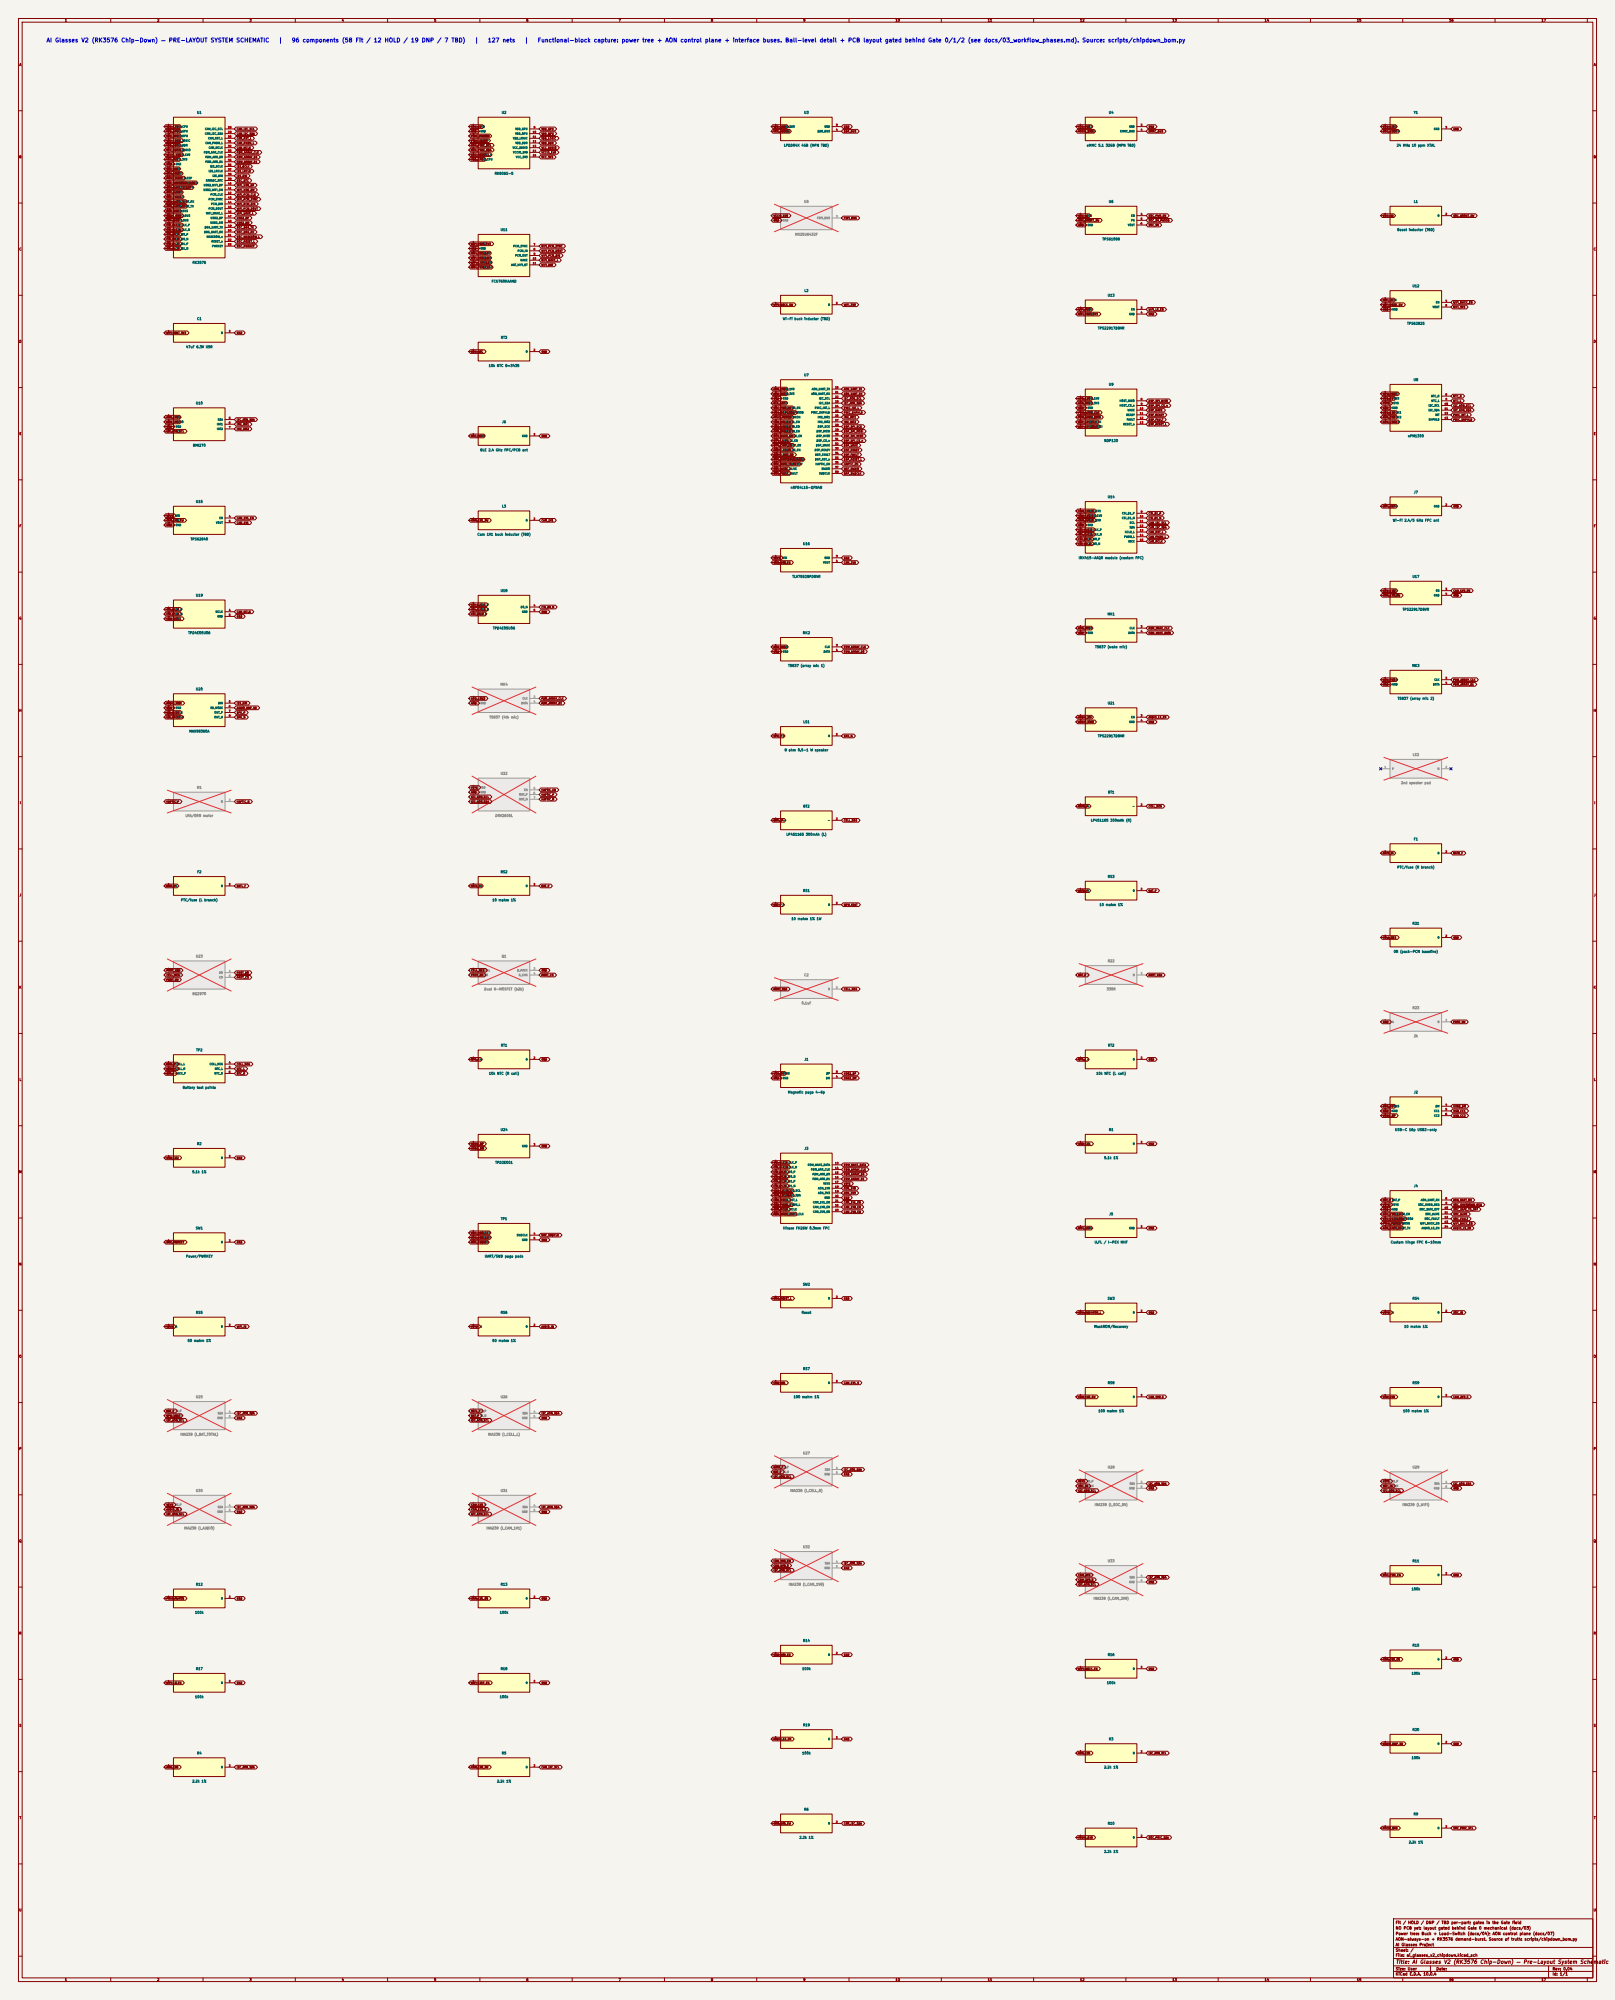
[picture p126: page 1]

eMMC 5.1 32GB (MPN TBD) VIN

2 L2 Wi-Fi buck inductor (TBD)

2 J7 Wi-Fi 2.4/5 GHz FPC ant DVDD_1V1

2 L3 Cam 1V1 buck inductor (TBD)

IMX415-AAQR module (custom FPC) VDD

Fit / HOLD / DNP / TBD per-part; gates in the Gate field
NO PCB yet: layout gated behind Gate 0 mechanical (docs/03)
Power tree: Buck + Load-Switch (docs/04); AON control plane (docs/07)
AON-always-on + RK3576 demand-burst. Source of truth: scripts/chipdown_bom.py
AI Glasses Project
Sheet: /
File: ai_glasses_v2_chipdown.kicad_sch
Title: AI Glasses V2 (RK3576 Chip-Down) — Pre-Layout System Schematic

Size: User | Rev: 0.04
KiCad E.D.A. 10.0.4 | Id: 1/1
