lhongyi-ai/AI_Goggles/v2_chipdown/reports/output/mechanical_freeze/AI_Glasses_V2_3_Mechanical_Views.pdf

## 1 Whole glasses top view

## 2 Whole glasses side view

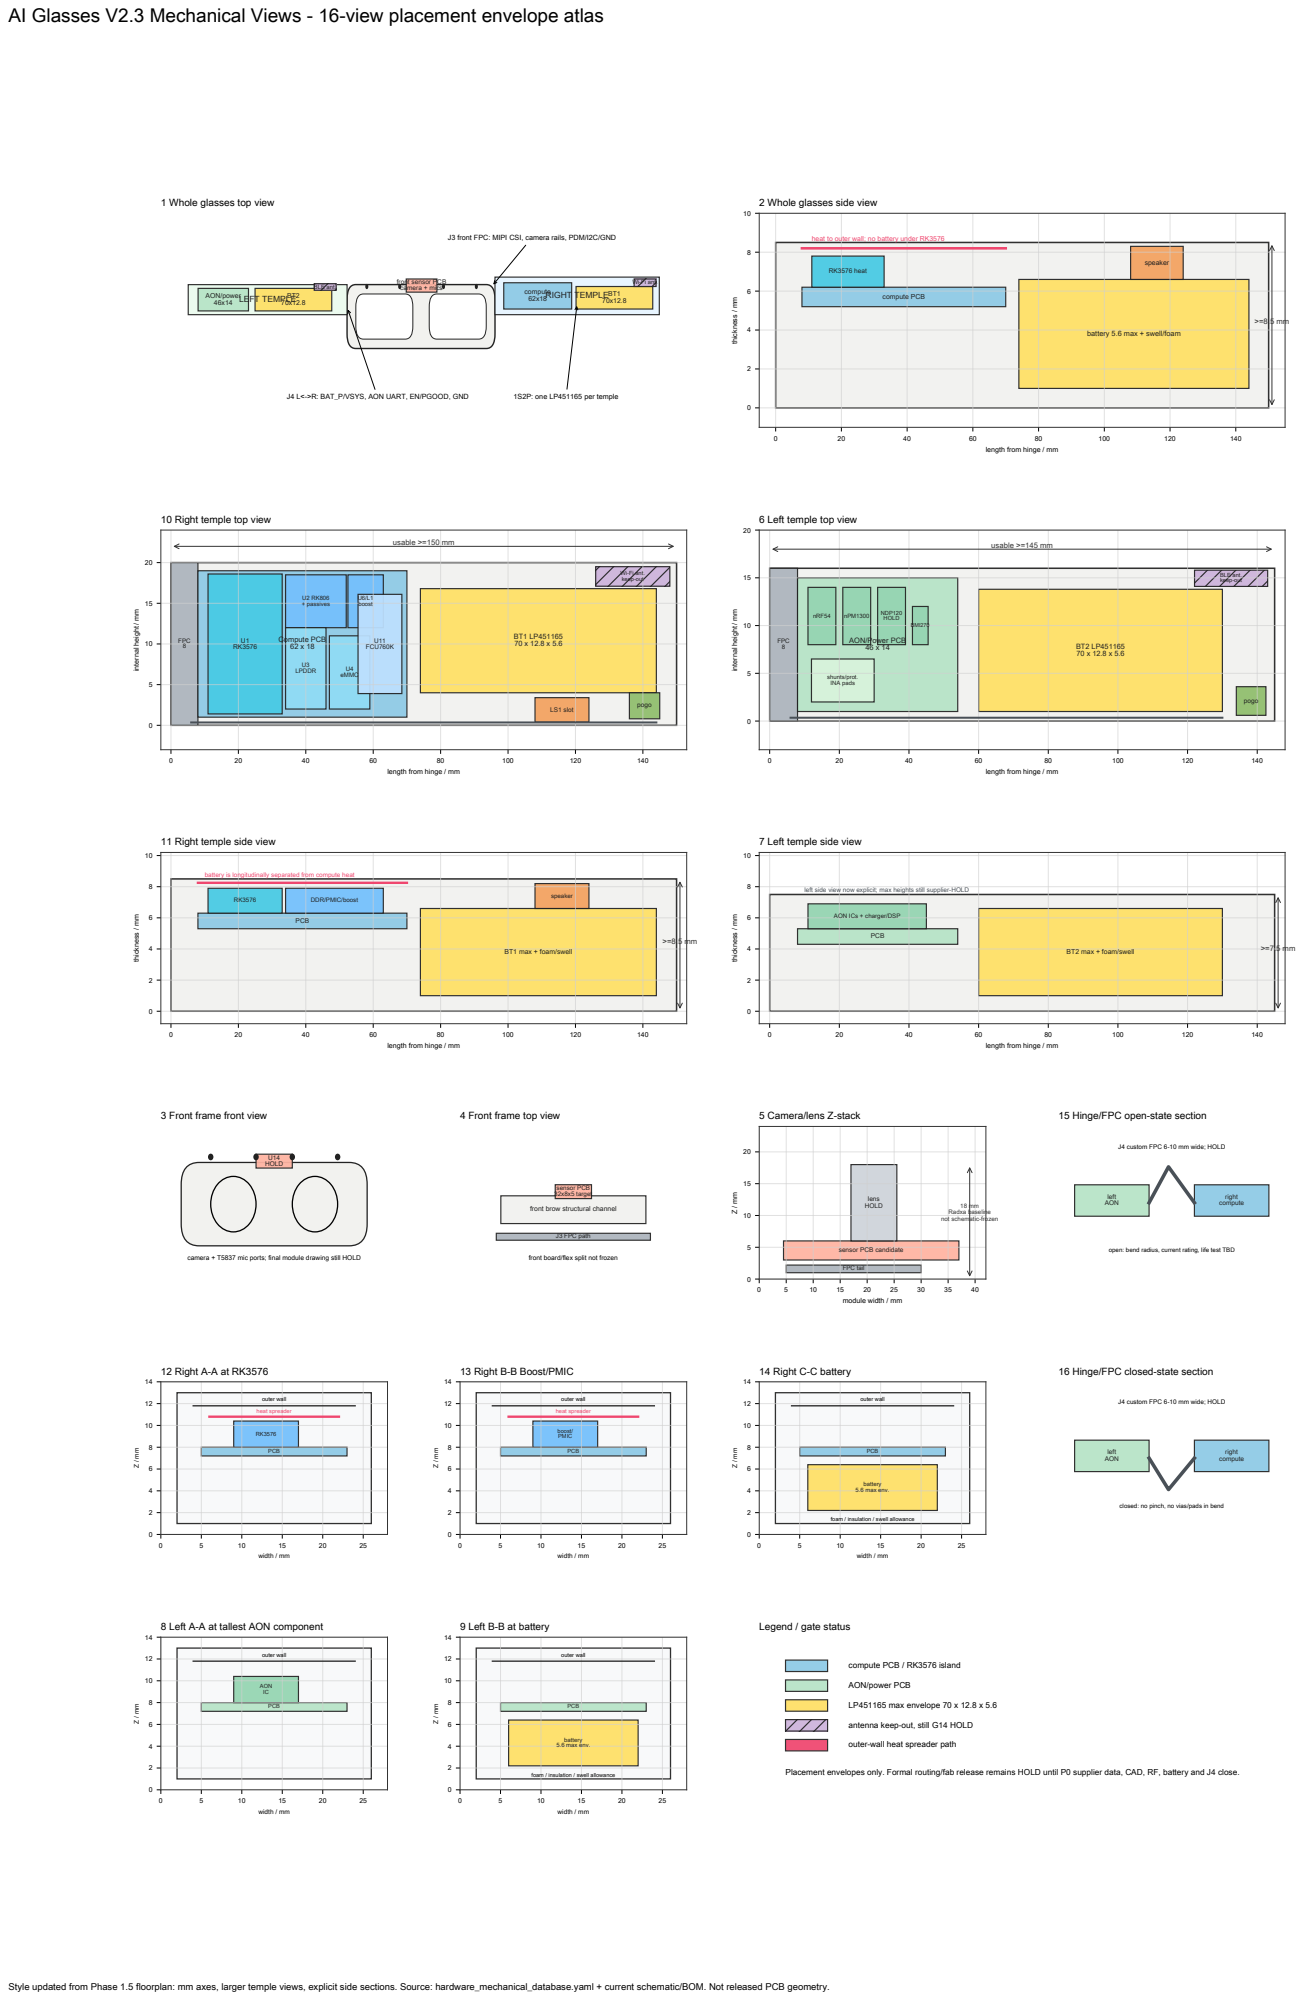
[picture p127: page 1]

AI Glasses V2.3 Mechanical Views - 16-view placement envelope atlas

J3 front FPC: MIPI CSI, camera rails, PDM/I2C/GND

heat to outer wall; no battery under RK3576

RK3576 heat | | | speaker

RIGHT TEMPLE LEFT TEMPLE

compute PCB

battery 5.6 max + swell/foam

length from hinge / mm

10 Right temple top view

6 Left temple top view

U2 RK806 + passives | U6/L1 boost | | | Wi-Fi ant. keep-out

nRF54 | nPM1300 NDP120 HOLD | BMI270 | | keep-out

FPC | Compute PCB U1 | | U11 | BT1 LP451165 70 x 12.8 x 5.6
8 RK3576 | 62 x 18 U3 LPDDR | FCU760K U4 eMMC

FPC 8 | AON/Power PCB 46 x 14 | | BT2 LP451165 70 x 12.8 x 5.6

shunts/prot. INA pads | | | | pogo

LS1 slot | pogo

11 Right temple side view

7 Left temple side view

battery is longitudinally separated from compute heat

left side view now explicit; max heights still supplier-HOLD

AON ICs + charger/DSP

3 Front frame front view

4 Front frame top view

15 Hinge/FPC open-state section

J4 custom FPC 6-10 mm wide; HOLD

sensor PCB
32x8x5 target
front brow structural channel

open: bend radius, current rating, life test TBD

camera + T5837 mic ports; final module drawing still HOLD

front board/flex split not frozen

16 Hinge/FPC closed-state section

closed: no pinch, no vias/pads in bend

foam / insulation / swell allowance

8 Left A-A at tallest AON component

compute PCB / RK3576 island
AON/power PCB
LP451165 max envelope 70 x 12.8 x 5.6
antenna keep-out, still G14 HOLD
outer-wall heat spreader path

Placement envelopes only. Formal routing/fab release remains HOLD until P0 supplier data, CAD, RF, battery and J4 close.

Style updated from Phase 1.5 floorplan: mm axes, larger temple views, explicit side sections. Source: hardware_mechanical_database.yaml + current schematic/BOM. Not released PCB geometry.
