lhongyi-ai/AI_Goggles/hardware/ai_glasses_carrier.kicad_sch

## KiCad design hardware/ai_glasses_carrier.kicad_sch (2026-07-02)

Schematic: ai_glasses_carrier.kicad_sch

Parts:
C1, C3, C5, C8, C15, C29: 10µF; C_0805_2012Metric
C2, C4, C6, C10, C13, C14, C16, C17, C18, C19, C20, C21, C22, C30: 100nF; C_0603_1608Metric
C7: 22µF; C_0805_2012Metric
C9, C11: 1µF; C_0603_1608Metric
C23, C24: 1nF; C_0603_1608Metric
C25, C26: π shunt (DNP,tune); C_0402_1005Metric
C27: DC-block (series,tune); C_0402_1005Metric
C28: 100nF (active-ant); C_0603_1608Metric
D1: LED Green; LED_0603_1608Metric
D2: LED Blue; LED_0603_1608Metric
D3: SMAJ5.0A (TVS); D_SMA
D4: ESD low-cap RF 0.3pF; D_SOD-882
FB1, FB2: Ferrite 600Ω@100MHz; L_0603_1608Metric
J1, J31, J32: DF40C-100DS-0.4V(51); Hirose_DF40C-100DS-0.4V_2x50_P0.4mm
J2: FH35C-31S-0.3SHW(50); FH35C-31S-0.3SHW_50
J3: JST-SH 2p (spkr); JST_SH_BM02B-SRSS-TB_1x02-1MP_P1.00mm_Vertical
J4: GCT USB4085 (USB2); USB_C_Receptacle_GCT_USB4085
J5: JST-PH 3p; JST_PH_S3B-PH-SM4-TB_1x03-1MP_P2.00mm_Horizontal
J6: JST-SH 2p; JST_SH_BM02B-SRSS-TB_1x02-1MP_P1.00mm_Vertical
J7: Header 1x4 2.54mm; PinHeader_1x04_P2.54mm_Vertical
J8: U.FL / IPEX; U.FL_Hirose_U.FL-R-SMT-1_Vertical
L1: 4.7µH; POWER_INDUCTOR_7X7_VERIFY
L2: RF choke (active-ant); L_0402_1005Metric
MK1, MK2: SPH0641LU4H-1; Knowles_LGA-5_3.5x2.65mm
R1, R2: 5.1k; R_0603_1608Metric
R3: 0R / shunt; R_2512_6332Metric
R4, R5: 1k; R_0603_1608Metric
R7, R8, R9, R10, R12, R13: 2.2k; R_0603_1608Metric
R11, R14, R15, R16: 10k; R_0603_1608Metric
R17: 10Ω (active-ant); R_0603_1608Metric
R18, R19, R20: 100k; R_0603_1608Metric
SW1, SW2, SW3: Tact SW SMD; SW_Push_1P1T_NO_CK_KMR2
TP1, TP2, TP3, TP4, TP5, TP6, TP7, TP8, TP9, TP10, TP11, TP12, TP13, TP14, TP15, TP16: TestPoint 1.0mm; TestPoint_Pad_D1.5mm
U2, U16: TPD4E05U06; USON-10_2.5x1.0mm_P0.5mm
U3: LP5907-3.3 (low-noise LDO); SOT-23-5
U4: MAX98357AETE+T; QFN-16-1EP_3x3mm_P0.5mm_EP1.45x1.45mm
U5: TPD2E009; SOT-553
U6: TPS61022 (Boost); Texas_RWU0007A_VQFN-7_2x2mm_P0.5mm
U7: BQ25180; Texas_DSBGA-12_1.36x1.86mm_Layout3x4_P0.5mm
U8: BQ29700; SOT-23-5
U9: MAX17048; DFN-8-1EP_2x3mm_P0.5mm_EP0.61x2.2mm
U10: ICM-42688-P; LGA-14_3x2.5mm_P0.5mm_LayoutBorder3x4y
U11: DRV2605L; MSOP-10_3x3mm_P0.5mm
U12: TLV75733 (LDO); SOT-23-5
U13: TLV75718 (LDO); SOT-23-5
U14: MAX-M10S-00B-01; ublox_MAX
U15: TPS25940 (e-fuse, opt); Texas_RGP0020H_VQFN-20-1EP_4x4mm_P0.5mm_EP2.4x2.4mm

Connections:
+1V8: C5.1, C6.1, C16.1, C22.1, J1.7 (+1V8 (P88/90)), J31.2 (P78 VREF→1V8), MK1.1 (VDD), MK2.1 (VDD), MK2.4 (SEL), R7.1, R8.1, R9.1, R10.1, R12.1, R13.1, R14.1, R15.1, R16.1, R18.1, R19.1, TP4.1, U10.1 (VDD), U13.3 (VOUT), U14.2 (V_IO)
+3V3: C3.1, C4.1, C14.1, C15.1, C21.1, J7.4 (VREF), R4.1, R5.1, R17.1, TP3.1, U12.3 (VOUT), U13.1 (VIN), U14.1 (VCC), U14.3 (V_BCKP)
+5V_SYS: C1.1, C2.1, C13.1, C20.1, C29.1, C30.1, J2.30 (30 VCC5V), J2.31 (31 VCC5V), J31.1 (P77-87 +5V), R3.2, TP2.1, U3.1 (VIN), U4.1 (VDD), U6.4 (FB), U11.1 (VDD), U12.1 (VIN)
+CAM_3V3: C8.1, C9.1, C10.1, J2.28 (28 VCC3.3V), J2.29 (29 VCC3.3V), U3.4 (VOUT)
+VBAT: C7.1, C18.1, C19.1, L1.1, R20.1, TP1.1, U6.1 (VIN), U7.2 (SYS), U8.3 (OUT), U9.1 (VDD), U9.2 (CELL)
BAT_NTC: J5.3 (NTC), R11.1, U7.4 (TS)
BOOST_EN: R20.2, U6.3 (EN)
BOOST_SW: L1.2, U6.2 (SW)
BT_nDIS: J31.27 (P91 BT_DIS), R19.2
CAM_I2C_SCL: J2.24 (24 SCL), J31.10 (P80 CAM_SCL), R7.2, TP8.1
CAM_I2C_SDA: J2.25 (25 SDA), J31.11 (P82 CAM_SDA), R8.2, TP9.1
CAM_MCLK: J1.5 (P59 CAM3_MCLK), J2.20 (20 MCLK)
CAM_PWR_EN: TP16.1, U3.2 (EN)
CAM_RST_n: J2.27 (27 RESET_N), J32.11 (P143 CAM3_GPIO)
CHG_INT_n: J31.19 (P37 CHG_INT), U7.7 (INT)
FUEL_I2C_SCL: J31.14 (P35 FUEL_SCL), R12.2, TP12.1, U7.5 (SCL), U9.3 (SCL)
FUEL_I2C_SDA: J31.15 (P36 FUEL_SDA), R13.2, TP13.1, U7.6 (SDA), U9.4 (SDA)
GND: C1.2, C2.2, C3.2, C4.2, C5.2, C6.2, C7.2, C8.2, C9.2, C10.2, C11.2, C13.2, C14.2, C15.2, C16.2, C17.2, C18.2, C19.2, C20.2, C21.2, C22.2, C23.2, C24.2, C25.2, C26.2, C28.2, C29.2, C30.2, D3.2, D4.2, J1.8 (GND), J2.1 (1 GND), J2.4 (4 GND), J2.7 (7 GND), J2.10 (10 GND), J2.13 (13 GND), J2.16 (16 GND), J2.19 (19 GND), J2.21 (21 GND), J4.2 (GND), J4.7 (SHLD), J7.3 (GND), J8.2 (GND), J31.3 (GND), J32.17 (GND), MK1.4 (SEL), MK1.5 (GND), MK2.5 (GND), R1.2, R2.2, R11.2, SW1.2, SW2.2, SW3.2, TP5.1, U2.7 (GND), U3.3 (GND), U4.2 (GND), U4.7 (GAIN), U5.3 (GND), U6.5 (GND), U7.8 (GND), U9.6 (GND), U10.2 (GND), U11.2 (GND), U12.2 (GND), U13.2 (GND), U14.4 (GND), U15.3 (GND), U16.5 (GND)
GNSS_ANT: C26.1, C27.2, D4.1, J8.1 (ANT), L2.1
GNSS_PPS: J31.8 (P40 GNSS_PPS), U14.7 (TIMEPULSE)
GNSS_RFIN: C25.1, C27.1, U14.9 (RF_IN)
GNSS_RST_n: J31.9 (P44 GNSS_RST), U14.8 (RESET_N)
GNSS_UART_RX: J31.7 (P45 GNSS_RX), U14.5 (TXD)
GNSS_UART_TX: J31.6 (P47 GNSS_TX), U14.6 (RXD)
IMU_I2C_SCL: J31.12 (P56 IMU_SCL), R9.2, TP10.1, U10.3 (SCL)
IMU_I2C_SDA: J31.13 (P58 IMU_SDA), R10.2, TP11.1, U10.4 (SDA)
IMU_INT1: J31.16 (P30 IMU_INT), U10.5 (INT1)
LED_PWR_A: D1.1 (A), R4.2
LED_PWR_n: D1.2 (K), J31.21 (P95 LED_PWR)
LED_STATUS_n: D2.2 (K), J31.22 (P21 LED_STAT)
LED_STAT_A: D2.1 (A), R5.2
LOW_BAT_INT_n: J31.20 (P39 LBAT_INT), U9.5 (ALRT)
MIPI_CSI3_CLK_N: J2.17 (17 MCN), J32.2 (P127 CSI3_CLKN), U2.2 (CLK_N)
MIPI_CSI3_CLK_P: J2.18 (18 MCP), J32.1 (P129 CSI3_CLKP), U2.1 (CLK_P)
MIPI_CSI3_D0_N: J2.14 (14 MDN1), J32.4 (P115 CSI3_D0N), U2.4 (D0_N)
MIPI_CSI3_D0_P: J2.15 (15 MDP1), J32.3 (P117 CSI3_D0P), U2.3 (D0_P)
MIPI_CSI3_D1_N: J2.11 (11 MDN2), J32.6 (P121 CSI3_D1N), U2.6 (D1_N)
MIPI_CSI3_D1_P: J2.12 (12 MDP2), J32.5 (P123 CSI3_D1P), U2.5 (D1_P)
MIPI_CSI3_D2_N: J2.5 (5 MDN3), J32.8 (P133 CSI3_D2N), U16.2 (D2_N)
MIPI_CSI3_D2_P: J2.6 (6 MDP3), J32.7 (P135 CSI3_D2P), U16.1 (D2_P)
MIPI_CSI3_D3_N: J2.2 (2 MDN4), J32.10 (P139 CSI3_D3N), U16.4 (D3_N)
MIPI_CSI3_D3_P: J2.3 (3 MDP4), J32.9 (P141 CSI3_D3P), U16.3 (D3_P)
PDM1_CLK: J32.14 (P96 PDM_CLK), MK1.2 (CLK), MK2.2 (CLK)
PDM1_DATA0: J32.15 (P94 PDM_D0), MK1.3 (DATA)
PDM1_DATA1: J32.16 (P111 PDM_D1), MK2.3 (DATA)
POWER_KEY: J31.25 (P99 PWR_KEY), R16.2, SW3.1
RECOVERY_n: J31.23 (P93 RECOVERY), R14.2, SW1.1, TP15.1
RESET_n: J31.24 (P92 RESET), R15.2, SW2.1, TP14.1
SAI1_BCLK: J1.1 (P25 SAI_BCLK), U4.3 (BCLK)
SAI1_LRCK: J1.2 (P19 SAI_LRCK), U4.4 (LRC)
SAI1_SDO: J1.3 (P29 SAI_SDO), U4.5 (DIN)
SPKR_EN_n: J1.6 (P96 SPK_EN), U4.6 (SD)
SPK_N_F: C24.1, FB2.2, J3.2 (SPK-)
SPK_OUT_N: FB2.1, U4.9 (OUT-)
SPK_OUT_P: FB1.1, U4.8 (OUT+)
SPK_P_F: C23.1, FB1.2, J3.1 (SPK+)
UART_DBG_RX: J7.2 (RX), J31.5 (P51 DBG_RX), TP7.1
UART_DBG_TX: J7.1 (TX), J31.4 (P55 DBG_TX), TP6.1
USB_CC1: J4.5 (CC1), R1.1
USB_CC2: J4.6 (CC2), R2.1
USB_DM: J4.4 (DM), J32.13 (P103 USB_DM), U5.2 (DM)
USB_DP: J4.3 (DP), J32.12 (P105 USB_DP), U5.1 (DP)
USB_VBUS: C11.1, C17.1, D3.1, J4.1 (VBUS), U7.1 (IN), U15.1 (IN), U15.2 (EN)
VBAT_N: J5.2 (BAT-), U8.2 (VM)
VBAT_P: J5.1 (BAT+), U7.3 (BAT), U8.1 (VDD)
VBUS_PROT: R3.1, U15.4 (OUT)
VIB_EN: J31.18 (P34 VIB_EN), U11.4 (EN)
VIB_OUT_N: J6.2 (M-), U11.6 (OUT-)
VIB_OUT_P: J6.1 (M+), U11.5 (OUT+)
VIB_PWM: J31.17 (P48 VIB_PWM), U11.3 (IN)
V_ANT_BIAS: C28.1, L2.2, R17.2
WL_nDIS: J31.26 (P89 WL_DIS), R18.2

Notes on the sheet:
AI Glasses Carrier V1 (RK3576/CM4) — EVT Schematic | 102 components | CM4 pin assignment is REVIEW/verified; pre-layout gates remain (see config/cm4_v1_pin_assignment.yaml)
