lhongyi-ai/AI_Goggles/v2_chipdown/hardware/ai_glasses_v2_chipdown.kicad_sch

## KiCad design v2_chipdown/hardware/ai_glasses_v2_chipdown.kicad_sch (2026-07-02)

Schematic: ai_glasses_v2_chipdown.kicad_sch

Parts:
BT1: LP451165 300mAh (R)
BT2: LP451165 300mAh (L)
C1: 47uF 6.3V X5R
F1: PTC/fuse (R branch)
F2: PTC/fuse (L branch)
J1: CCP P2578MP01-06C180HT
J2: USB-C 16p USB2-only
J3: Hirose FH26W-33S-0.3SHW(97)
J5: U.FL / I-PEX MHF RF test connector; not fitted
J6: FCU760K ANT_BT DNP test pad; not fitted
J7: Taoglas FXP840.07.0055B
L1: Coilcraft XGL4020-102MEC 1.0uH
L2: Wi-Fi buck inductor (TBD)
L3: Cam 1V1 buck inductor (TBD)
LS1: CUI CMS-15113-078SP-67
LS2: 2nd speaker pad; not fitted
M1: LRA/ERM motor; not fitted
MK1: T5837 (wake mic)
MK2: T5837 (array mic 1)
MK3: T5837 (array mic 2)
MK4: T5837 (4th mic); not fitted
PCM1: Supplier 1S2P pack PCM + protection FETs
R1, R2: 5.1k 1%
R3, R4, R5, R6, R9, R10: 2.2k 1%
R11, R12, R13, R14, R15, R16, R17, R18, R19, R20: 100k
RS1: 10 mohm 1% 1W
RS2, RS3, RS4: 10 mohm 1%
RS5, RS6: 50 mohm 1%
RS7, RS8, RS9: 100 mohm 1%
RT1: 10k NTC B=3435 1% (R cell)
RT2: 10k NTC B=3435 1% (L cell)
RT3: 10k NTC B=3435
SW1: Power/PWRKEY
SW2: Reset
SW3: MaskROM/Recovery
TP1: UART/SWD pogo pads
TP2: Battery test points
U1: RK3576
U2: RK806S-5 QFN68 7x7x0.90mm
U3: Samsung K4U6E3S4AA-MGCL
U4: Samsung KLMAG1JENB-B041
U5: MX25U6432F; not fitted
U6: TPS61088
U7: nRF54L15-QFN48
U8: nPM1300
U9: NDP120
U10: BMI270
U11: FCU760KAAMD
U12: TPS62825
U13, U17, U21: TPS22917DBVR
U14: Sony IMX415-AAQR-C custom module
U15: TPS62840
U16: TLV75529PDRVR
U18, U19, U34: TPD4E05U06
U20: MAX98360A
U22: DRV2605L; not fitted
U24: TPD2E001
U25: INA238 (I_BAT_TOTAL); not fitted
U26: INA238 (I_CELL_L); not fitted
U27: INA238 (I_CELL_R); not fitted
U28: INA238 (I_SOC_5V); not fitted
U29: INA238 (I_WIFI); not fitted
U30: INA238 (I_AUDIO); not fitted
U31: INA238 (I_CAM_1V1); not fitted
U32: INA238 (I_CAM_1V8); not fitted
U33: INA238 (I_CAM_2V9); not fitted
U35: BQ25895
U36: 5V input eFuse/OVP (MPN TBD)
Y1: 24 MHz 10 ppm XTAL

Connections:
AON_1V8: R3.1 (A), R4.1 (A), U7.1 (VDD_1V8), U8.5 (BUCK1), U9.1 (VDD_1V8), U10.1 (VDD), U10.2 (VDDIO), U17.1 (VIN)
AON_3V3: MK1.1 (VDD), MK2.1 (VDD), MK3.1 (VDD), U7.2 (VDD_3V3), U8.6 (BUCK2), U9.2 (VDD_3V3)
AON_LSW2: MK4.1 (VDD), U8.7 (LSW2)
AON_UART_RX: U1.18 (AON_UART_TX), U7.21 (AON_UART_RX)
AON_UART_TX: U1.17 (AON_UART_RX), U7.20 (AON_UART_TX)
AUDIO_AMP_SD: R20.1 (A), U7.15 (AMP_SD), U20.6 (SD_MODE)
AUDIO_IN: RS6.2 (B), U21.1 (VIN), U30.2 (IN_N)
AUDIO_LS_EN: R19.1 (A), U7.14 (AUDIO_LS_EN), U21.3 (EN)
AUDIO_PWR: U20.1 (VDD), U21.2 (VOUT)
BATL_F: F2.2 (B), RS2.1 (A), U26.1 (IN_P)
BATL_P: BT2.1 (+), F2.1 (A), TP2.1 (CELL_L)
BATR_F: F1.2 (B), RS3.1 (A), U27.1 (IN_P)
BATR_P: BT1.1 (+), F1.1 (A), TP2.2 (CELL_R)
BAT_P: PCM1.1 (PACK_PLUS), RS1.1 (A), RS2.2 (B), RS3.2 (B), TP2.3 (PACK_P), U25.1 (IN_P), U26.2 (IN_N), U27.2 (IN_N)
BLE_ANT: J6.1 (ANT), U11.12 (ANT_BT_DNP)
CAM_1V1: L3.2 (B), RS7.1 (A), U15.5 (VOUT), U31.1 (IN_P)
CAM_1V1_EN: R13.1 (A), U7.8 (CAM_1V1_EN), U15.4 (EN)
CAM_1V1_S: J3.2 (2_DVDD), RS7.2 (B), U14.1 (DVDD_1V1), U31.2 (IN_N)
CAM_1V1_SW: L3.1 (A), U15.2 (SW)
CAM_1V8_EN: R14.1 (A), U7.9 (CAM_1V8_EN), U17.3 (EN)
CAM_1V8_S: J3.6 (6_IOVDD), RS8.2 (B), U14.2 (IOVDD_1V8), U32.2 (IN_N)
CAM_1V8_SW: R5.1 (A), R6.1 (A), RS8.1 (A), U17.2 (VOUT), U32.1 (IN_P)
CAM_2V9: RS9.1 (A), U16.4 (VOUT), U33.1 (IN_P)
CAM_2V9_EN: R15.1 (A), U7.10 (CAM_2V9_EN), U16.2 (EN)
CAM_2V9_S: J3.4 (4_AVDD), RS9.2 (B), U14.3 (AVDD_2V9), U33.2 (IN_N)
CAM_I2C_SCL: J3.10 (10_I2C_SCL), R5.2 (B), U1.32 (CAM_I2C_SCL), U14.15 (SCL)
CAM_I2C_SDA: J3.11 (11_I2C_SDA), R6.2 (B), U1.33 (CAM_I2C_SDA), U14.16 (SDA)
CAM_MCLK: J3.8 (8_MCLK), U1.36 (CAM_MCLK), U14.19 (INCK), U19.4 (MCLK)
CAM_MODULE_ID: J3.31 (31_MODULE_ID), U14.20 (MODULE_ID)
CAM_PWDN_L: J3.13 (13_PWDN), U1.35 (CAM_PWDN_L), U14.18 (PWDN_L)
CAM_RST_L: J3.12 (12_RESET_N), U1.34 (CAM_RST_L), U14.17 (XCLR_L), U19.3 (RST)
CELL_NEG: BT1.2 (-), BT2.2 (-), PCM1.3 (CELL_MINUS), TP2.4 (CELL_NEG)
CHG_CE_L: U7.27 (CHG_CE_L), U35.9 (CE_L)
CHG_INT_L: U7.26 (CHG_INT_L), U35.8 (INT_L)
CHG_PG_L: U7.28 (CHG_PG_L), U35.10 (PG_L)
CSI_CLK_N: J3.16 (16_MIPI_CLK_N), U1.23 (CSI_CLK_N), U14.6 (CSI_CLK_N), U18.2 (CLK_N)
CSI_CLK_P: J3.17 (17_MIPI_CLK_P), U1.22 (CSI_CLK_P), U14.5 (CSI_CLK_P), U18.1 (CLK_P)
CSI_D0_N: J3.19 (19_MIPI_D0_N), U1.25 (CSI_D0_N), U14.8 (CSI_D0_N), U18.4 (D0_N)
CSI_D0_P: J3.20 (20_MIPI_D0_P), U1.24 (CSI_D0_P), U14.7 (CSI_D0_P), U18.3 (D0_P)
CSI_D1_N: J3.22 (22_MIPI_D1_N), U1.27 (CSI_D1_N), U14.10 (CSI_D1_N), U19.2 (D1_N)
CSI_D1_P: J3.23 (23_MIPI_D1_P), U1.26 (CSI_D1_P), U14.9 (CSI_D1_P), U19.1 (D1_P)
CSI_D2_N: J3.25 (25_MIPI_D2_N), U1.29 (CSI_D2_N), U14.12 (CSI_D2_N), U34.2 (D2_N)
CSI_D2_P: J3.26 (26_MIPI_D2_P), U1.28 (CSI_D2_P), U14.11 (CSI_D2_P), U34.1 (D2_P)
CSI_D3_N: J3.28 (28_MIPI_D3_N), U1.31 (CSI_D3_N), U14.14 (CSI_D3_N), U34.4 (D3_N)
CSI_D3_P: J3.29 (29_MIPI_D3_P), U1.30 (CSI_D3_P), U14.13 (CSI_D3_P), U34.3 (D3_P)
DDR_BUS: U1.19 (DDR_BUS), U3.4 (DDR_BUS)
DSP_FAULT: U7.38 (DSP_FAULT), U9.12 (FAULT)
DSP_READY: U7.37 (DSP_READY), U9.11 (READY)
DSP_RESET_L: U7.39 (DSP_RST_n), U9.13 (RESET_n)
DSP_SPI_CS_n: U7.35 (DSP_CS_n), U9.9 (HOST_CS_n)
DSP_SPI_MISO: U7.34 (DSP_MISO), U9.8 (HOST_MISO)
DSP_SPI_MOSI: U7.33 (DSP_MOSI), U9.7 (HOST_MOSI)
DSP_SPI_SCK: U7.32 (DSP_SCK), U9.6 (HOST_SCK)
DSP_WAKE: U7.36 (DSP_WAKE), U9.10 (WAKE)
EMMC_BUS: U1.20 (EMMC_BUS), U4.4 (EMMC_BUS)
FSPI_BUS: U1.21 (FSPI_BUS), U5.3 (FSPI_BUS)
GND: C1.2 (B), J1.1 (GND1), J1.4 (GND2), J2.2 (GND), J3.1 (1_GND), J3.3 (3_GND), J3.5 (5_GND), J3.7 (7_GND), J3.9 (9_GND), J3.15 (15_GND), J3.18 (18_GND), J3.21 (21_GND), J3.24 (24_GND), J3.27 (27_GND), J3.30 (30_GND), J3.33 (33_GND), J5.2 (GND), J6.2 (GND), J7.2 (GND), MK1.2 (GND), MK2.2 (GND), MK3.2 (GND), MK4.2 (GND), PCM1.2 (PACK_MINUS), R1.2 (B), R2.2 (B), R11.2 (B), R12.2 (B), R13.2 (B), R14.2 (B), R15.2 (B), R16.2 (B), R17.2 (B), R18.2 (B), R19.2 (B), R20.2 (B), RT1.2 (B), RT2.2 (B), RT3.2 (B), SW1.2 (B), SW2.2 (B), SW3.2 (B), TP1.5 (GND), U1.9 (GND), U2.2 (GND), U3.3 (GND), U4.3 (GND), U5.2 (GND), U6.3 (GND), U7.3 (GND), U8.4 (GND), U9.3 (GND), U10.3 (GND), U11.2 (GND), U12.3 (GND), U13.4 (GND), U14.4 (GND), U15.3 (GND), U16.3 (GND), U17.4 (GND), U18.5 (GND), U19.5 (GND), U20.2 (GND), U21.4 (GND), U22.2 (GND), U24.3 (GND), U25.5 (GND), U26.5 (GND), U27.5 (GND), U28.5 (GND), U29.5 (GND), U30.5 (GND), U31.5 (GND), U32.5 (GND), U33.5 (GND), U34.5 (GND), U35.4 (GND), U36.3 (GND), Y1.3 (GND)
HAPTIC_EN: U7.40 (HAPTIC_EN), U22.5 (EN)
HAPTIC_N: M1.2 (N), U22.7 (OUT_N)
HAPTIC_P: M1.1, U22.6 (OUT_P)
I2C_AON_SCL: R3.2 (B), U7.22 (I2C_SCL), U8.10 (I2C_SCL), U10.4 (SCL), U22.3 (SCL), U25.3 (SCL), U26.3 (SCL), U27.3 (SCL), U28.3 (SCL), U29.3 (SCL), U30.3 (SCL), U31.3 (SCL), U32.3 (SCL), U33.3 (SCL), U35.5 (SCL)
I2C_AON_SDA: R4.2 (B), U7.23 (I2C_SDA), U8.11 (I2C_SDA), U10.5 (SDA), U22.4 (SDA), U25.4 (SDA), U26.4 (SDA), U27.4 (SDA), U28.4 (SDA), U29.4 (SDA), U30.4 (SDA), U31.4 (SDA), U32.4 (SDA), U33.4 (SDA), U35.6 (SDA)
I2S_BCLK: U1.40 (I2S_BCLK), U20.3 (BCLK)
I2S_DIN: U1.42 (I2S_DIN), U20.5 (DIN)
I2S_LRCLK: U1.41 (I2S_LRCLK), U20.4 (LRCLK)
IMU_INT1: U7.30 (IMU_INT1), U10.6 (INT1)
IMU_INT2: U7.31 (IMU_INT2), U10.7 (INT2)
NPM_VBAT: RS1.2 (B), U8.1 (VBAT), U25.2 (IN_N), U35.3 (BAT)
NRF_SWDCLK: TP1.4 (SWDCLK), U7.42 (SWDCLK)
NRF_SWDIO: TP1.3 (SWDIO), U7.41 (SWDIO)
NTC_L: PCM1.5 (NTC2_OR_ID), RT2.1 (A), TP2.5 (NTC_L), U8.9 (NTC_L)
NTC_R: PCM1.4 (NTC1), RT1.1 (A), TP2.6 (NTC_R), U8.8 (NTC_R), U35.7 (TS)
PDM_ARRAY_CLK: MK2.3 (CLK), MK3.3 (CLK), MK4.3 (CLK), U1.37 (PDM_ARR_CLK)
PDM_ARRAY_D0: MK2.4 (DATA), U1.38 (PDM_ARR_D0)
PDM_ARRAY_D1: MK3.4 (DATA), MK4.4 (DATA), U1.39 (PDM_ARR_D1)
PDM_WAKE_CLK: MK1.3 (CLK), U9.4 (PDM_CLK)
PDM_WAKE_DATA: MK1.4 (DATA), U9.5 (PDM_DATA)
PMIC_INT_L: U7.24 (PMIC_INT_L), U8.12 (INT)
PMIC_PWRON: R12.1 (A), U2.3 (PWRON), U7.7 (PMIC_PWRON)
PMIC_SHPHLD: U7.25 (PMIC_SHPHLD), U8.13 (SHPHLD)
PMIC_SLEEP: U1.12 (PMIC_SLEEP), U2.4 (SLEEP)
SOC_5V: U2.1 (VIN), U6.6 (VOUT)
SOC_5V_PGOOD: U6.5 (PG), U7.6 (SOC_5V_PGOOD)
SOC_ALIVE: U1.15 (ALIVE), U7.18 (SOC_ALIVE)
SOC_BOOST_SW: L1.2 (B), U6.2 (SW)
SOC_DBG_RX: TP1.2 (SOC_RX), U1.54 (DBG_UART_RX)
SOC_DBG_TX: TP1.1 (SOC_TX), U1.53 (DBG_UART_TX)
SOC_FAULT: U1.16 (FAULT), U7.19 (SOC_FAULT)
SOC_IN: L1.1 (A), RS4.2 (B), U6.1 (VIN), U28.2 (IN_N)
SOC_MASKROM_L: SW3.1 (A), U1.55 (MASKROM_n)
SOC_NTC: RT3.1 (A), U1.43 (SARADC_NTC)
SOC_PMIC_SCL: R9.2 (B), U2.5 (I2C_SCL)
SOC_PMIC_SDA: R10.2 (B), U2.6 (I2C_SDA)
SOC_PWRKEY: SW1.1 (A), U1.57 (PWRKEY)
SOC_PWR_EN: R11.1 (A), U6.4 (EN), U7.5 (SOC_PWR_EN)
SOC_RESET_L: SW2.1 (A), U1.56 (RESET_n), U2.7 (RESET_n)
SOC_SAFE_TO_OFF: U1.14 (SAFE_TO_OFF), U7.17 (SOC_SAFE_OFF)
SOC_SHUTDOWN_REQ: U1.13 (SHUTDOWN_REQ), U7.16 (SOC_SHDN_REQ)
SOC_XIN: U1.10 (XIN), Y1.1 (XIN)
SOC_XOUT: U1.11 (XOUT), Y1.2 (XOUT)
SPK_N: LS1.2 (N), U20.8 (OUT_N)
SPK_P: LS1.1, U20.7 (OUT_P)
USB2_DM: J1.2 (USB_DN), J2.4 (DM), U1.52 (USB2_DM), U24.2 (DM)
USB2_DP: J1.3 (USB_DP), J2.3 (DP), U1.51 (USB2_DP), U24.1 (DP)
USB_5V: U8.2 (VBUS), U35.1 (VBUS), U36.2 (OUT)
USB_CC1: J2.5 (CC1), R1.1 (A)
USB_CC2: J2.6 (CC2), R2.1 (A)
VBUS_FAULT_L: U7.29 (VBUS_FAULT_L), U36.4 (FLT_L)
VBUS_RAW: J1.5 (VBUS1), J1.6 (VBUS2), J2.1 (VBUS), U36.1 (IN)
VCCIO_1V8: R9.1 (A), R10.1 (A), U1.7 (VCCIO_1V8), U2.14 (VCCIO_1V8), U4.2 (VCCQ), U5.1 (VCC)
VCC_3V3: U1.8 (VCC_3V3), U2.15 (VCC_3V3), U4.1 (VCC)
VCC_DDRIO: U1.6 (VCC_DDRIO), U2.13 (VCC_DDRIO), U3.2 (VDDQ)
VDD_CPU: U1.1 (VDD_CPU), U2.8 (VDD_CPU)
VDD_DDR: U1.5 (VDD_DDR), U2.12 (VDD_DDR), U3.1 (VDD_DDR)
VDD_GPU: U1.2 (VDD_GPU), U2.9 (VDD_GPU)
VDD_LOGIC: U1.4 (VDD_LOGIC), U2.11 (VDD_LOGIC)
VDD_NPU: U1.3 (VDD_NPU), U2.10 (VDD_NPU)
VSYS: RS4.1 (A), RS5.1 (A), RS6.1 (A), U8.3 (VSYS), U15.1 (VIN), U16.1 (VIN), U22.1 (VDD), U28.1 (IN_P), U29.1 (IN_P), U30.1 (IN_P), U35.2 (SYS)
WIFI_3V3: L2.2 (B), U12.5 (VOUT), U13.1 (VIN)
WIFI_ANT: J5.1 (SIG), J7.1 (ANT), U11.11 (ANT_WIFI_BT)
WIFI_BUCK_EN: R16.1 (A), U7.11 (WIFI_BUCK_EN), U12.4 (EN)
WIFI_BUCK_SW: L2.1 (A), U12.2 (SW)
WIFI_CHIP_EN: R18.1 (A), U7.13 (WIFI_CHIP_EN), U11.5 (CHIP_EN)
WIFI_IN: RS5.2 (B), U12.1 (VIN), U29.2 (IN_N)
WIFI_LS_EN: R17.1 (A), U7.12 (WIFI_LS_EN), U13.3 (EN)
WIFI_PCM_CLK: U1.46 (PCM_CLK), U11.6 (PCM_CLK)
WIFI_PCM_DIN: U1.48 (PCM_DIN), U11.9 (PCM_OUT)
WIFI_PCM_DOUT: U1.49 (PCM_DOUT), U11.8 (PCM_IN)
WIFI_PCM_SYNC: U1.47 (PCM_SYNC), U11.7 (PCM_SYNC)
WIFI_USB_DM: U1.45 (USB2_WIFI_DM), U11.4 (USB_DM)
WIFI_USB_DP: U1.44 (USB2_WIFI_DP), U11.3 (USB_DP)
WIFI_VBAT_3V3: C1.1 (A), U11.1 (VBAT), U13.2 (VOUT)
WIFI_WAKE_L: U1.50 (WIFI_WAKE_L), U11.10 (WAKE)

Notes on the sheet:
AI Glasses V2 (RK3576 Chip-Down) — PRE-LAYOUT SYSTEM SCHEMATIC | 93 components (57 Fit / 18 HOLD / 16 DNP / 2 TBD) | 133 nets | Functional-block capture: power tree + AON control plane + interface buses. Ball-level detail + PCB layout gated behind Gate 0/1/2 (see docs/03_workflow_phases.md). Source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
