lhongyi-ai/AI_Goggles/v2_chipdown/scripts/generate_mechanical_floorplan.py

#!/usr/bin/env python3
"""Generate the V2 Phase 1.5 mechanical/electrical floorplan artifacts.

This is an engineering placement-envelope render, not industrial design.
It keeps dimensions tied to the current V2 schematic/BOM source of truth and
records where real CAD/supplier data must still close the gate.
"""
from __future__ import annotations

import os
import sys
from pathlib import Path

ROOT = Path(__file__).resolve().parents[2]
OUT = ROOT / "v2_chipdown" / "reports"
OUT_IMG = OUT / "output"

os.environ.setdefault("MPLCONFIGDIR", "/private/tmp/ai_glasses_v2_mplcache")

import matplotlib

matplotlib.use("Agg")
import matplotlib.pyplot as plt
from matplotlib import patches

sys.path.insert(0, str(ROOT / "v2_chipdown" / "scripts"))
from chipdown_bom import COMPONENTS  # noqa: E402


COLORS = {
    "frame": "#f2f2ef",
    "pcb_compute": "#8ecae6",
    "pcb_aon": "#b7e4c7",
    "sensor": "#ffb4a2",
    "battery": "#ffe066",
    "rf": "#cdb4db",
    "speaker": "#f4a261",
    "fpc": "#adb5bd",
    "power": "#90be6d",
    "heat": "#ef476f",
    "keepout": "#dee2e6",
    "outline": "#242424",
}


def comp(ref: str):
    return next(c for c in COMPONENTS if c.ref == ref)


PARTS = {
    "soc": comp("U1"),
    "pmic": comp("U2"),
    "lpddr": comp("U3"),
    "emmc": comp("U4"),
    "wifi": comp("U11"),
    "imu": comp("U10"),
    "bat_r": comp("BT1"),
    "bat_l": comp("BT2"),
    "speaker": comp("LS1"),
    "camera": comp("U14"),
    "ndp": comp("U9"),
    "mcu": comp("U7"),
    "charger": comp("U8"),
}


FIT_LIMITS = {
    "right_usable_length_mm": 150.0,
    "right_front_internal_height_mm": 20.0,
    "right_internal_thickness_mm": 8.5,
    "left_usable_length_mm": 145.0,
    "left_front_internal_height_mm": 16.0,
    "left_internal_thickness_mm": 7.5,
    "battery_max_envelope_mm": (70.0, 12.8, 5.6),
    "front_sensor_envelope_mm": (32.0, 8.0, 5.0),
}


def add_box(ax, x, y, w, h, label, color, *, hatch=None, lw=1.1, alpha=0.92, fontsize=7):
    rect = patches.Rectangle(
        (x, y),
        w,
        h,
        facecolor=color,
        edgecolor=COLORS["outline"],
        linewidth=lw,
        hatch=hatch,
        alpha=alpha,
    )
    ax.add_patch(rect)
    if label:
        ax.text(
            x + w / 2,
            y + h / 2,
            label,
            ha="center",
            va="center",
            fontsize=fontsize,
            color="#111111",
            linespacing=1.05,
        )
    return rect


def add_dim(ax, x0, y0, x1, y1, text, *, fontsize=7):
    ax.annotate(
        "",
        xy=(x1, y1),
        xytext=(x0, y0),
        arrowprops=dict(arrowstyle="<->", lw=0.8, color="#333333"),
    )
    ax.text((x0 + x1) / 2, (y0 + y1) / 2, text, fontsize=fontsize, ha="center", va="bottom")


def style_mm_axis(ax, title):
    ax.set_title(title, loc="left", fontsize=11, fontweight="bold")
    ax.set_aspect("equal", adjustable="box")
    ax.grid(True, linewidth=0.25, color="#d0d0d0")
    ax.tick_params(labelsize=7)
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
